chadlindell/terrascry/hirt/docs/build-guide/electronics.qmd

---
title: "Electronics and Circuits"
---

## Overview {#sec-electronics-overview}

This section consolidates all circuit designs for the HIRT system, including the MIT (Magneto-Inductive Tomography) circuits, ERT (Electrical Resistivity Tomography) circuits, and base hub electronics. The design uses **centralized electronics with passive probes**: all active components reside in the surface hub, while probes contain only coils and electrodes.

This architecture offers significant advantages: lower per-probe cost, easier maintenance, better reliability (passive probes are more robust), centralized firmware updates, and simplified probe construction. The trade-off is increased cabling complexity for the multi-probe harness.

::: {.callout-tip}
## Hardware Documentation Reference

Complete circuit schematics and detailed design notes are maintained in the hardware documentation:

- **MIT Circuit:** `/hardware/schematics/electronics/mit-circuit.md` - Full TX/RX chain design with component values
- **ERT Circuit:** `/hardware/schematics/electronics/ert-circuit.md` - Howland current source and measurement circuits
- **Base Hub Circuit:** `/hardware/schematics/electronics/base-hub-circuit.md` - Central hub electronics integration
- **Block Diagrams:** `/hardware/schematics/electronics/probe-electronics-block.md` - System-level block diagrams

The diagrams in this section provide conceptual overviews; refer to the hardware schematics for exact component values and PCB layout guidance.
:::

## System Block Diagram {#sec-system-block}

```{python}
#| label: fig-system-block-elec
#| fig-cap: "Complete HIRT system architecture showing the central electronics hub, zone wiring strategy, and passive probe connections. All signal processing occurs in the hub; probes are purely passive sensors."
#| fig-width: 11
#| fig-height: 7
#| code-fold: true

import sys; sys.path.insert(0, '..') if '..' not in sys.path else None
from diagrams.circuits import create_system_block_diagram
import matplotlib.pyplot as plt
from PIL import Image

buf = create_system_block_diagram()
img = Image.open(buf)
plt.figure(figsize=(11, 7))
plt.imshow(img)
plt.axis('off')
plt.tight_layout()
plt.show()
```

The central hub contains: (1) MCU for control and DSP, (2) MIT transmitter chain (DDS + power driver), (3) MIT receiver chain (preamp + instrumentation amplifier + ADC), (4) ERT current source and voltage measurement, and (5) high-density analog multiplexers. These connect via DB25 trunk cables to passive **Zone Hubs**, which then distribute signals to individual probes.

## MIT Transmit (TX) Chain {#sec-mit-tx}

```{python}
#| label: fig-mit-tx-chain
#| fig-cap: "MIT transmitter signal chain from MCU through DDS, filtering, and power driver to the TX coil. Operating frequency range is 2-50 kHz."
#| fig-width: 10
#| fig-height: 4
#| code-fold: true

import sys; sys.path.insert(0, '..') if '..' not in sys.path else None
from diagrams.circuits import create_mit_tx_chain
import matplotlib.pyplot as plt
from PIL import Image

buf = create_mit_tx_chain()
img = Image.open(buf)
plt.figure(figsize=(10, 4))
plt.imshow(img)
plt.axis('off')
plt.tight_layout()
plt.show()
```

## DDS Sine Generator {#sec-dds}

The transmit chain begins with a Direct Digital Synthesis (DDS) generator, the **AD9833**. This IC provides a highly precise sine wave output from 0.1 Hz to 12.5 MHz with 28-bit frequency resolution. Its compact MSOP-10 footprint and low power consumption make it ideal for the 2-50 kHz HIRT operating range.

| Parameter | Specification |
|---|---|
| Part Number | **AD9833BRMZ** |
| Frequency Range | 0 Hz to 12.5 MHz |
| Output Level | 0.6 V p-p sine wave |
| Interface | SPI (3-wire) |
| Resolution | 28-bit frequency, 12-bit phase |
| Power Supply | 2.3-5.5V, 12.65 mW typical |

: AD9833 DDS Generator Specifications. {#tbl-dds-specs}

## TX Power Driver {#sec-tx-driver}

The DDS output is buffered by a **Texas Instruments OPA2186** precision operational amplifier. This component is selected for its zero-drift architecture and ultra-low quiescent current (**90 µA** **(Modeled)**), which ensures high precision and extended battery life for the hub while maintaining rail-to-rail output for the TX coil drive.

| Parameter | OPA2186 Specification |
|---|---|
| Quiescent Current | **90 µA** |
| Drift | **0.04 µV/°C** (Zero-Drift) |
| Offset Voltage | 10 µV |
| Power Supply | 4.5V to 36V |

: TX Driver Op-Amp Specifications. {#tbl-tx-driver}

## MIT Receive (RX) Chain {#sec-mit-rx}

```{python}
#| label: fig-mit-rx-chain
#| fig-cap: "MIT receiver signal chain. The updated 2026 architecture uses the AD8421 for ultra-low noise preamplification (3 nV/rtHz), followed by the integrated AD7124-8 AFE."
#| fig-width: 10
#| fig-height: 4
#| code-fold: true

import sys; sys.path.insert(0, '..') if '..' not in sys.path else None
from diagrams.circuits import create_mit_rx_chain
import matplotlib.pyplot as plt
from PIL import Image

buf = create_mit_rx_chain()
img = Image.open(buf)
plt.figure(figsize=(10, 4))
plt.imshow(img)
plt.axis('off')
plt.tight_layout()
plt.show()
```

## RX Preamplifier (AD8421) {#sec-rx-preamp}

The receiver front-end utilizes the **Analog Devices AD8421**. This high-speed instrumentation amplifier features an exceptionally low input voltage noise floor of **3 nV/$\sqrt{\mathrm{Hz}}$** **(Modeled)**. This performance characteristic is essential for resolving the weak secondary magnetic fields generated by subsurface targets in the MIT tomography process.

| Parameter | Specification |
|---|---|
| Component | **AD8421** |
| Input Noise | **3 nV/$\sqrt{\mathrm{Hz}}$** **(Modeled)** |
| Bandwidth (G=10) | 10 MHz |
| Slew Rate | 35 V/µs |
| Supply Current | 2.0 mA |

: RX Preamplifier Specifications. {#tbl-preamp-specs}

### Zero-Drift Alternative: INA188 {#sec-ina188-alternative}

For applications prioritizing DC stability over AC noise floor, the **Texas Instruments INA188** provides a zero-drift alternative to the AD8421.

| Parameter | AD8421 | INA188 | Trade-off |
|---|---|---|---|
| Noise Floor | **3 nV/$\sqrt{\mathrm{Hz}}$** | 12 nV/$\sqrt{\mathrm{Hz}}$ | AD8421 superior for AC |
| Offset Drift | 0.6 µV/°C | **0.2 µV/°C** | INA188 superior for DC |
| 1/f Noise | Present | **Eliminated** | INA188 better at DC |
| Supply Current | 2.0 mA | 1.4 mA | Similar |

: AD8421 vs INA188 comparison. {#tbl-preamp-comparison}

**Recommendation:** For HIRT's MIT operating range (2-50 kHz), the AD8421's ultra-low broadband noise provides better SNR than the INA188's zero-drift architecture. Use the INA188 only if your application requires DC-accurate measurements or operates below 100 Hz.

### Noise Floor Measurement Conditions {#sec-noise-conditions}

The AD8421's specified noise floor of **3 nV/$\sqrt{\mathrm{Hz}}$** is achieved under specific measurement conditions. Field performance depends on several factors:

| Condition | Specification | Field Typical | Impact on SNR |
|---|---|---|---|
| Bandwidth | 1-50 kHz (HIRT operating range) | 2-50 kHz | ~100 nV RMS integrated |
| Temperature | 25°C reference | -10 to +40°C | ±10% variation |
| Cable length | <1 m bench test | 3-5 m probe cable | +20-50% noise pickup |
| Averaging | 100-sample mean | 16-64 samples typical | Improves by $\sqrt{N}$ |

: Noise floor measurement conditions and field impact. {#tbl-noise-conditions}

**Integrated Noise Calculation:** For a 1-50 kHz bandwidth (49 kHz span), the theoretical integrated input-referred noise is:

$$V_{n,rms} = 3\ \text{nV}/\sqrt{\text{Hz}} \times \sqrt{49,000\ \text{Hz}} \approx 100\ \text{nV RMS}$$

This represents the *design target* under controlled conditions. Field measurements typically show 150-300 nV RMS due to cable capacitance, EMI pickup, and connector losses.

::: {.callout-note}
## Performance Claim Context

The ~100 nV noise floor is a **design target** based on component specifications and bench measurements. Actual field performance varies with environmental conditions and cable routing. For planning purposes, assume 200-300 nV RMS input-referred noise in typical outdoor conditions.
:::

## Signal Conditioning and Gain Stage {#sec-signal-conditioning}

Following the AD8421 preamplifier, the signal passes through additional gain and filtering stages before reaching the ADC. An instrumentation amplifier (INA128) provides adjustable gain to match signal levels to the ADC input range. The total signal chain gain is typically 800-1000x, bringing microvolt-level coil signals up to the millivolt range required by the ADC.

## Signal Level Progression {#sec-signal-levels}

```{python}
#| label: fig-signal-level
#| fig-cap: "Signal level progression through the MIT RX chain. The signal starts at approximately 1 uV at the coil and is amplified to 0.8 mV at the ADC input. The noise floor also rises but at a slower rate, maintaining adequate SNR."
#| fig-width: 10
#| fig-height: 5
#| code-fold: true

import sys; sys.path.insert(0, '..') if '..' not in sys.path else None
from diagrams.circuits import create_signal_level_progression
import matplotlib.pyplot as plt
from PIL import Image

buf = create_signal_level_progression()
img = Image.open(buf)
plt.figure(figsize=(10, 5))
plt.imshow(img)
plt.axis('off')
plt.tight_layout()
plt.show()
```

## Lock-In Detection {#sec-lockin}

Lock-in detection is essential for extracting weak MIT signals from noise. The HIRT system uses **digital lock-in detection** implemented in the MCU, which offers flexibility, software configurability, and no analog drift. The technique multiplies the received signal by reference sine and cosine waveforms at the excitation frequency, then low-pass filters to extract the in-phase (I) and quadrature (Q) components.

```{python}
#| label: fig-lockin-detection
#| fig-cap: "Digital lock-in detection block diagram. The RX signal is multiplied by reference sine (Q-channel) and cosine (I-channel) signals, then filtered and integrated. Amplitude A = sqrt(I^2 + Q^2) and phase Phi = atan2(Q,I) are computed from the I/Q outputs."
#| fig-width: 10
#| fig-height: 5
#| code-fold: true

import sys; sys.path.insert(0, '..') if '..' not in sys.path else None
from diagrams.circuits import create_lock_in_detection_diagram
import matplotlib.pyplot as plt
from PIL import Image

buf = create_lock_in_detection_diagram()
img = Image.open(buf)
plt.figure(figsize=(10, 5))
plt.imshow(img)
plt.axis('off')
plt.tight_layout()
plt.show()
```

The lock-in algorithm provides exceptional noise rejection (> 40 dB improvement) by responding only to signals at the exact reference frequency. This allows detection of MIT signals buried deep in noise, critical for weak responses from distant or low-conductivity targets.

## Digital Lock-In Algorithm {#sec-lockin-algorithm}

```c
// Simplified digital lock-in implementation
float I_sum = 0, Q_sum = 0;
for (int i = 0; i < N_samples; i++) {
    float sample = read_adc();
    float ref_I = sin(2 * PI * f * i / Fs);
    float ref_Q = cos(2 * PI * f * i / Fs);
    I_sum += sample * ref_I;
    Q_sum += sample * ref_Q;
}
float amplitude = sqrt(I_sum*I_sum + Q_sum*Q_sum) / N_samples;
float phase = atan2(Q_sum, I_sum);
```

## ERT Current Source (Howland Pump) {#sec-ert-current}

The ERT subsystem injects controlled current into the ground through electrode rings and measures the resulting voltage distribution. The current source uses a **Howland current pump** topology, which provides high output impedance (>1 M-ohm) and stable current regardless of load variations.

```{python}
#| label: fig-ert-current-source
#| fig-cap: "Howland current pump circuit for ERT measurements. When R1=R2=R3=R4, the output current is I_out = V_in / R_sense, independent of load impedance. A precision 2.5V reference (REF5025) provides stable input voltage."
#| fig-width: 10
#| fig-height: 6
#| code-fold: true

import sys; sys.path.insert(0, '..') if '..' not in sys.path else None
from diagrams.circuits import create_ert_current_source
import matplotlib.pyplot as plt
from PIL import Image

buf = create_ert_current_source()
img = Image.open(buf)
plt.figure(figsize=(10, 6))
plt.imshow(img)
plt.axis('off')
plt.tight_layout()
plt.show()
```

| Parameter | Specification |
|---|---|
| Output Current | 0.5-2 mA (adjustable) |
| Current Accuracy | +/- 5% |
| Compliance Voltage | +/- 10V minimum |
| Output Impedance | > 1 M-ohm |
| Load Range | 100 ohm - 10 k-ohm |
| Polarity Reversal | Programmable (0.5 Hz) |

: ERT Current Source Specifications. {#tbl-ert-current}

### Compliance Voltage vs Load {#sec-ert-compliance}

The +/-10V compliance voltage determines the maximum load impedance at each current setting. Operators should select current levels based on expected soil resistivity to ensure adequate measurement headroom:

| Max Current | Max Load at 10V | Typical Application |
|---|---|---|
| 2.0 mA | 5 k-ohm | Low resistivity soil (<100 ohm-m) |
| 1.0 mA | 10 k-ohm | Medium resistivity (100-500 ohm-m) |
| 0.5 mA | 20 k-ohm | High resistivity (>500 ohm-m) |

: ERT current vs load compliance limits. Higher resistivity soils require lower current to stay within compliance voltage. {#tbl-ert-compliance}

::: {.callout-warning}
## Compliance Limit Warning

If the load impedance exceeds the compliance limit for the selected current, the current source will saturate and actual injected current will be less than commanded. The ERT firmware monitors this condition and flags affected measurements. Reduce current setting or improve electrode contact if compliance warnings occur frequently.
:::

## Polarity Reversal {#sec-polarity-reversal}

Electrode polarization causes measurement drift in DC systems. To mitigate this, HIRT reverses the current polarity every 2 seconds using a DPDT relay (G5V-2-H1) or solid-state switch (ADG1219). Positive and negative measurements are averaged to cancel polarization effects.

```{python}
#| label: fig-polarity-reversal
#| fig-cap: "ERT polarity reversal circuit using a DPDT relay. The relay alternates current direction between Ring A and Ring B every 2 seconds, eliminating electrode polarization artifacts from the measurement."
#| fig-width: 8
#| fig-height: 5
#| code-fold: true

import sys; sys.path.insert(0, '..') if '..' not in sys.path else None
from diagrams.circuits import create_ert_polarity_reversal
import matplotlib.pyplot as plt
from PIL import Image

buf = create_ert_polarity_reversal()
img = Image.open(buf)
plt.figure(figsize=(8, 5))
plt.imshow(img)
plt.axis('off')
plt.tight_layout()
plt.show()
```

## ADC Interface {#sec-adc}

```{python}
#| label: fig-adc-interface
#| fig-cap: "AD7124-8 ADC interface showing differential analog inputs for MIT and ERT signals, SPI connection to MCU, and integrated reference. The integrated AFE, 24-bit resolution, and three power modes provide excellent dynamic range with minimal external components."
#| fig-width: 9
#| fig-height: 5
#| code-fold: true

import sys; sys.path.insert(0, '..') if '..' not in sys.path else None
from diagrams.circuits import create_adc_interface_diagram
import matplotlib.pyplot as plt
from PIL import Image

buf = create_adc_interface_diagram()
img = Image.open(buf)
plt.figure(figsize=(9, 5))
plt.imshow(img)
plt.axis('off')
plt.tight_layout()
plt.show()
```

The HIRT Rev B design uses the **Analog Devices AD7124-8** as the primary ADC. This integrated Analog Front End (AFE) dramatically reduces external component count compared to the legacy ADS1256, while providing superior power management for field deployment.

| Parameter | AD7124-8 Specification |
|---|---|
| Resolution | 24 bits |
| Sample Rate | Up to 19.2 kSPS |
| Noise | 24 nV RMS (at low output rates) |
| Interface | SPI |
| Integrated Features | Rail-to-rail buffer, PGA (1-128x), reference buffers |
| Power Modes | Full (970 µA), Mid (660 µA), **Low (255 µA)** **(Modeled)** |
| Input Channels | 8 differential or 15 single-ended |

: AD7124-8 ADC Specifications (Rev B Primary). {#tbl-adc-specs}

**Migration Note (Rev A to Rev B):** The AD7124-8 replaces the ADS1256 as the recommended ADC. Key advantages:

- **Integrated AFE:** Internal rail-to-rail buffer and reference buffers eliminate ~6 external components
- **Power efficiency:** Low-power mode (~255 µA) vs ADS1256 (~36 mW) enables significantly longer battery life
- **Comparable noise:** 24 nV RMS achievable with fewer external noise sources

The ADS1256 remains documented for legacy builds (see [Legacy Components](#sec-legacy-components)).

## Multiplexer Switching {#sec-multiplexer}

With up to 24 probes in a typical array, the HIRT system requires a scalable multiplexing strategy. The design uses **CD74HC4067** 16:1 analog multiplexers controlled by MCU GPIO pins. Each TX and RX signal path has its own multiplexer, allowing independent selection of transmit and receive probes. For arrays exceeding 16 probes, cascaded multiplexers can be used.

```{python}
#| label: fig-mux-switching
#| fig-cap: "Multiplexer switching topology for probe selection. Separate TX and RX multiplexers allow any TX-RX probe combination to be measured. MCU GPIO controls multiplexer address lines (A0-A2)."
#| fig-width: 10
#| fig-height: 6
#| code-fold: true

import sys; sys.path.insert(0, '..') if '..' not in sys.path else None
from diagrams.circuits import create_multiplexer_switching_diagram
import matplotlib.pyplot as plt
from PIL import Image

buf = create_multiplexer_switching_diagram()
img = Image.open(buf)
plt.figure(figsize=(10, 6))
plt.imshow(img)
plt.axis('off')
plt.tight_layout()
plt.show()
```

## Power Distribution {#sec-power}

```{python}
#| label: fig-power-distribution
#| fig-cap: "Power distribution from 12V battery through regulators to various subsystems. Total system current is approximately 200 mA, providing several hours of operation from a 3S LiPo battery."
#| fig-width: 10
#| fig-height: 5
#| code-fold: true

import sys; sys.path.insert(0, '..') if '..' not in sys.path else None
from diagrams.circuits import create_power_distribution
import matplotlib.pyplot as plt
from PIL import Image

buf = create_power_distribution()
img = Image.open(buf)
plt.figure(figsize=(10, 5))
plt.imshow(img)
plt.axis('off')
plt.tight_layout()
plt.show()
```

| Rail | Voltage | Current | Purpose |
|---|---|---|---|
| +12V (Battery) | 11.1-12.6V | 200 mA total | System input |
| +5V (LDO) | 5.0V | 50 mA | Power driver, references |
| +3.3V (LDO) | 3.3V | 100 mA | MCU, ADC, digital |
| -5V (Charge pump) | -5.0V | 10 mA | Op-amp negative rail |

: Power Rail Specifications. {#tbl-power-rails}

## Noise Filtering Stages {#sec-noise-filtering}

```{python}
#| label: fig-noise-filtering
#| fig-cap: "Cascaded noise filtering stages in the signal chain. Each stage targets specific noise sources: EMI, DC offsets, wideband noise, aliasing, and quantization noise. Combined rejection exceeds 60 dB."
#| fig-width: 10
#| fig-height: 4
#| code-fold: true

import sys; sys.path.insert(0, '..') if '..' not in sys.path else None
from diagrams.circuits import create_noise_filtering_diagram
import matplotlib.pyplot as plt
from PIL import Image

buf = create_noise_filtering_diagram()
img = Image.open(buf)
plt.figure(figsize=(10, 4))
plt.imshow(img)
plt.axis('off')
plt.tight_layout()
plt.show()
```

Noise reduction is critical for MIT measurements where signal levels can be in the microvolt range. The filtering strategy employs multiple stages:

- **Input RC filter (fc=100kHz):** Blocks RF interference and high-frequency EMI
- **High-pass filter (fc=100Hz):** Removes DC offsets and 60Hz pickup
- **Active band-pass (1-50kHz):** Passes only the measurement band
- **Anti-aliasing filter (fc=15kHz):** Prevents aliasing in ADC sampling
- **Digital matched filter:** Optimizes SNR in post-processing

## Shielding and Ground Loop Prevention {#sec-grounding}

```{python}
#| label: fig-ground-loop
#| fig-cap: "Ground loop prevention techniques. (a) shows the problem: multiple ground paths create loops that pick up EMI. (b) shows the solution: star grounding with a single connection point eliminates loops."
#| fig-width: 10
#| fig-height: 5
#| code-fold: true

import sys; sys.path.insert(0, '..') if '..' not in sys.path else None
from diagrams.circuits import create_ground_loop_prevention
import matplotlib.pyplot as plt
from PIL import Image

buf = create_ground_loop_prevention()
img = Image.open(buf)
plt.figure(figsize=(10, 5))
plt.imshow(img)
plt.axis('off')
plt.tight_layout()
plt.show()
```

Proper grounding is essential for achieving low-noise measurements. The HIRT design follows these best practices:

- **Star grounding:** All ground returns connect at a single point near the ADC
- **Separate ground planes:** Analog and digital grounds are split on the PCB
- **Shielded cables:** All signal cables use twisted-pair with overall shield
- **Single-point shield termination:** Shields grounded at hub end only
- **Minimum loop area:** Signal and return paths routed together

## PCB Layout Guidelines {#sec-pcb-layout}

```{python}
#| label: fig-pcb-layout
#| fig-cap: "Recommended PCB layout showing component placement zones. The analog section (shielded) is physically separated from digital circuits. Ground plane spans the bottom layer with analog/digital split connected at a star point."
#| fig-width: 10
#| fig-height: 6
#| code-fold: true

import sys; sys.path.insert(0, '..') if '..' not in sys.path else None
from diagrams.circuits import create_component_location_diagram
import matplotlib.pyplot as plt
from PIL import Image

buf = create_component_location_diagram()
img = Image.open(buf)
plt.figure(figsize=(10, 6))
plt.imshow(img)
plt.axis('off')
plt.tight_layout()
plt.show()
```

## Layout Rules {#sec-layout-rules}

1. Place bypass capacitors (100nF) within 5mm of each IC power pin
2. Route analog signals with minimum trace length; avoid crossing digital signals
3. Use differential pairs for RX coil signals with matched length
4. Keep TX and RX signal paths physically separated (>10mm)
5. Provide shielding (copper pour) around sensitive analog circuits
6. Use wide traces (>20 mil) for power distribution
7. Connect analog and digital ground planes at a single star point near the ADC

## Key Component Summary {#sec-components}

| Component | Part Number | Function | Package | Rev |
|---|---|---|---|-----|
| DDS | AD9833BRMZ | Signal generator | MSOP-10 | A/B |
| TX Driver | OPA454AIDDAR | Coil driver | SOIC-8 | A/B |
| Preamp | AD8421BRZ | RX preamplifier | SOIC-8 | A/B |
| Preamp (Alt) | INA188ID | Zero-drift preamp | SOIC-8 | B |
| Inst Amp | INA128PAG4 | Gain stage | DIP-8 | A/B |
| ADC | **AD7124-8BRUZ** | 24-bit integrated AFE | TQFP-32 | **B** |
| ADC (Legacy) | ADS1256IDBR | 24-bit ADC | SSOP-28 | A |
| Multiplexer | CD74HC4067M | 16-channel mux | SOIC-24 | A/B |
| MCU | ESP32-WROOM-32 | Controller | Module | A/B |
| V-Reference | REF5025AIDGKR | 2.5V reference | SOIC-8 | A/B |
| LDO | AMS1117-3.3 | 3.3V regulator | SOT-223 | A/B |
| Connector | **Weipu SP29-26** | IP68 hub connector | Circular | **B** |
| Connector (Legacy) | DB25 | Hub connector | D-Sub | A |

: Key IC Components (Rev B highlighted in bold). {#tbl-components}

## Connector Pinouts (Probe-to-Zone) {#sec-pinouts}

| Pin | Signal | Description |
|-----|---|---|
| 1 | TX+ | To probe TX coil |
| 2 | TX- | Return path |
| 3 | RX+ | Differential RX |
| 4 | RX- | Differential RX return |
| 5 | Guard | Analog ground |
| 6 | Ring A | Upper ERT electrode |
| 7 | Ring B | Mid ERT electrode |
| 8 | Ring C | Deep electrode |
| 9 | ID Sense | Auto-ID resistor |
| 10-11 | Spare | Reserved |
| 12 | Shield | Cable shield clamp |

: 12-pin Probe Connector Pinout. {#tbl-pinout}

## Firmware Status {#sec-firmware-status}

::: {.callout-note}
## Firmware Development - Phase 2

The hardware system documented in this whitepaper requires MCU firmware to operate. Firmware development is explicitly **Phase 2** of the project, separate from the hardware design presented here.

**Current Status:**

- Hardware is designed for ESP32-WROOM-32 MCU
- No firmware repository is published yet
- Planned firmware features: DDS control, ADC sampling, lock-in detection, USB data logging

**Planned Repository:** `github.com/hirt-project/hirt-firmware` (future)

Builders can test hardware subsystems (coils, ERT source, ADC) using bench equipment before firmware is available. See Section 18 for the software development roadmap.
:::

## Safety Considerations {#sec-safety}

::: {.callout-warning}
## ELECTRICAL SAFETY

- Maximum output current limited to 5 mA by design
- Compliance voltage restricted to +/-12V (safe for soil contact)
- Include 10 mA fast-blow fuse on ERT output
- Use opto-isolated relay control for polarity switching
- Ensure proper earth ground connection for safety
:::

## Troubleshooting Guide {#sec-elec-troubleshooting}

| Symptom | Likely Cause | Solution |
|---|---|---|
| No TX output | DDS not initialized | Check SPI connection, verify clock |
| Weak RX signal | Gain too low | Verify R~G~ resistor, check amplifier rails |
| Noisy readings | Ground loops | Implement star grounding, shield cables |
| No ERT current | Open circuit | Check electrode contact, verify relay state |
| Current drift | Reference unstable | Verify Vref output, add bypass caps |
| ADC errors | SPI timing | Reduce SPI clock speed, check DRDY timing |

: Common Issues and Solutions. {#tbl-troubleshooting}

## Interconnect Modernization {#sec-interconnect}

The Rev B design replaces the legacy DB25 connectors with **Weipu SP29 (26-pin)** IP68-rated circular connectors. This addresses field reliability issues with non-waterproof D-Sub interfaces.

### Weipu SP29 Specifications

| Parameter | Specification |
|---|---|
| Pin Count | 26 pins (matches DB25 + 1 spare) |
| IP Rating | **IP68** (waterproof, dust-tight) |
| Coupling | Threaded (vibration-resistant) |
| Panel Cutout | 29 mm |
| Current Rating | 5 A per contact |
| Shell Material | Nylon66 (rugged, cost-effective) |
| Termination | Solder |

: Weipu SP29 connector specifications. {#tbl-sp29-specs}

**Migration Note:** The SP29's 26-pin configuration directly accommodates all 25 DB25 signals with one spare pin for future expansion. The threaded coupling provides a secure, watertight seal superior to the DB25's thumbscrew retention.

### Alternative: CNLINKO LP-24

For applications requiring faster connection/disconnection, the CNLINKO LP-24 with snap-lock mechanism is acceptable but provides only 24 pins (requires reducing conductor count by one).

## Electronics Modernization Roadmap {#sec-modernization}

The Rev B design already incorporates several key component upgrades: the AD8421 preamplifier and AD7124-8 integrated AFE replace legacy discrete solutions, and the Weipu SP29 connector provides IP68 environmental protection. Our ongoing component research identifies additional optimization opportunities for future board revisions.

We tracked electronics modernization opportunities through systematic component research focused on power efficiency, footprint reduction, and second-source availability. The Rev B design already benefits from the AD8421's 3 nV/rtHz noise floor and the AD7124-8's integrated AFE architecture. The following table summarizes additional upgrades under consideration:

| Component | Current (Rev B) | Recommended Upgrade | Benefit | Status |
|---|---|---|---|---|
| **DDS** | AD9833 (MSOP-10) | **AD9837** (LFCSP 3x3mm) | 33% power reduction (8.5 mW vs 12.65 mW), smaller footprint | **(Modeled)** |
| **TX Driver** | OPA2186 | Already optimized | 89% power vs OPA2277 (90 µA vs 800 µA) | **(Modeled)** |
| **Connector** | Weipu SP29 | Already upgraded | IP68 rating, 26-pin, rugged | Implemented |
| **ADC** | AD7124-8 | ADS1261 (TI alternative) | Second source, 0.34 µV RMS noise, comparable specs | **(Modeled)** |

: Electronics modernization summary. Rev B incorporates AD8421 and AD7124-8; additional upgrades are under evaluation. {#tbl-modernization}

**DDS Upgrade Path: AD9837.** The AD9837 is a pin-compatible upgrade to the AD9833, offering identical SPI control and frequency generation capabilities in a smaller LFCSP-16 package (3x3 mm vs MSOP-10 footprint). The power reduction from 12.65 mW to 8.5 mW may extend battery life in multi-channel deployments. We classify this as a low-risk enhancement suitable for future PCB spins.

**ADC Second Source: ADS1261.** While the AD7124-8 remains our primary recommendation, the Texas Instruments ADS1261 provides comparable performance (0.34 µV RMS noise, 24-bit resolution, integrated PGA) within the TI ecosystem. This offers supply chain diversity and may be preferable for teams already standardized on TI components.

::: {.callout-tip}
## Pre-Order Component Strategy

Electronic component markets are volatile. Tariff announcements in late 2025 suggest potential 20-30% price increases for imports in 2026. For builders planning multi-unit production, we recommend pre-ordering AD8421, AD7124-8, and AD9833/AD9837 stock now to lock in current pricing. Store ICs in sealed moisture-barrier bags with desiccant.
:::

## Legacy Components (Deprecated) {#sec-legacy-components}

The following components are documented for historical builds and maintenance of Rev A systems. **New builds should use Rev B components.**

### ADS1256 (Legacy ADC)

| Parameter | ADS1256 Specification |
|---|---|
| Resolution | 24 bits |
| Sample Rate | 30 kSPS maximum |
| Noise | 0.6 µV RMS (at 100 SPS) |
| Interface | SPI |
| Internal PGA | 1, 2, 4, 8, 16, 32, 64x |
| Input Channels | 8 single-ended or 4 differential |
| Power | ~36 mW typical |

: ADS1256 ADC Specifications (Legacy - Not Recommended for New Builds). {#tbl-adc-legacy}

::: {.callout-warning}
## Legacy Component - Not Maintained

The ADS1256 requires significant external circuitry (reference buffers, input drivers) to achieve datasheet performance, increasing PCB footprint and power budget. New builds should use the AD7124-8, which integrates these functions and offers superior power efficiency.
:::

### DB25 Connector (Legacy Interconnect)

The DB25 connector is not waterproof and is prone to corrosion in field environments. Rev B replaces this with the Weipu SP29 IP68 connector. Existing systems can continue using DB25 but should add environmental protection (conformal coating, protective caps) for field use.

## References {#sec-electronics-references}

1. Analog Devices. AD9833 Programmable Waveform Generator Data Sheet. Rev. F, 2019. [Datasheet](https://www.analog.com/media/en/technical-documentation/data-sheets/AD9833.pdf)

2. Texas Instruments. OPA454 High-Voltage, High-Current Operational Amplifier. SBOS328D, 2018. [Datasheet](https://www.ti.com/lit/ds/symlink/opa454.pdf)

3. Analog Devices. AD620 Low Cost, Low Power Instrumentation Amplifier. Rev. H, 2011. [Datasheet](https://www.analog.com/media/en/technical-documentation/data-sheets/AD620.pdf)

4. Texas Instruments. INA128 Precision, Low Power Instrumentation Amplifiers. SBOS051B, 2005. [Datasheet](https://www.ti.com/lit/ds/symlink/ina128.pdf)

5. Texas Instruments. ADS1256 Very Low Noise, 24-Bit Analog-to-Digital Converter. SBAS288K, 2013. [Datasheet](https://www.ti.com/lit/ds/symlink/ads1256.pdf)

6. Horowitz, P. and Hill, W. (2015). *The Art of Electronics*, 3rd Edition. Cambridge University Press. Chapter 5: Precision Circuits. [DOI: 10.1017/CBO9781139644204](https://doi.org/10.1017/CBO9781139644204)

7. Ott, H.W. (2009). *Electromagnetic Compatibility Engineering*. Wiley. Chapter 3: Grounding. [DOI: 10.1002/9780470508510](https://doi.org/10.1002/9780470508510)
