chadlindell/terrascry/hirt/docs/build-guide/mechanical.qmd

---
title: "Mechanical Design"
---

## Overview {#sec-mech-overview}

This section consolidates all mechanical design specifications for the HIRT probe system, including the micro-probe architecture, rod specifications, component drawings, and manufacturing procedures for 3D printed parts. The design philosophy prioritizes minimal ground disturbance while maintaining robust measurement capability.

::: {.callout-tip}
## Hardware Documentation Reference

CAD files, manufacturing guides, and detailed drawings are maintained in the hardware documentation:

- **CAD Files:** `/hardware/cad/` - OpenSCAD source files and STL exports
- **Manufacturing Guide:** `/hardware/cad/docs/manufacturing-guide.md` - Printing settings and post-processing
- **Probe Assembly:** `/hardware/schematics/mechanical/probe-assembly.md` - Detailed assembly drawings
- **Rod Specifications:** `/hardware/schematics/mechanical/rod-specifications.md` - Material and dimensional specifications
- **ERT Ring Mounting:** `/hardware/schematics/mechanical/er-ring-mounting.md` - Electrode installation details

See `/hardware/cad/QUICKSTART.md` for getting started with the CAD files.
:::

## Design Philosophy {#sec-mech-design-philosophy}

**"Archaeologist brain first, engineer brain second"** - This guiding principle shapes every aspect of the HIRT mechanical design. The goal is to create the smallest possible hole while retaining enough physics (coil area, electrode contact) for quality signals. The constraint leads to many thin, gentle holes rather than few large ones, resulting in approximately 10x less disturbance than conventional designs.

## Core Design Principles {#sec-core-principles}

- **No big electronics at the tip:** PCBs, ADCs, MCUs stay at surface. Only passive components downhole.
- **Probes are mostly passive:** Downhole contains only coils and electrodes plus thin wiring. All "smart" electronics reside in junction box above ground.
- **Rod diameter standard: 16mm OD (Target):** Robust hiking pole standard allowing strong M12 threads. Hole size of 18-20mm (Target) is much less destructive than traditional 50mm.

```{python}
#| label: fig-exploded-assembly
#| fig-cap: "Probe assembly exploded view showing the modular construction with M12x1.75 (Manufacturer spec) threaded connections. Components from bottom: probe tip, rod segments with integrated coils, ERT ring collars, and surface junction box. All parts screw together for field assembly."
#| fig-width: 8
#| fig-height: 10
#| code-fold: true

import sys; sys.path.insert(0, '..') if '..' not in sys.path else None
from diagrams.mechanical import create_exploded_assembly
import matplotlib.pyplot as plt
from PIL import Image

buf = create_exploded_assembly()
img = Image.open(buf)
plt.figure(figsize=(8, 10))
plt.imshow(img)
plt.axis('off')
plt.tight_layout()
plt.show()
```

## Disturbance Comparison {#sec-disturbance-comparison}

The micro-probe design achieves dramatic reduction in soil disturbance compared to traditional geophysical probes. A 16mm (Target) rod requires only an 18-20mm (Target) hole, with cross-sectional area of approximately 2.5-3.1 cm^2^ (Modeled) ($\pi \times 1.0^2$ cm). At 3m depth, this creates only 0.75-0.93 liters (Modeled) of displacement per hole. In contrast, traditional 25mm rods requiring 50mm holes produce cross-sectional area of approximately 19.6 cm^2^ (Modeled) ($\pi \times 2.5^2$ cm), displacing approximately 5.9 liters (Modeled) per hole at 3m depth. This represents a **6-7x reduction** (Modeled) in soil disturbance volume with the HIRT micro-probe design.

```{python}
#| label: fig-disturbance-comparison
#| fig-cap: "Soil disturbance comparison between HIRT micro-probe (16mm) (Target) and traditional probe (25mm). The dashed lines indicate the disturbed zone extent. The 16mm (Target) design achieves approximately 85% (Modeled) less soil disturbance volume (6-7x (Modeled) reduction), critical for archaeological site preservation."
#| fig-width: 10
#| fig-height: 5
#| code-fold: true

import sys; sys.path.insert(0, '..') if '..' not in sys.path else None
from diagrams.mechanical import create_disturbance_comparison
import matplotlib.pyplot as plt
from PIL import Image

buf = create_disturbance_comparison()
img = Image.open(buf)
plt.figure(figsize=(10, 5))
plt.imshow(img)
plt.axis('off')
plt.tight_layout()
plt.show()
```

## Key Dimensions {#sec-key-dimensions}

| Component | Dimension | Notes |
|---|---|---|
| Rod OD | 16 mm (Target) | Increased from 12mm for strength |
| Rod ID | 12-13 mm (Manufacturer spec) | Standard pultruded tube |
| Wall Thickness | 1.5-2.0 mm (Manufacturer spec) | Structural requirement |
| Segment Length | 50, 100 cm (Target) | Defines sensor spacing |
| Hole Size | 18-20 mm (Target) | For 16mm rod insertion |
| Total Length | 2.5-3.0 m (Target) | Multiple segments assembled |

: Key dimensional specifications for the HIRT micro-probe system. {#tbl-dimensions}

## Rod Segments and Couplers {#sec-rod-segments}

## Rod Material Selection {#sec-material-selection}

Material selection is critical for probe performance. The rod must be non-conductive to avoid interference with electromagnetic measurements, strong enough to withstand insertion forces, and durable for repeated field use. Fiberglass (G10) emerges as the preferred material due to its combination of high strength, non-conductivity, RF transparency, and moderate cost.

```{python}
#| label: fig-material-specs
#| fig-cap: "Material selection guide for probe rod construction. Fiberglass (G10) is the preferred material offering the best balance of strength, non-conductivity, and cost. Metal rods must be avoided as they interfere with electromagnetic measurements."
#| fig-width: 10
#| fig-height: 6
#| code-fold: true

import sys; sys.path.insert(0, '..') if '..' not in sys.path else None
from diagrams.mechanical import create_material_specs_diagram
import matplotlib.pyplot as plt
from PIL import Image

buf = create_material_specs_diagram()
img = Image.open(buf)
plt.figure(figsize=(10, 6))
plt.imshow(img)
plt.axis('off')
plt.tight_layout()
plt.show()
```

| Parameter | Specification |
|---|---|
| Outer Diameter (OD) | 16 mm (Target) (approx. 5/8") |
| Inner Diameter (ID) | 12-13 mm (Manufacturer spec) |
| Wall Thickness | ~1.5-2.0 mm (Manufacturer spec) |
| Material | Fiberglass (non-conductive, RF transparent) |
| Segment Lengths | 50 cm, 100 cm (Target) (spacers) |

: Fiberglass rod specifications. {#tbl-fiberglass}

## Modular Connector System {#sec-modular-connector}

The system uses a 2-part connector system permanently epoxied into rod ends to create a screw-together stack. The male insert provides the threaded portion while the female insert/sensor module receives the thread and houses sensors. This flush-mount design ensures a smooth 16mm OD (Target) profile throughout, preventing snag points during insertion and extraction.

```{python}
#| label: fig-modular-connection
#| fig-cap: "Modular flush-mount connector system showing (a) assembled view with smooth profile and (b) exploded view revealing male/female insert architecture. The 6mm (Target) central channel accommodates wiring. M12x1.75 (Manufacturer spec) threads provide robust mechanical connection."
#| fig-width: 10
#| fig-height: 9
#| code-fold: true

import sys; sys.path.insert(0, '..') if '..' not in sys.path else None
from diagrams.mechanical import create_modular_segment_connection
import matplotlib.pyplot as plt
from PIL import Image

buf = create_modular_segment_connection()
img = Image.open(buf)
plt.figure(figsize=(10, 9))
plt.imshow(img)
plt.axis('off')
plt.tight_layout()
plt.show()
```

## Thread Specifications {#sec-thread-specs}

All threaded connections use M12x1.75 ISO standard metric threads. This provides adequate strength for field assembly while remaining manufacturable via 3D printing with post-processing. The "chunky" thread profile improves printability while maintaining engagement strength.

```{python}
#| label: fig-thread-detail
#| fig-cap: "M12x1.75 thread profile detail showing (a) male thread external profile and (b) female thread cross-section. Pitch of 1.75mm (Manufacturer spec) provides good engagement with 12-15mm (Target) thread length. Male threads print at 12.2mm (Target) OD for die cutting; female threads print at 10.5mm (Target) ID for tapping."
#| fig-width: 10
#| fig-height: 5
#| code-fold: true

import sys; sys.path.insert(0, '..') if '..' not in sys.path else None
from diagrams.mechanical import create_thread_detail
import matplotlib.pyplot as plt
from PIL import Image

buf = create_thread_detail()
img = Image.open(buf)
plt.figure(figsize=(10, 5))
plt.imshow(img)
plt.axis('off')
plt.tight_layout()
plt.show()
```

| Parameter | Value |
|---|---|
| Thread Type | M12x1.75 ISO Standard |
| Pitch | 1.75 mm (Manufacturer spec) |
| Major Diameter | 12.0 mm (Manufacturer spec) |
| Engagement Length | 12-15 mm (Target) |
| Print Oversize (Male) | 12.2 mm (Target) (for Die cutting) |
| Print Undersize (Female) | 10.5 mm hole (Target) (for Tapping) |

: Thread specifications for modular connections. {#tbl-thread}

## Coil Mounting and Ferrite Cores {#sec-coil-mounting}

The MIT sensing coils are wound onto ferrite rod cores positioned along the probe body. This configuration keeps coils internal to the 16mm (Target) profile, adding only 1-2mm (Target) to the rod OD with potting. Coils are positioned orthogonally (90 degree separation) to minimize direct coupling between TX and RX elements.

```{python}
#| label: fig-coil-mounting
#| fig-cap: "Coil assembly detail showing ferrite rod core (100mm x 6mm) (Target) with copper wire windings (200-400 turns (Target) of 0.2mm (Target) enameled wire). Support brackets maintain alignment within the probe cavity. Lead wires route to the surface junction box."
#| fig-width: 10
#| fig-height: 6
#| code-fold: true

import sys; sys.path.insert(0, '..') if '..' not in sys.path else None
from diagrams.mechanical import create_coil_mounting_detail
import matplotlib.pyplot as plt
from PIL import Image

buf = create_coil_mounting_detail()
img = Image.open(buf)
plt.figure(figsize=(10, 6))
plt.imshow(img)
plt.axis('off')
plt.tight_layout()
plt.show()
```

| Parameter | Specification |
|---|---|
| Diameter | 6-8 mm (Target) |
| Length | 40-80 mm (Target) |
| Material | MnZn ferrite |
| Quantity | 1-2 per probe (TX/RX) |

: Ferrite core specifications. {#tbl-ferrite}

| Parameter | Specification |
|---|---|
| Wire Gauge | 34-38 AWG (Target) (fine wire) |
| Turns | 200-400 turns (Target) |
| Target Inductance | 1-2 mH (Target) |
| Target Q Factor | >20 (Target) |

: Coil winding specifications. {#tbl-coil-winding}

## ERT Ring Electrodes {#sec-mech-ert-rings}

Electrical Resistivity Tomography (ERT) electrodes are implemented as narrow stainless steel or copper ring bands mounted on 3D-printed insulating collars. The rings are flush-mounted to maintain the smooth probe profile. Multiple rings (typically 2-3 per probe) enable various measurement configurations.

```{python}
#| label: fig-ert-ring-detail
#| fig-cap: "ERT ring collar assembly showing stainless steel ring (316L) flush-mounted on insulating collar. Spring-loaded contact pins ensure reliable electrical connection. Ring dimensions: 5mm (Target) width x 16mm (Target) OD, approximately 50mm (Target) collar length."
#| fig-width: 10
#| fig-height: 5
#| code-fold: true

import sys; sys.path.insert(0, '..') if '..' not in sys.path else None
from diagrams.mechanical import create_ert_ring_detail
import matplotlib.pyplot as plt
from PIL import Image

buf = create_ert_ring_detail()
img = Image.open(buf)
plt.figure(figsize=(10, 5))
plt.imshow(img)
plt.axis('off')
plt.tight_layout()
plt.show()
```

| Parameter | Value |
|---|---|
| Ring Material | Stainless steel (316L) or copper |
| Ring Width | 3-5 mm (Target) (narrow bands) |
| Ring Thickness | 0.5-1 mm (Target) |
| Diameter | Match rod OD (16 mm) (Target) |
| Quantity | 2-3 rings per probe (Target) |
| Minimum Spacing | 0.3 m (Target) between rings |

: ERT ring electrode specifications. {#tbl-ert-ring}

| Position | Distance from Tip |
|---|---|
| Ring A (Upper) | 0.5 m (Target) |
| Ring B (Mid) | 1.5 m (Target) |
| Ring C (Deep) | 2.5-3.0 m (Target) (optional) |

: Standard ERT ring mounting positions. {#tbl-ert-positions}

## Junction Box Design {#sec-junction-box}

The surface junction box serves as the termination point for all probe wiring. It contains no active electronics - only passive connections via a terminal block. This keeps the probe lightweight and simple while enabling field serviceability. All "smart" electronics reside in the central hub at the surface.

```{python}
#| label: fig-junction-box
#| fig-cap: "Junction box design showing (a) external view with cable gland and weatherproof body, and (b) internal cutaway revealing terminal block for MIT coil and ERT electrode connections. M12x1.75 internal thread mates with probe rod."
#| fig-width: 10
#| fig-height: 5
#| code-fold: true

import sys; sys.path.insert(0, '..') if '..' not in sys.path else None
from diagrams.mechanical import create_junction_box_diagram
import matplotlib.pyplot as plt
from PIL import Image

buf = create_junction_box_diagram()
img = Image.open(buf)
plt.figure(figsize=(10, 5))
plt.imshow(img)
plt.axis('off')
plt.tight_layout()
plt.show()
```

| Dimension | Value |
|---|---|
| Diameter | 25 mm (Target) |
| Height | 35 mm (Target) |
| Thread | Internal M12x1.75 (bottom) |
| Material | PETG or ABS (weatherproof) |
| Features | Terminal block mount, cable gland |

: Surface junction box specifications. {#tbl-junction-box}

## Probe Cross-Section Detail {#sec-probe-cross-section}

The complete probe assembly integrates all components into a unified 16mm OD (Target) profile. The cross-section reveals the internal arrangement of coils, ERT rings, threaded joints, and wiring passages. This dense packing enables full sensing capability while minimizing ground disturbance.

```{python}
#| label: fig-probe-cross-section-mech
#| fig-cap: "Detailed probe cross-section showing complete internal architecture. From bottom: tapered tip, ERT ring positions, RX coil with ferrite core, M12 threaded joints, TX coil assembly, and junction box connection. Standard 50cm (Target) segment shown."
#| fig-width: 6
#| fig-height: 10
#| code-fold: true

import sys; sys.path.insert(0, '..') if '..' not in sys.path else None
from diagrams.mechanical import create_probe_cross_section
import matplotlib.pyplot as plt
from PIL import Image

buf = create_probe_cross_section()
img = Image.open(buf)
plt.figure(figsize=(6, 10))
plt.imshow(img)
plt.axis('off')
plt.tight_layout()
plt.show()
```

## Manufacturing Procedures {#sec-manufacturing}

## 3D Printing Guide {#sec-3d-printing}

All plastic components are designed for FDM 3D printing with specific settings optimized for thread quality and structural integrity. PETG or ASA material is required for impact resistance and UV stability. Critical: threads require post-processing with tap and die tools.

```{python}
#| label: fig-tool-requirements
#| fig-cap: "Tool requirements for probe assembly including thread cutting tools (M12x1.75 tap and die), assembly supplies (epoxy, heat shrink), and finishing tools. 3D printer settings shown for Bambu Lab / FDM machines."
#| fig-width: 10
#| fig-height: 6
#| code-fold: true

import sys; sys.path.insert(0, '..') if '..' not in sys.path else None
from diagrams.mechanical import create_tool_requirements_diagram
import matplotlib.pyplot as plt
from PIL import Image

buf = create_tool_requirements_diagram()
img = Image.open(buf)
plt.figure(figsize=(10, 6))
plt.imshow(img)
plt.axis('off')
plt.tight_layout()
plt.show()
```

| Setting | Value | Notes |
|---|---|---|
| Material | PETG or ASA | Required for impact/UV |
| Layer Height | 0.12mm (Target) | Critical for threads |
| Infill | 100% (Solid) (Target) | Critical for strength |
| Walls | 6 Loops (Target) | Solid threaded regions |
| Supports | DISABLED | Use built-in scaffolding |
| Speed | 50mm/s (Target) outer wall | Quality over speed |

: Recommended 3D printer settings for probe components. {#tbl-print-settings}

## Thread Post-Processing {#sec-thread-postprocessing}

::: {.callout-note}
## Thread Cutting Procedure

- Male threads: Print at 12.2mm OD (Target), cut with M12x1.75 Die
- Female threads: Print at 10.5mm hole (Target), cut with M12x1.75 Tap
- Always use cutting oil to reduce friction
- Cut slowly, back out frequently to clear chips
- Test fit before epoxy assembly
:::

## Insertion Methods {#sec-mech-insertion-methods}

Four primary insertion methods accommodate different soil conditions. Method selection depends on soil type, target depth, and available equipment. The pilot rod method requires complete removal of metal before measurements.

```{python}
#| label: fig-insertion-methods
#| fig-cap: "Probe insertion methods: (a) Hand auger for most soils using 10-20mm (Target) auger; (b) Pilot rod for compact soils - must remove metal before survey; (c) Direct push in sandy soils only; (d) Water-jet method for excellent sand penetration with minimal disturbance."
#| fig-width: 10
#| fig-height: 8
#| code-fold: true

import sys; sys.path.insert(0, '..') if '..' not in sys.path else None
from diagrams.mechanical import create_insertion_methods_diagram
import matplotlib.pyplot as plt
from PIL import Image

buf = create_insertion_methods_diagram()
img = Image.open(buf)
plt.figure(figsize=(10, 8))
plt.imshow(img)
plt.axis('off')
plt.tight_layout()
plt.show()
```

## Assembly Sequence {#sec-assembly-sequence}

Probe assembly follows a bottom-to-top sequence with all components screwing together via M12 threads. The modular design enables field assembly and allows replacement of individual segments without rebuilding the entire probe.

```{python}
#| label: fig-assembly-sequence
#| fig-cap: "Assembly sequence from bottom to top: (1) Probe tip pointing down, (2) Bottom rod segment with RX coil, (3) First ERT ring at 0.5m (Target), (4) Coupler joint, (5) Top rod segment with TX coil, (6) Additional ERT rings, (7) Junction box at surface level."
#| fig-width: 7
#| fig-height: 10
#| code-fold: true

import sys; sys.path.insert(0, '..') if '..' not in sys.path else None
from diagrams.mechanical import create_assembly_sequence_diagram
import matplotlib.pyplot as plt
from PIL import Image

buf = create_assembly_sequence_diagram()
img = Image.open(buf)
plt.figure(figsize=(7, 10))
plt.imshow(img)
plt.axis('off')
plt.tight_layout()
plt.show()
```

## Advantages of Micro-Probe Design {#sec-mech-advantages}

```{python}
#| label: fig-advantages
#| fig-cap: "Summary of micro-probe design advantages including 10x (Modeled) less disturbance, modular field-serviceable construction, passive probes with no downhole electronics, and 70% (Modeled) cost reduction compared to traditional designs."
#| fig-width: 10
#| fig-height: 7
#| code-fold: true

import sys; sys.path.insert(0, '..') if '..' not in sys.path else None
from diagrams.mechanical import create_advantages_diagram
import matplotlib.pyplot as plt
from PIL import Image

buf = create_advantages_diagram()
img = Image.open(buf)
plt.figure(figsize=(10, 7))
plt.imshow(img)
plt.axis('off')
plt.tight_layout()
plt.show()
```

Key advantages of the micro-probe design include:

- **Strength:** 16mm OD (Target) allows for robust M12 threads
- **Modularity:** Sensor spacing determined by rod segment length
- **Manufacturability:** Sensors built into printed parts, not glued onto rod
- **Smooth Profile:** Flush connections prevent snagging during insertion/extraction
- **Field Serviceable:** Replace individual segments without rebuilding entire probe
- **Simpler Assembly:** No electronics in probe
- **Lighter Weight:** ~50-100 g per meter (Modeled) (vs 200-250 g)
- **Easier Insertion:** Smaller diameter, less force needed
- **Lower Cost:** ~$40-60 per probe (Target) (vs $130-180)
- **Better Reliability:** Passive probes more robust
- **Minimal Intrusion:** ~10x (Modeled) less disturbance than 25mm design

## Rapid Prototyping Guide {#sec-rapid-prototyping}

This section provides a streamlined workflow for building a **Minimum Viable Prototype (MVP)** to validate the probe design quickly. The goal is to achieve first functional data within 1-2 days, enabling rapid iteration if design changes are needed.

### Prototyping Philosophy {#sec-proto-philosophy}

The prototyping approach follows a "fail-fast" methodology:

- **Prioritize speed to first data** over production quality
- **Use relaxed tolerances** (+/-20% (Target) vs +/-10% (Target)) for initial validation
- **Accept reversible assembly** (dry-fit, no epoxy) for iteration
- **Focus on core physics validation** before manufacturing refinement

::: {.callout-tip}
## MVP Success Criteria (Relaxed for Prototyping)

| Parameter | Production Spec | Prototype Target |
|---|---|---|
| Inductance | 1.5 mH +/-10% (Target) | 1.5 mH +/-20% (Target) |
| Q Factor @ 10kHz | >=30 (Target) | >=15 (Target) |
| Metal detection | Calibrated | Visible response |
| Thread quality | Production | Functional fit |

If these relaxed criteria are met, proceed to production-quality builds.
:::

### Prototyping Workflow {#sec-proto-workflow}

The MVP build process consists of four main phases that can be completed in approximately 10-12 hours of active work over 2 days.

```{python}
#| label: fig-proto-workflow
#| fig-cap: "Rapid prototyping workflow showing the four-phase MVP build process. Each phase produces a concrete deliverable that feeds the next phase. Total active time is approximately 10 hours, with the print phase typically run overnight."
#| fig-width: 10
#| fig-height: 7
#| code-fold: true

import sys; sys.path.insert(0, '..') if '..' not in sys.path else None
from diagrams.mechanical import create_prototyping_workflow
import matplotlib.pyplot as plt
from PIL import Image

buf = create_prototyping_workflow()
img = Image.open(buf)
plt.figure(figsize=(10, 7))
plt.imshow(img)
plt.axis('off')
plt.tight_layout()
plt.show()
```

### Minimum Parts List {#sec-proto-parts}

For the MVP, only three 3D printed parts are required:

| Part | STL File | Purpose |
|---|---|---|
| Sensor body | `sensor_body_single_test.stl` | Houses coil |
| Male rod cap | `male_rod_cap_threads_test.stl` | Connects to rod |
| Probe tip | From `probe_tip_4x.stl` | Bottom terminator |

: Minimum 3D printed parts for MVP prototype. {#tbl-proto-parts}

Additional materials needed:

| Component | Specification | Notes |
|---|---|---|
| Fiberglass tube | 16mm OD (Target) x 300mm (Target) | Single segment |
| Ferrite rod | 8mm dia. (Target) x 100mm (Target), NiZn | Core material |
| Magnet wire | 34 AWG (Target), 15m (Target) | For 300 turns |
| Test leads | Alligator clips | Bench testing |

: Additional materials for MVP prototype. {#tbl-proto-materials}

### Coil Winding for Prototyping {#sec-proto-coil}

The coil is the most critical component. Follow this simplified winding procedure optimized for first-time success.

```{python}
#| label: fig-coil-winding-steps
#| fig-cap: "Step-by-step coil winding visual guide. The process takes 45-90 minutes (Target) depending on experience. Key success factors: consistent tension, close-wound turns, and measurement before securing."
#| fig-width: 10
#| fig-height: 4
#| code-fold: true

import sys; sys.path.insert(0, '..') if '..' not in sys.path else None
from diagrams.mechanical import create_coil_winding_steps
import matplotlib.pyplot as plt
from PIL import Image

buf = create_coil_winding_steps()
img = Image.open(buf)
plt.figure(figsize=(10, 4))
plt.imshow(img)
plt.axis('off')
plt.tight_layout()
plt.show()
```

**Coil Winding Checklist:**

1. [ ] Clean ferrite rod with IPA
2. [ ] Mark 50mm (Target) winding zone at center
3. [ ] Leave 150mm (Target) wire tail, secure with tape
4. [ ] Wind 300 turns (Target), single layer, close-wound
5. [ ] Maintain consistent light tension (~50g (Target))
6. [ ] **Measure inductance before securing** (target: 1.2-1.8 mH (Target))
7. [ ] Apply thin CA glue or nail polish to fix
8. [ ] Strip and tin wire ends (5mm (Target))

::: {.callout-warning}
## Critical: Measure Before Securing

Always verify inductance *before* applying fixative. If inductance is outside 1.2-1.8 mH (Target), adjust turns (+/-20-30 turns) and re-measure. Once glue is applied, changes are difficult.
:::

### Quick Functional Test Setup {#sec-proto-test-setup}

The functional test validates that the coil responds to conductive targets. This is a qualitative "go/no-go" test before proceeding to full calibration.

```{python}
#| label: fig-quick-test-setup
#| fig-cap: "Bench test setup for functional validation. A function generator drives the coil at 10 kHz (Target) through a 100 ohm (Target) current-limiting resistor. The oscilloscope monitors the coil voltage. When a metal target approaches, the amplitude and/or phase should change visibly."
#| fig-width: 10
#| fig-height: 5
#| code-fold: true

import sys; sys.path.insert(0, '..') if '..' not in sys.path else None
from diagrams.mechanical import create_quick_test_setup
import matplotlib.pyplot as plt
from PIL import Image

buf = create_quick_test_setup()
img = Image.open(buf)
plt.figure(figsize=(10, 5))
plt.imshow(img)
plt.axis('off')
plt.tight_layout()
plt.show()
```

**Test Procedure:**

1. Connect function generator to coil through 100 ohm (Target) series resistor
2. Set generator to 10 kHz (Target) sine wave, 2V peak-to-peak (Target)
3. Connect oscilloscope across the coil
4. Record baseline amplitude (no target present)
5. Slowly approach metal target (bolt, aluminum can) on non-metallic stick
6. Watch for amplitude or phase change on oscilloscope
7. Note distance at which change becomes visible

**Pass Criteria:**

- Stable baseline signal
- Visible change when metal target within 10cm (Target)
- Response repeatable across 3 trials

### Prototype Test Decision Tree {#sec-proto-decision}

After completing the functional test, use this decision tree to determine next steps.

```{python}
#| label: fig-proto-decision
#| fig-cap: "Decision tree for prototype test results. Each test checkpoint has a clear pass/fail criterion with corresponding remediation action. All three tests must pass to proceed to Phase 2 (add ERT, multi-segment assembly)."
#| fig-width: 10
#| fig-height: 6
#| code-fold: true

import sys; sys.path.insert(0, '..') if '..' not in sys.path else None
from diagrams.mechanical import create_prototype_decision_tree
import matplotlib.pyplot as plt
from PIL import Image

buf = create_prototype_decision_tree()
img = Image.open(buf)
plt.figure(figsize=(10, 6))
plt.imshow(img)
plt.axis('off')
plt.tight_layout()
plt.show()
```

| Test | Pass Criteria | If Fail |
|---|---|---|
| Coil L, Q | L = 1.2-1.8 mH (Target), Q >= 15 (Target) | Re-wind coil, check core |
| Thread fit | Parts screw together | Reprint with blanks + tap/die |
| Metal detect | Visible response | Debug test setup, check drive |

: Prototype test pass/fail criteria and remediation actions. {#tbl-proto-tests}

### Troubleshooting Common Issues {#sec-proto-troubleshooting}

::: {.callout-note}
## No Signal on Oscilloscope

1. Check function generator output (probe directly)
2. Verify coil continuity with multimeter
3. Check all cable connections
4. Try higher drive voltage (up to 5V p-p)
:::

::: {.callout-note}
## No Response to Metal Target

1. Try larger target (bigger = stronger signal)
2. Try closer distance (<5cm (Target))
3. Try different frequencies (2, 5, 20, 50 kHz (Target))
4. Verify coil current is flowing (series resistor voltage)
5. Check for shorted turns (Q factor very low)
:::

::: {.callout-note}
## Threads Won't Fit

1. Chase with M12x1.75 tap (female) or die (male)
2. Light sanding on male thread OD
3. Check for debris or print defects
4. If cracking: reprint using blanks + tap/die approach
:::

### Next Steps After MVP Success {#sec-proto-next}

Once the MVP prototype passes all tests, proceed through these phases:

| Phase | Goal | Key Tasks |
|---|---|---|
| **Phase 2** | Add ERT | Install electrode ring, test isolation |
| **Phase 3** | Multi-segment | Build 2-segment probe, test connection |
| **Phase 4** | Production wiring | Phoenix connectors, cable harness |
| **Phase 5** | Field test | Waterproof, deploy in soil |

: Prototype development phases after MVP validation. {#tbl-proto-phases}

## References {#sec-mech-references}

1. HIRT Development Team (2026). HIRT Whitepaper: Hybrid Impedance-Resistivity Tomography System. Section 7: Assembly and Wiring.
2. HIRT Development Team (2026). HIRT Whitepaper: Hybrid Impedance-Resistivity Tomography System. Section 6: Electronics and Circuits.
3. ISO 261:1998. ISO general purpose metric screw threads - General plan.
4. ASTM D2584. Standard Test Method for Ignition Loss of Cured Reinforced Resins (Fiberglass specifications).
