chadlindell/terrascry/geosim/godot/assets/textures/grass/grass_blade.png

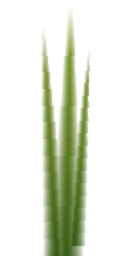
geosim/godot/assets/textures/grass/grass_blade.png
