chadlindell/terrascry/hirt/docs/_freeze/build-guide/assembly/figure-html/fig-connector-pinout-output-1.png

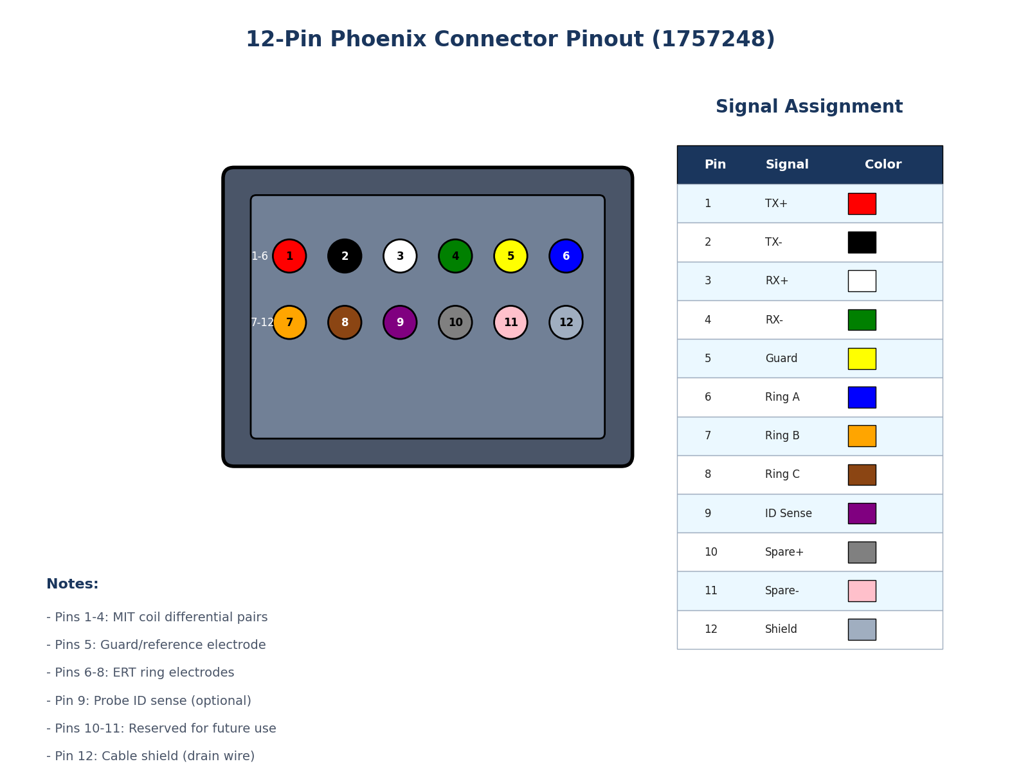
hirt/docs/_freeze/build-guide/assembly/figure-html/fig-connector-pinout-output-1.png
