chadlindell/terrascry/hirt/docs/_freeze/build-guide/assembly/figure-html/fig-zone-architecture-output-1.png

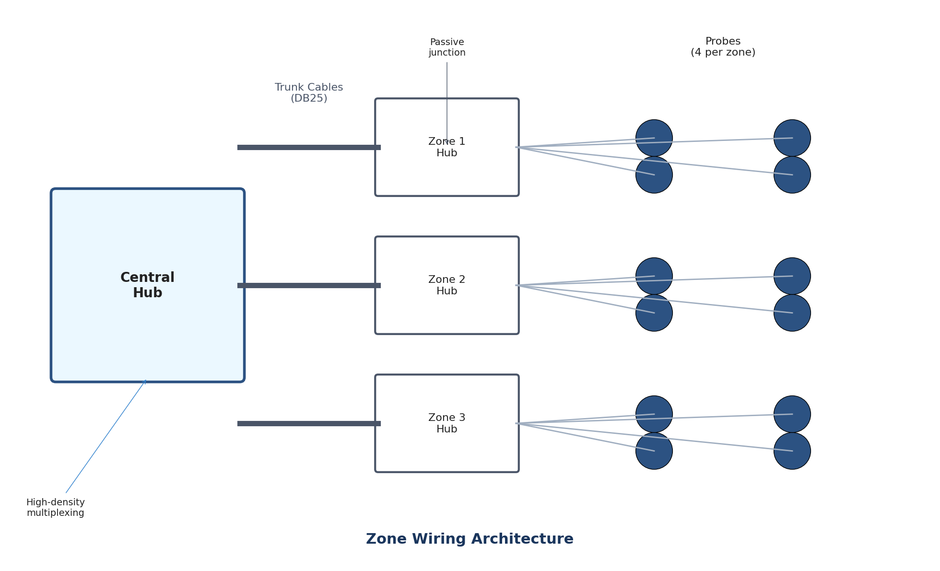
hirt/docs/_freeze/build-guide/assembly/figure-html/fig-zone-architecture-output-1.png
