chadlindell/terrascry/hirt/docs/_freeze/build-guide/electronics/figure-html/fig-adc-interface-output-1.png

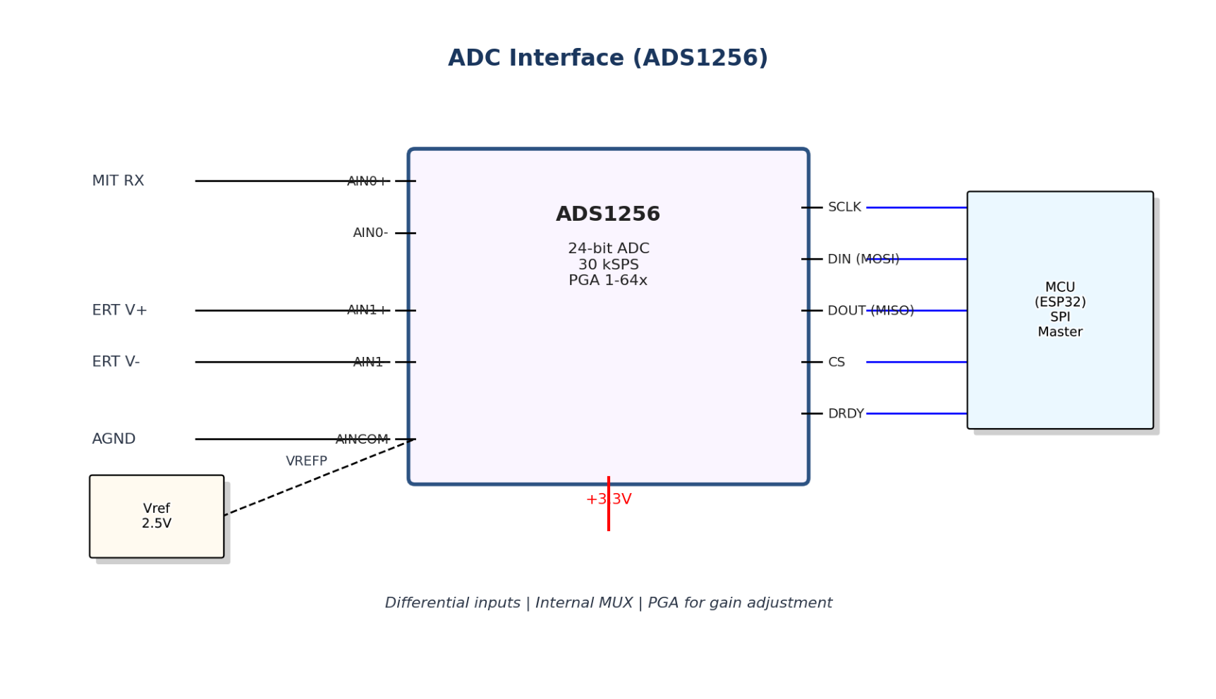
hirt/docs/_freeze/build-guide/electronics/figure-html/fig-adc-interface-output-1.png
