chadlindell/terrascry/hirt/docs/_freeze/build-guide/electronics/figure-html/fig-ert-current-source-output-1.png

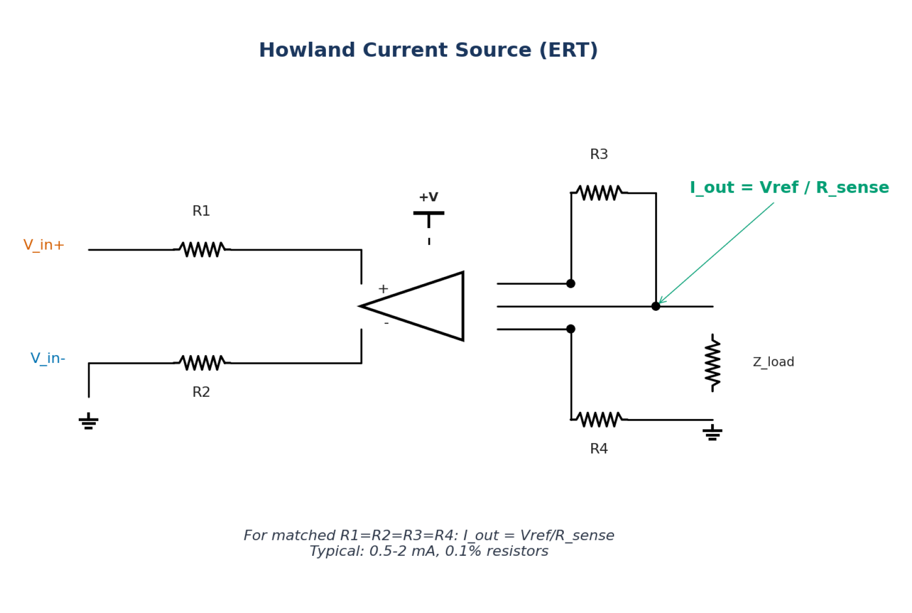
hirt/docs/_freeze/build-guide/electronics/figure-html/fig-ert-current-source-output-1.png
