chadlindell/terrascry/hirt/docs/_freeze/build-guide/electronics/figure-html/fig-ground-loop-output-1.png

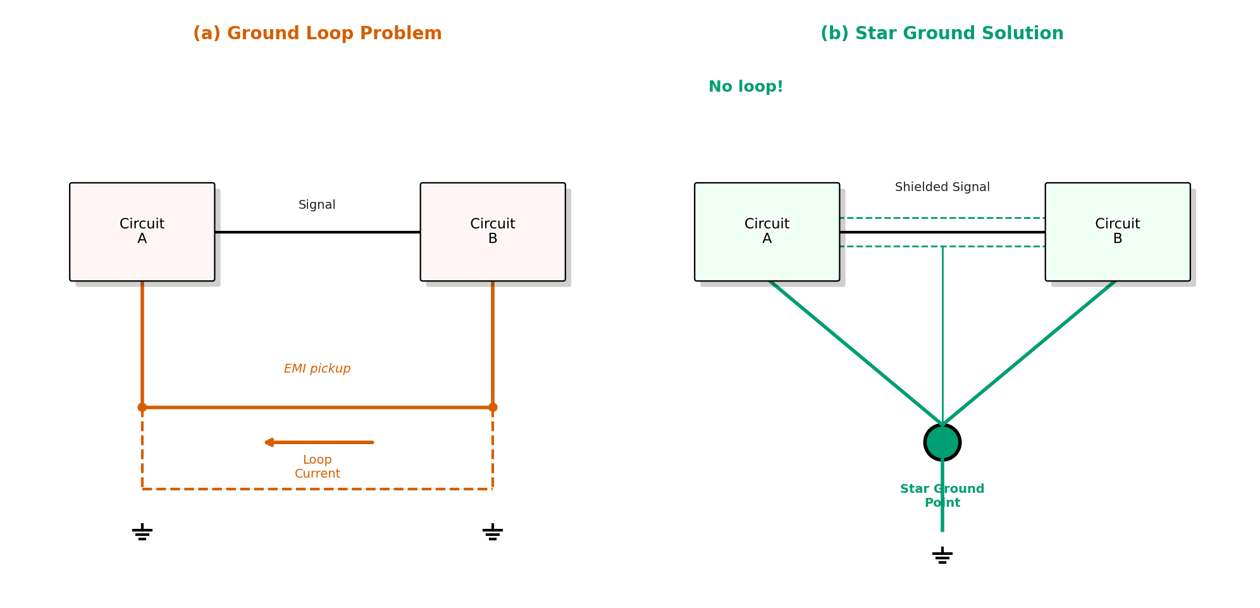
hirt/docs/_freeze/build-guide/electronics/figure-html/fig-ground-loop-output-1.png
