chadlindell/terrascry/hirt/docs/_freeze/build-guide/electronics/figure-html/fig-lockin-detection-output-1.png

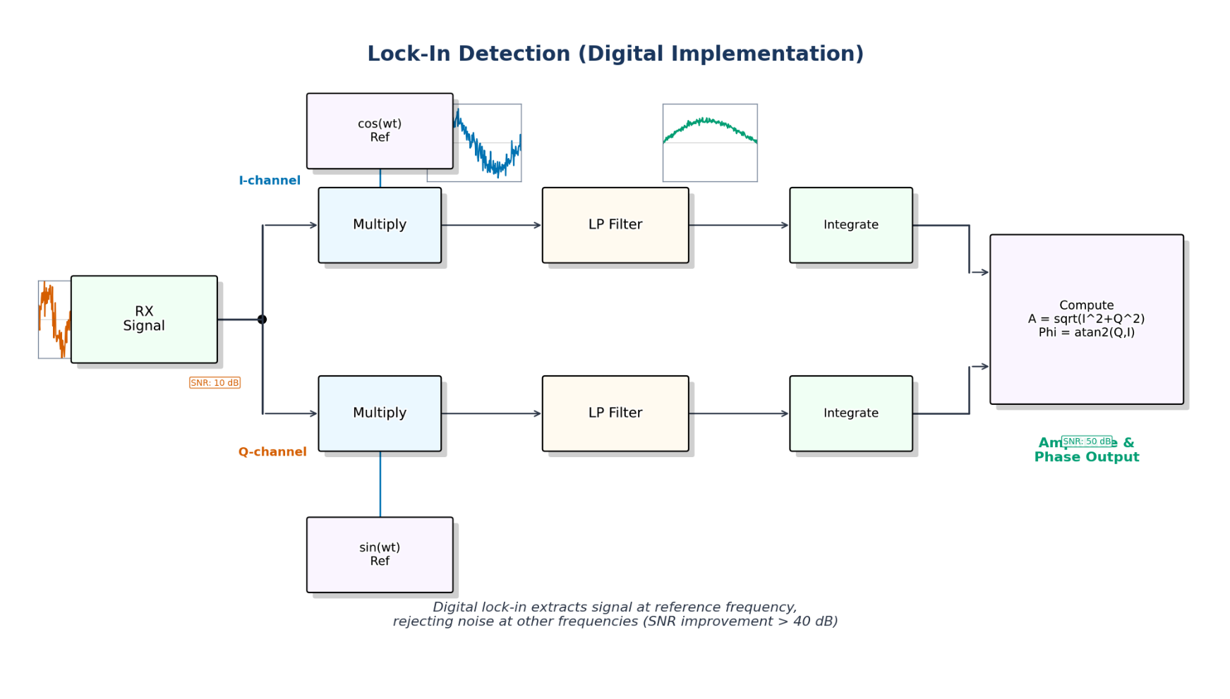
hirt/docs/_freeze/build-guide/electronics/figure-html/fig-lockin-detection-output-1.png
