chadlindell/terrascry/hirt/docs/_freeze/build-guide/electronics/figure-html/fig-mit-rx-chain-output-1.png

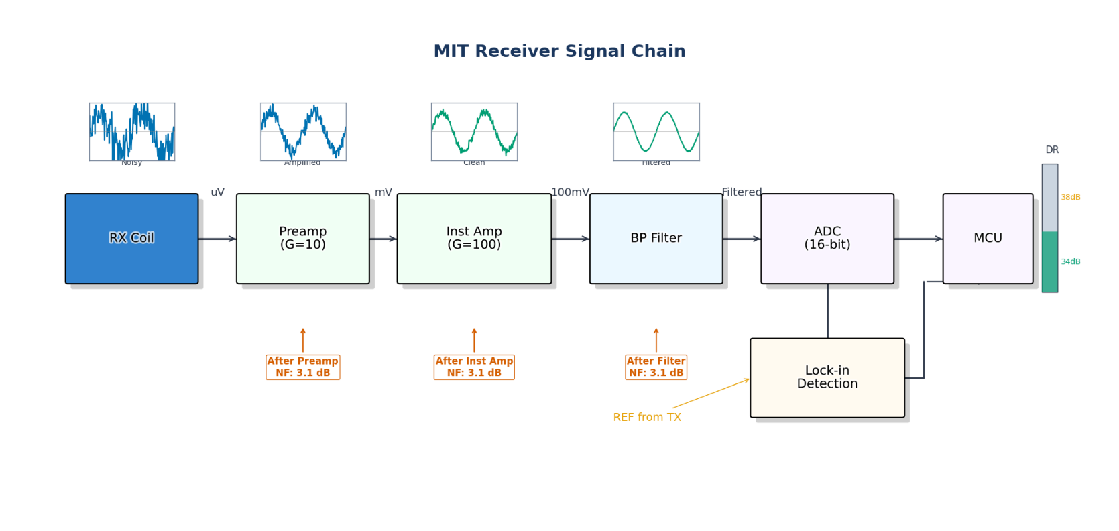
hirt/docs/_freeze/build-guide/electronics/figure-html/fig-mit-rx-chain-output-1.png
