chadlindell/terrascry/hirt/docs/_freeze/build-guide/electronics/figure-html/fig-mit-tx-chain-output-1.png

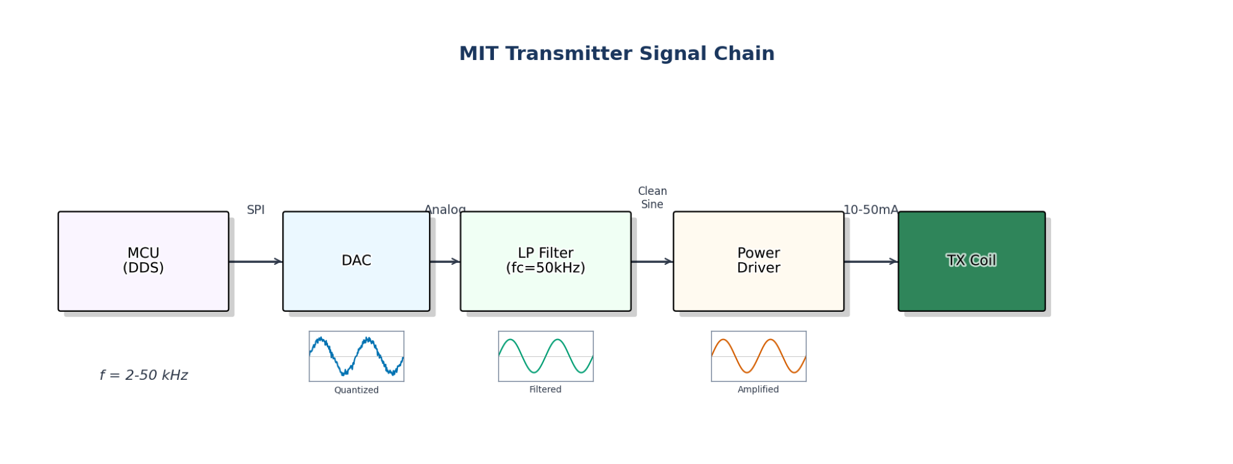
hirt/docs/_freeze/build-guide/electronics/figure-html/fig-mit-tx-chain-output-1.png
