chadlindell/terrascry/hirt/docs/_freeze/build-guide/electronics/figure-html/fig-signal-level-output-1.png

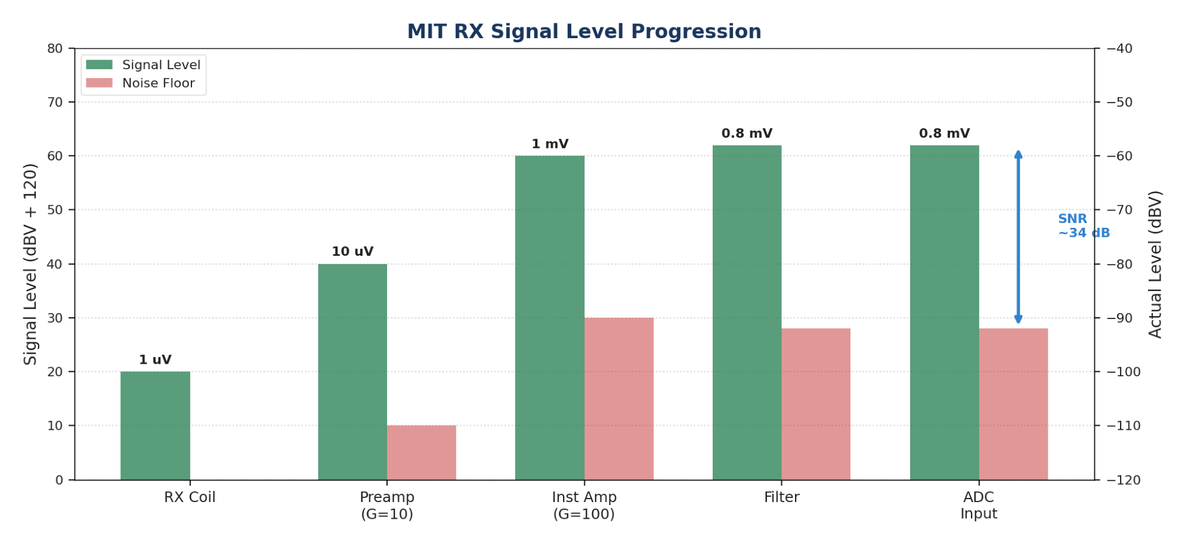
hirt/docs/_freeze/build-guide/electronics/figure-html/fig-signal-level-output-1.png
