chadlindell/terrascry/hirt/docs/_freeze/build-guide/electronics/figure-html/fig-system-block-elec-output-1.png

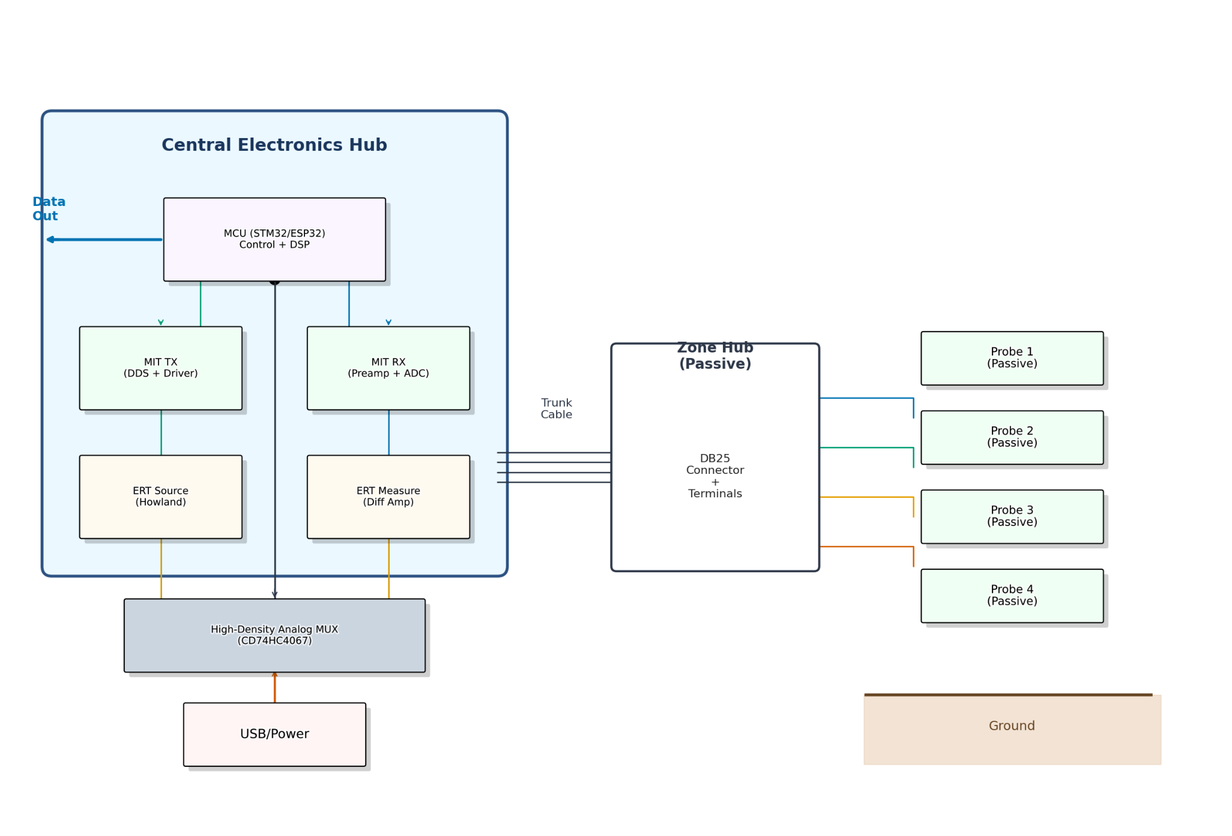
hirt/docs/_freeze/build-guide/electronics/figure-html/fig-system-block-elec-output-1.png
