chadlindell/terrascry/hirt/docs/_freeze/build-guide/mechanical/figure-html/fig-advantages-output-1.png

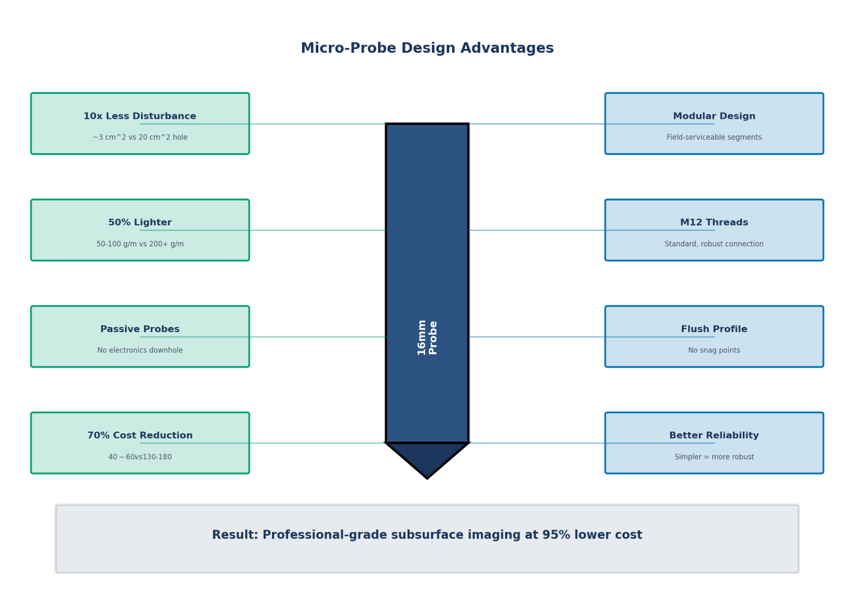
hirt/docs/_freeze/build-guide/mechanical/figure-html/fig-advantages-output-1.png
