chadlindell/terrascry/hirt/docs/_freeze/build-guide/mechanical/figure-html/fig-disturbance-comparison-output-1.png

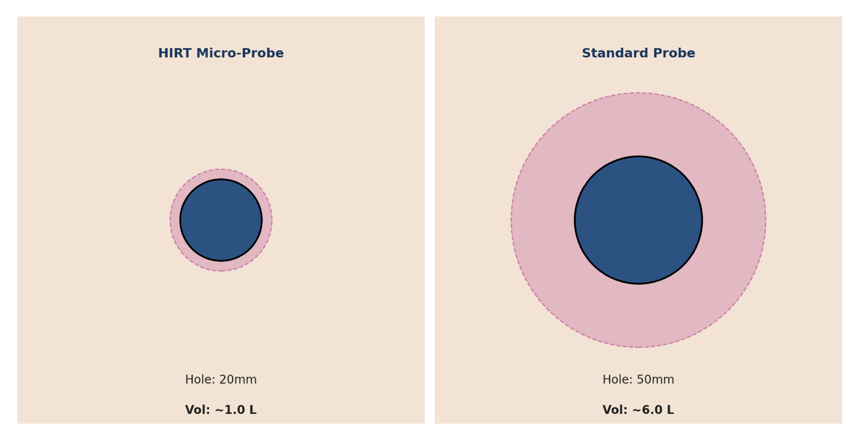
hirt/docs/_freeze/build-guide/mechanical/figure-html/fig-disturbance-comparison-output-1.png
