chadlindell/terrascry/hirt/docs/_freeze/build-guide/mechanical/figure-html/fig-insertion-methods-output-1.png

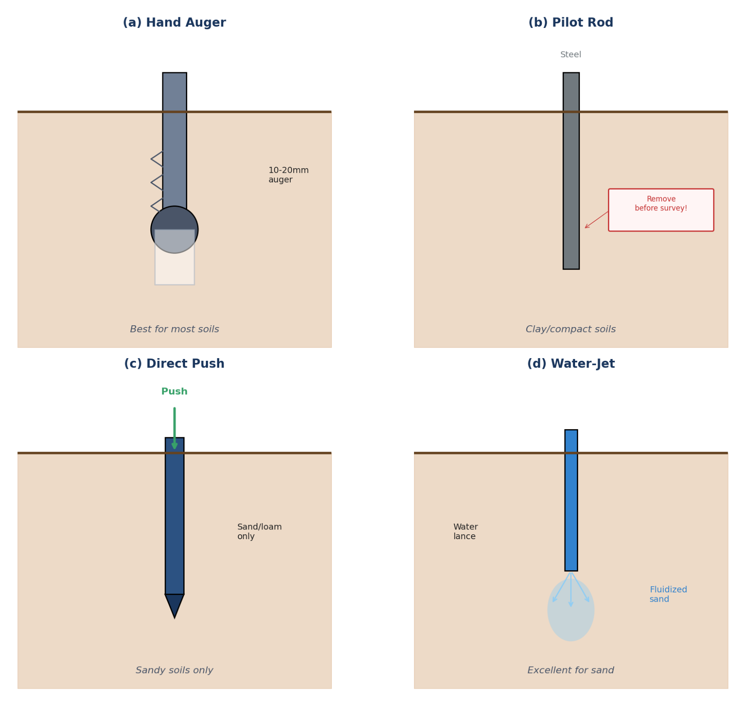
hirt/docs/_freeze/build-guide/mechanical/figure-html/fig-insertion-methods-output-1.png
