chadlindell/terrascry/hirt/docs/_freeze/build-guide/mechanical/figure-html/fig-junction-box-output-1.png

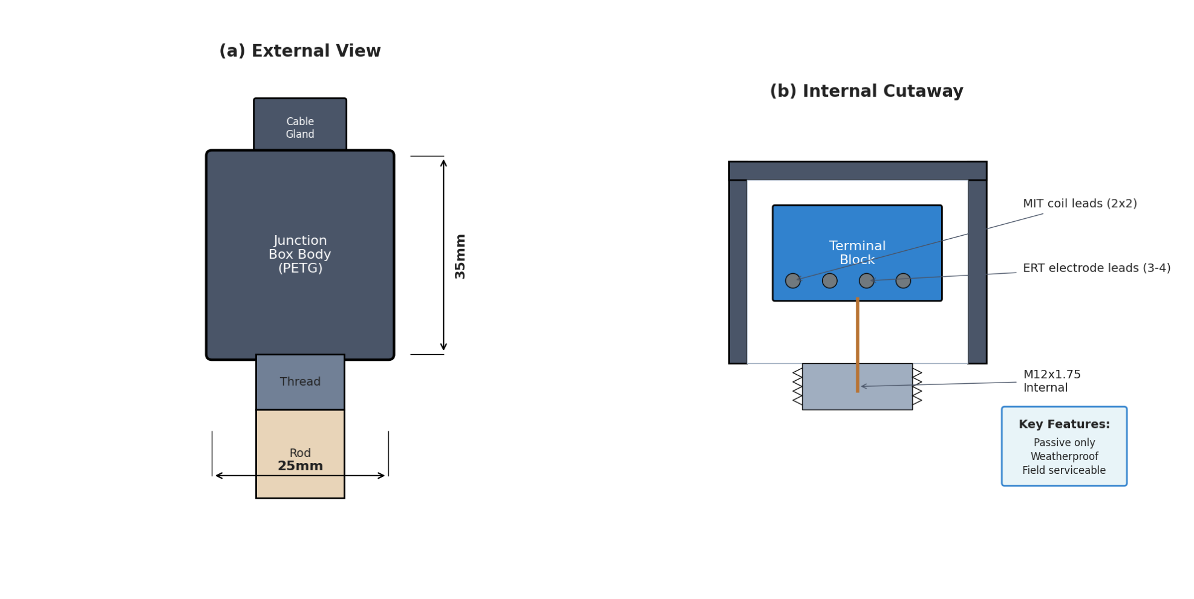
hirt/docs/_freeze/build-guide/mechanical/figure-html/fig-junction-box-output-1.png
