chadlindell/terrascry/hirt/docs/_freeze/build-guide/mechanical/figure-html/fig-modular-connection-output-1.png

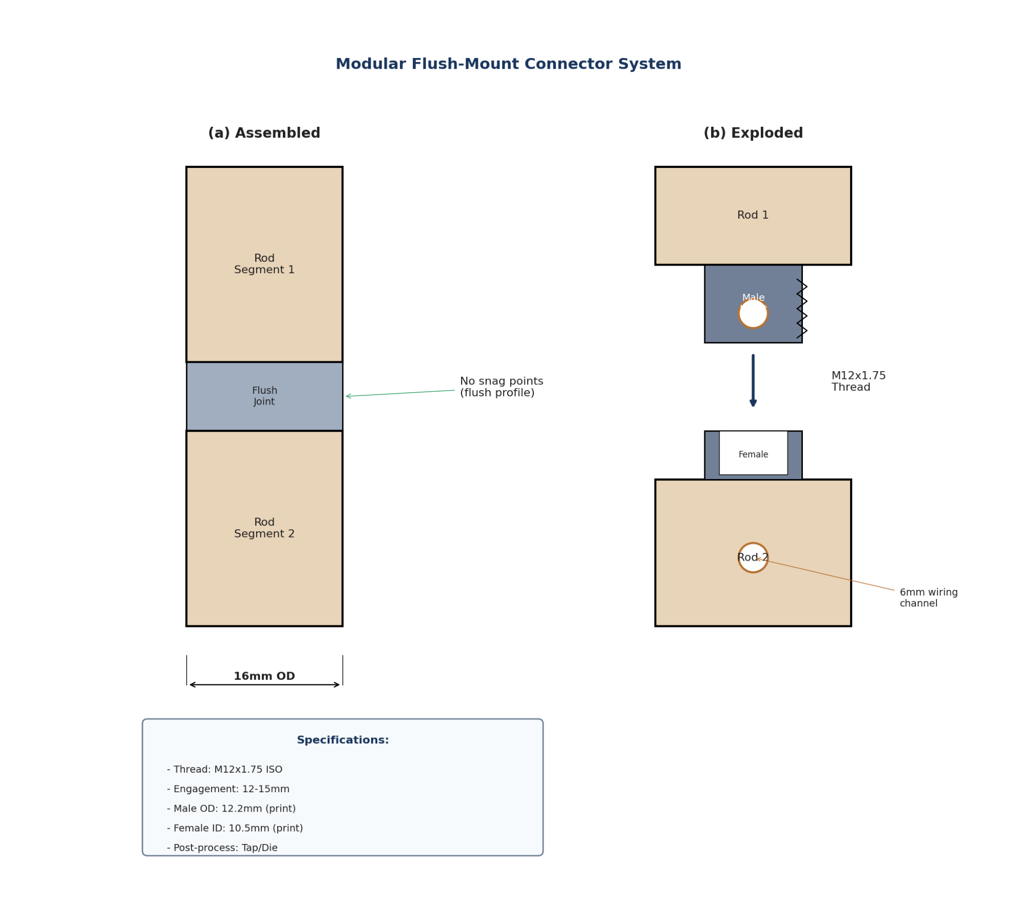
hirt/docs/_freeze/build-guide/mechanical/figure-html/fig-modular-connection-output-1.png
