chadlindell/terrascry/hirt/docs/_freeze/build-guide/mechanical/figure-html/fig-probe-cross-section-mech-output-1.png

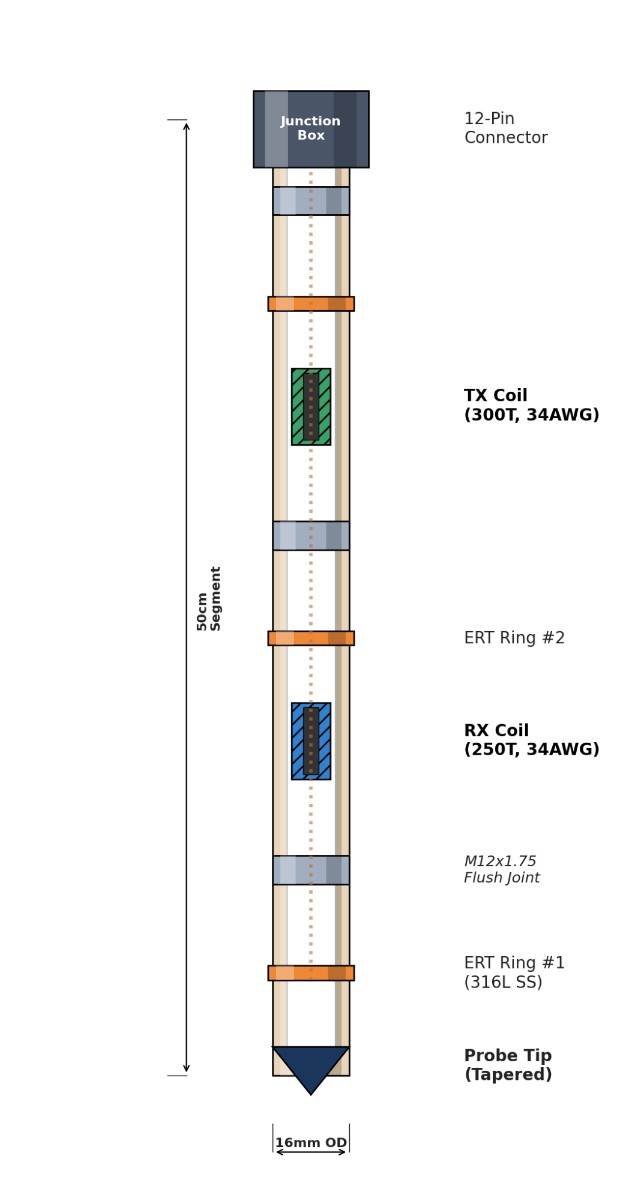
hirt/docs/_freeze/build-guide/mechanical/figure-html/fig-probe-cross-section-mech-output-1.png
