chadlindell/terrascry/hirt/docs/_freeze/developer/roadmap/figure-html/fig-development-roadmap-output-1.png

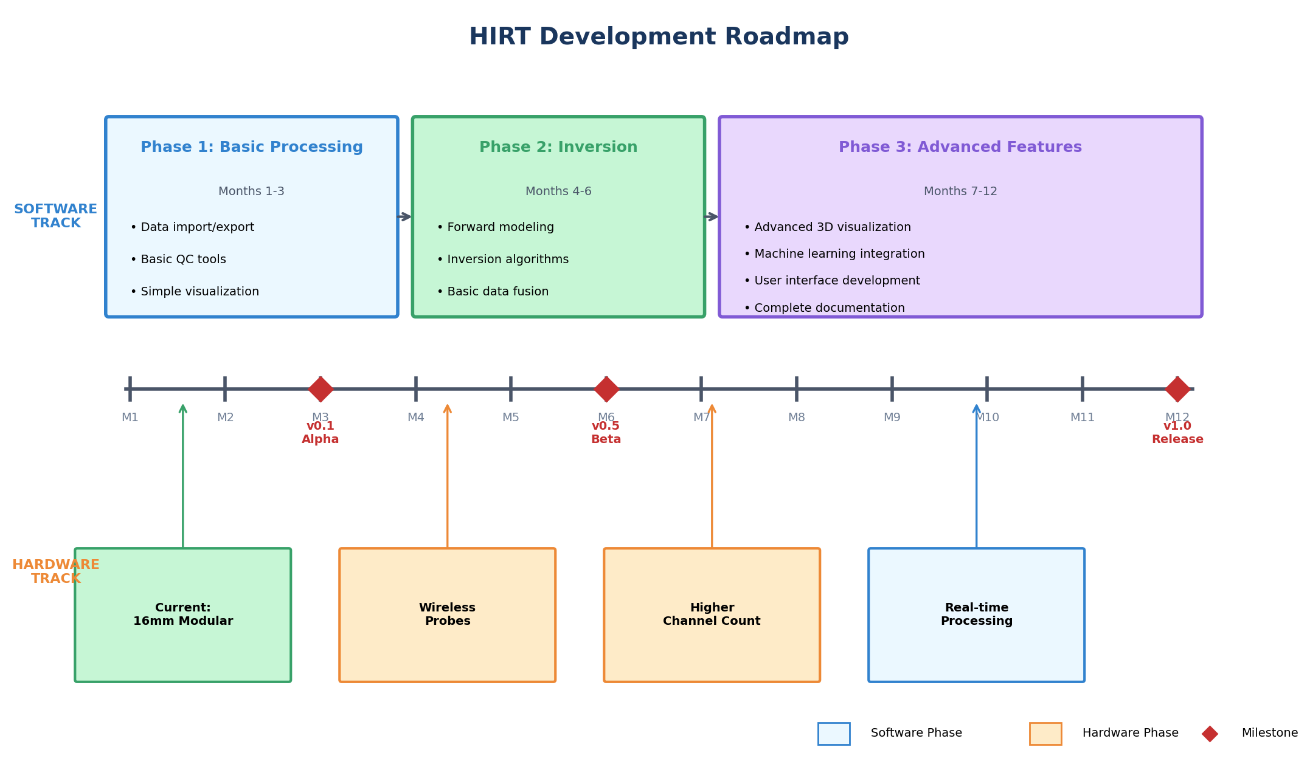
hirt/docs/_freeze/developer/roadmap/figure-html/fig-development-roadmap-output-1.png
