chadlindell/terrascry/hirt/docs/_freeze/developer/roadmap/figure-html/fig-feature-priority-output-1.png

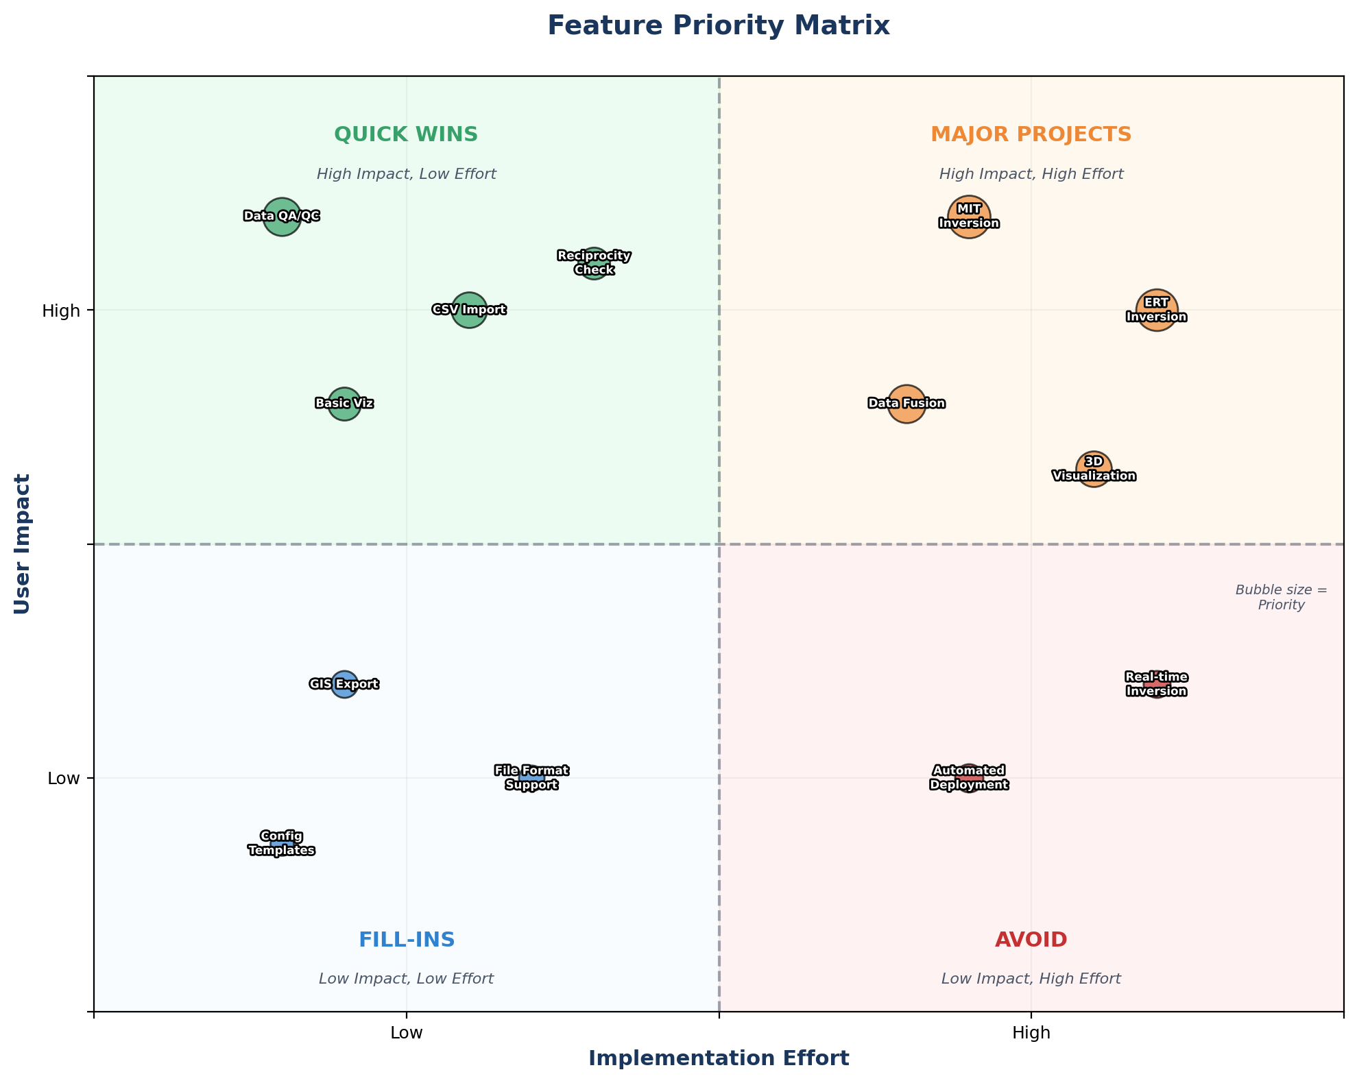
hirt/docs/_freeze/developer/roadmap/figure-html/fig-feature-priority-output-1.png
