chadlindell/terrascry/hirt/docs/_freeze/getting-started/overview/figure-html/fig-capabilities-output-1.png

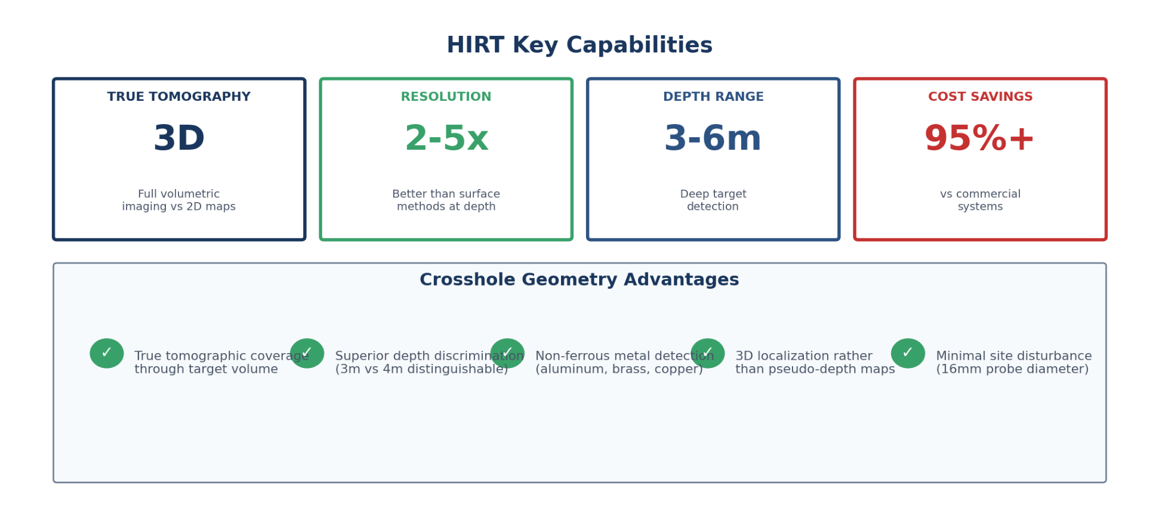
hirt/docs/_freeze/getting-started/overview/figure-html/fig-capabilities-output-1.png
