chadlindell/terrascry/hirt/docs/_freeze/getting-started/overview/figure-html/fig-system-overview-output-1.png

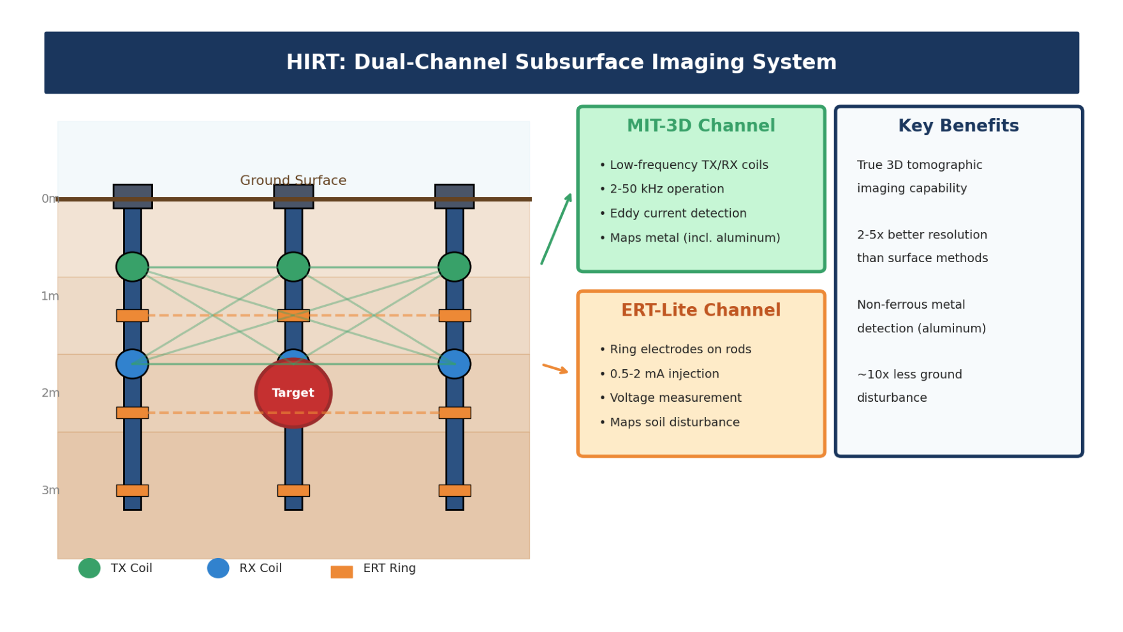
hirt/docs/_freeze/getting-started/overview/figure-html/fig-system-overview-output-1.png
