chadlindell/terrascry/hirt/docs/_freeze/theory/architecture/figure-html/fig-array-configs-output-1.png

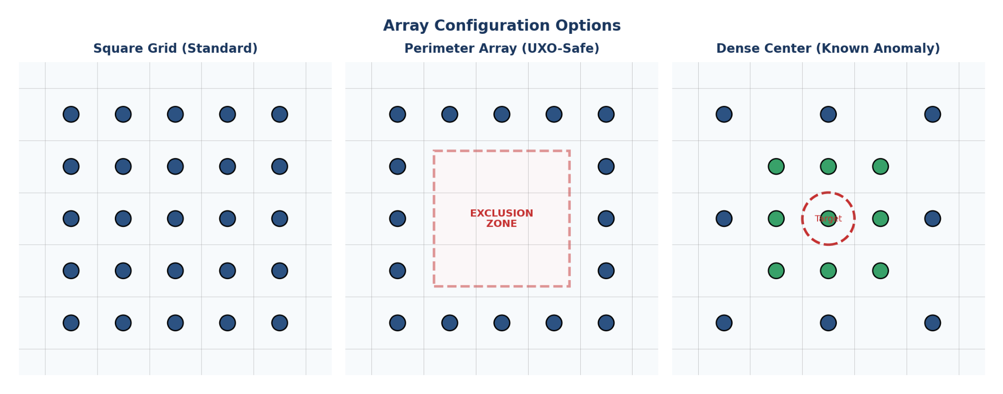
hirt/docs/_freeze/theory/architecture/figure-html/fig-array-configs-output-1.png
