chadlindell/terrascry/hirt/docs/_freeze/theory/architecture/figure-html/fig-ert-signal-flow-output-1.png

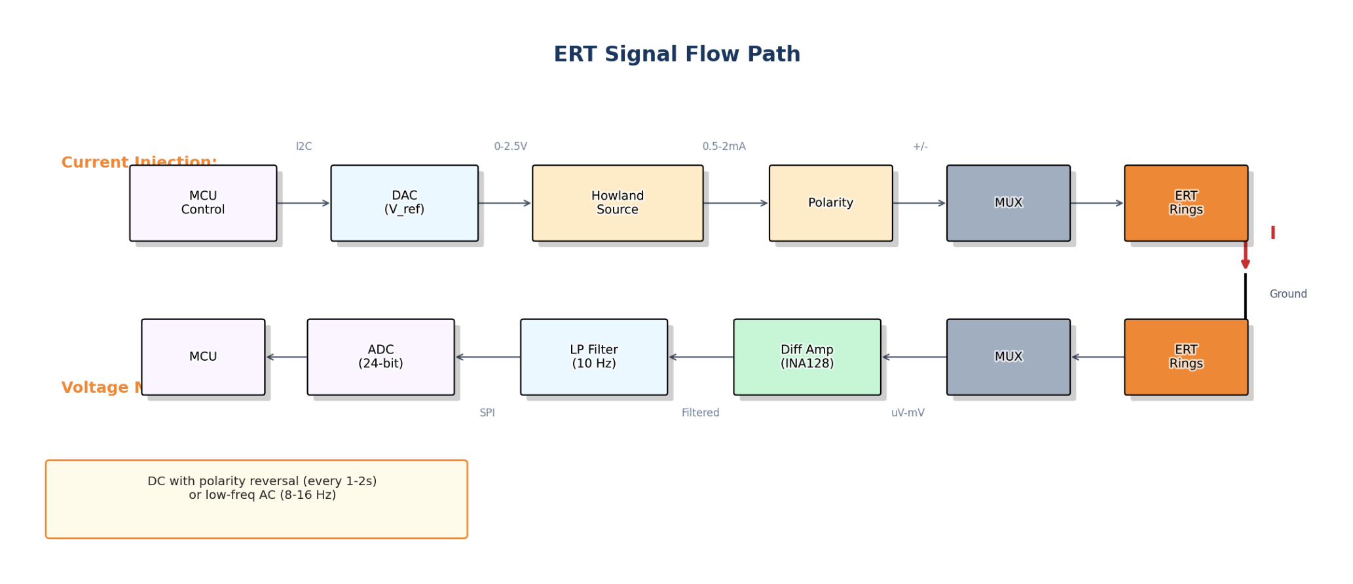
hirt/docs/_freeze/theory/architecture/figure-html/fig-ert-signal-flow-output-1.png
