chadlindell/terrascry/hirt/docs/_freeze/theory/architecture/figure-html/fig-hub-layout-output-1.png

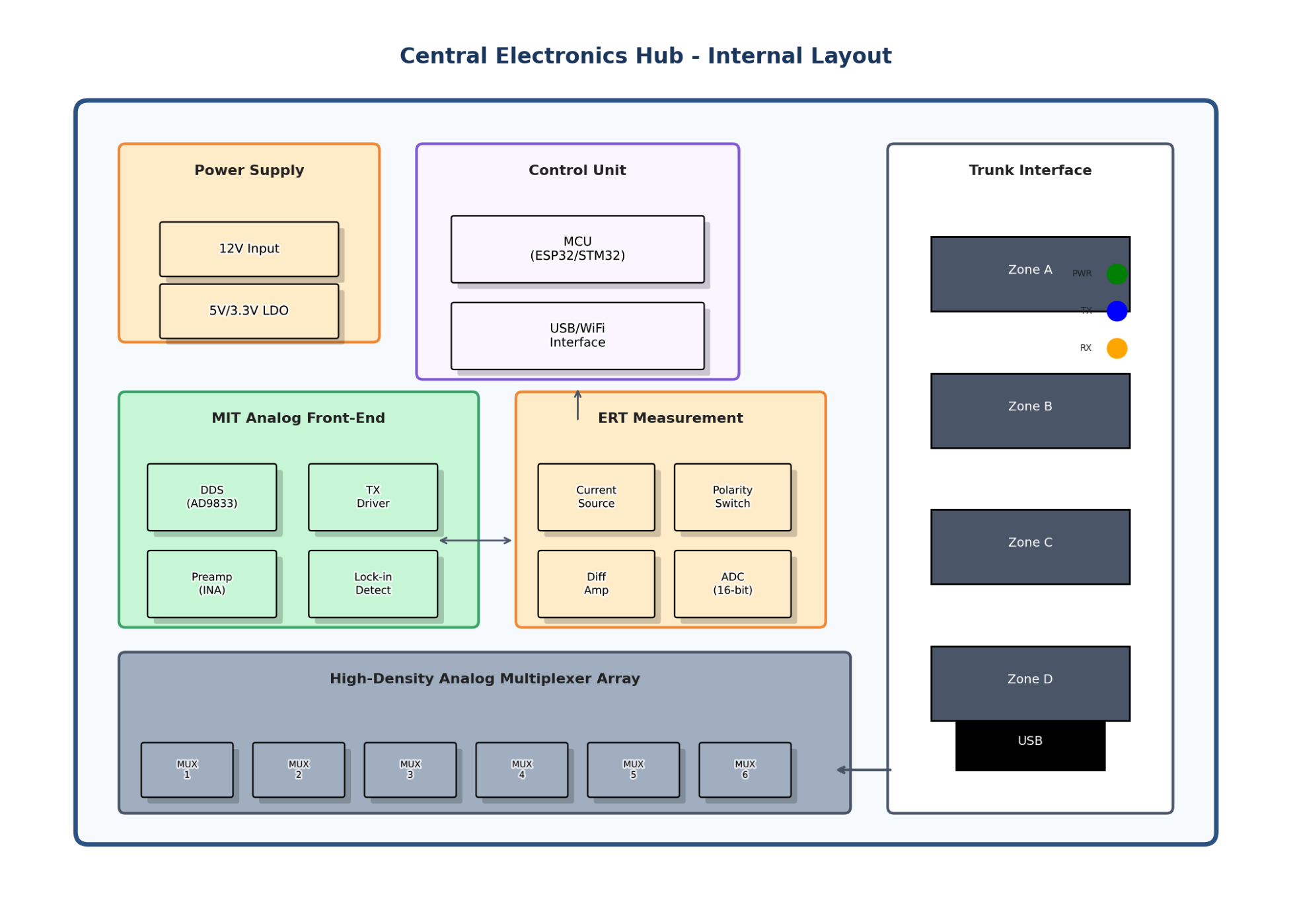
hirt/docs/_freeze/theory/architecture/figure-html/fig-hub-layout-output-1.png
