chadlindell/terrascry/hirt/docs/_freeze/theory/architecture/figure-html/fig-method-comparison-output-1.png

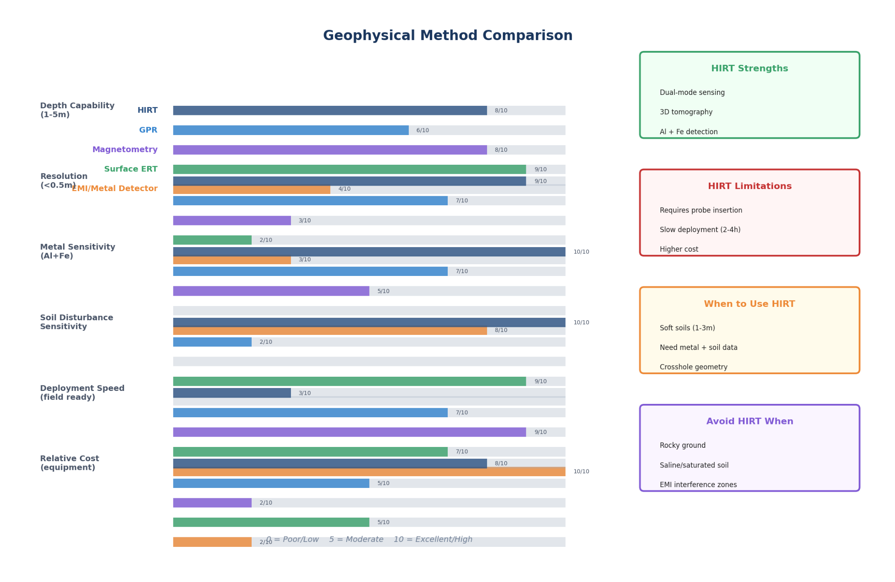
hirt/docs/_freeze/theory/architecture/figure-html/fig-method-comparison-output-1.png
