chadlindell/terrascry/hirt/docs/_freeze/theory/architecture/figure-html/fig-mux-topology-output-1.png

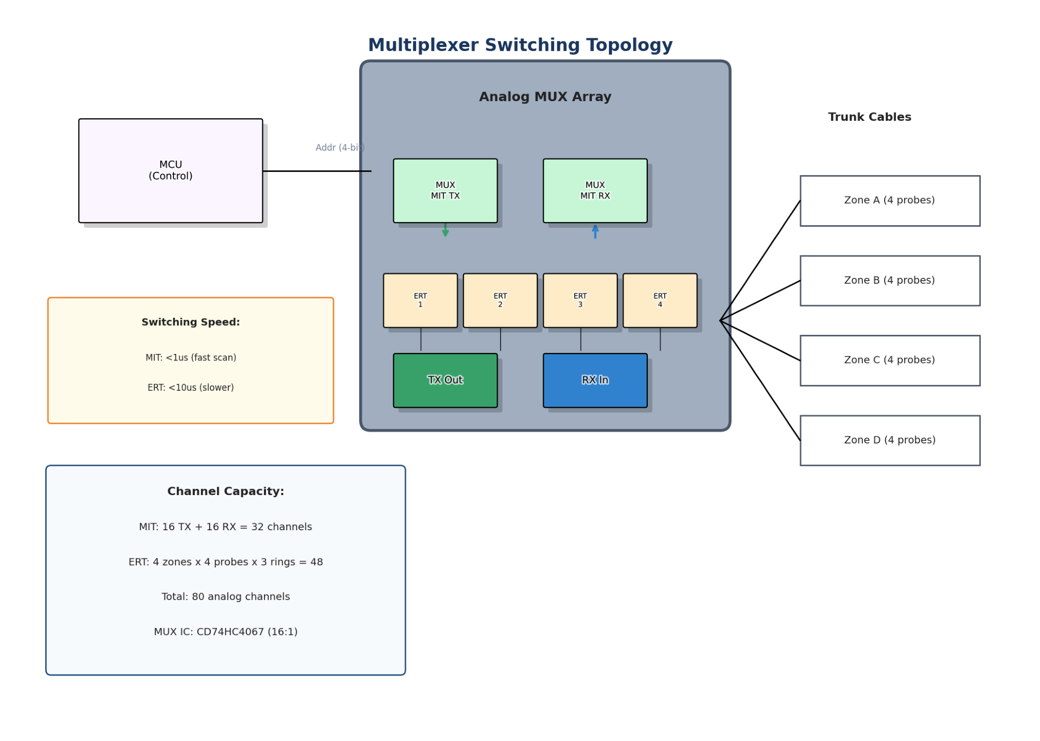
hirt/docs/_freeze/theory/architecture/figure-html/fig-mux-topology-output-1.png
