chadlindell/terrascry/hirt/docs/_freeze/theory/architecture/figure-html/fig-trunk-cable-output-1.png

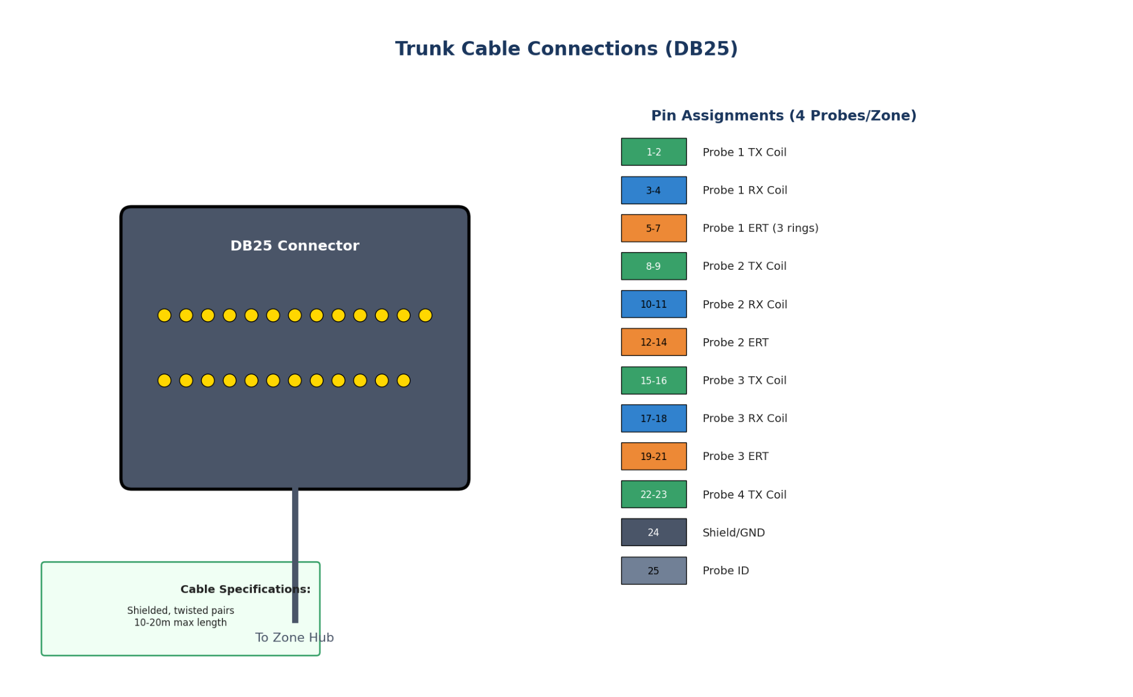
hirt/docs/_freeze/theory/architecture/figure-html/fig-trunk-cable-output-1.png
