chadlindell/terrascry/hirt/docs/_freeze/theory/physics/figure-html/fig-coupling-decay-output-1.png

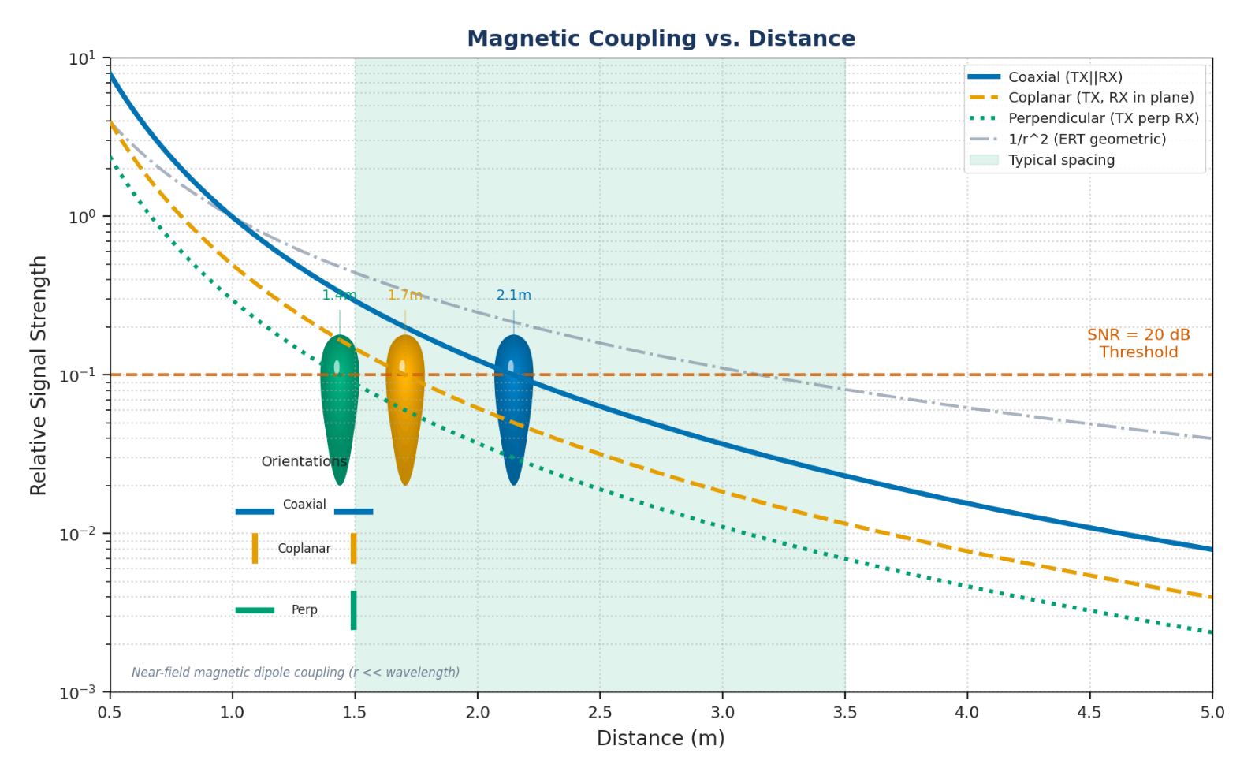
hirt/docs/_freeze/theory/physics/figure-html/fig-coupling-decay-output-1.png
