chadlindell/terrascry/hirt/docs/_freeze/theory/physics/figure-html/fig-ert-geometric-output-1.png

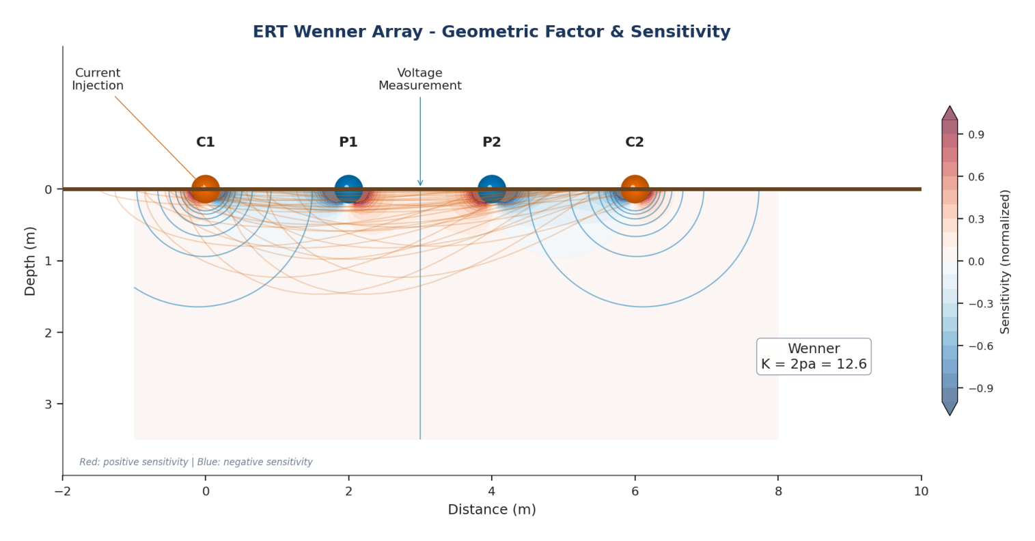
hirt/docs/_freeze/theory/physics/figure-html/fig-ert-geometric-output-1.png
