chadlindell/terrascry/hirt/docs/_freeze/theory/physics/figure-html/fig-frequency-response-output-1.png

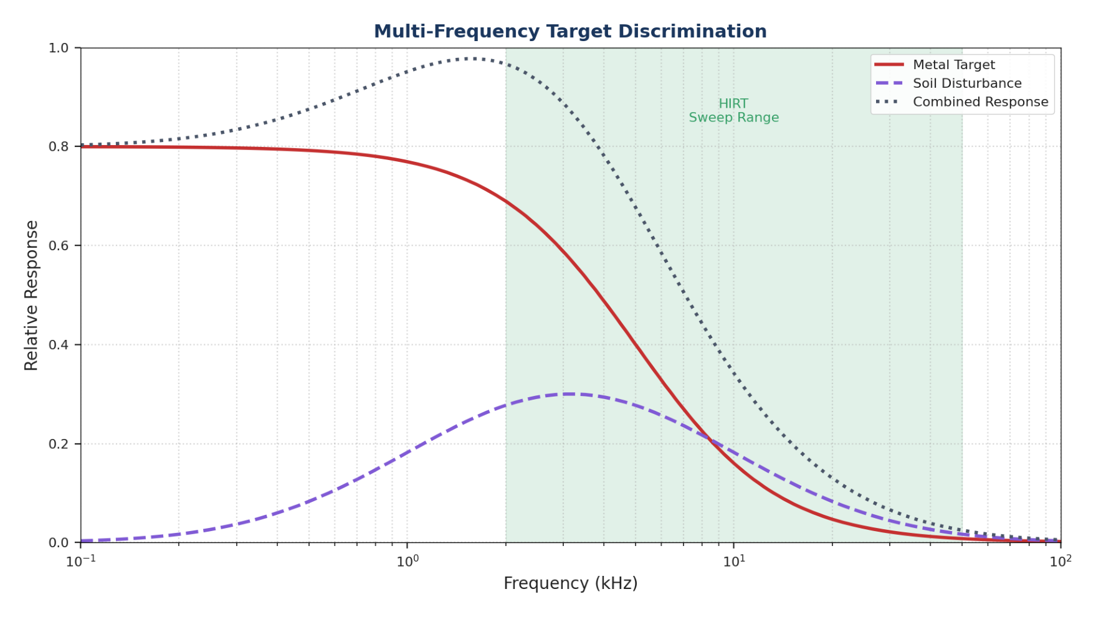
hirt/docs/_freeze/theory/physics/figure-html/fig-frequency-response-output-1.png
