chadlindell/terrascry/hirt/docs/_freeze/theory/physics/figure-html/fig-illumination-angle-comparison-output-1.png

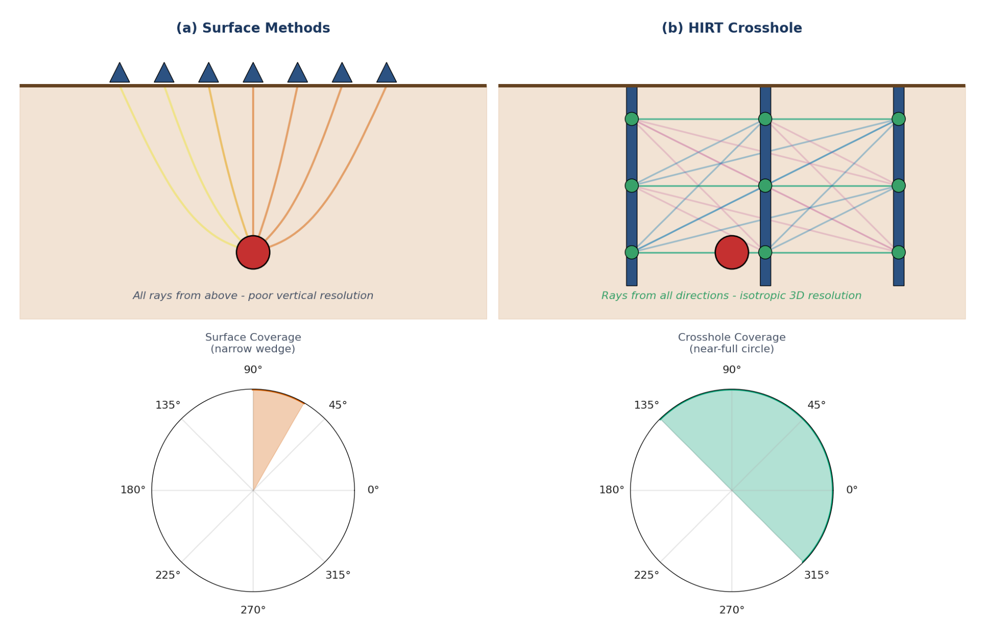
hirt/docs/_freeze/theory/physics/figure-html/fig-illumination-angle-comparison-output-1.png
