chadlindell/terrascry/hirt/docs/_freeze/theory/physics/figure-html/fig-ray-path-comparison-output-1.png

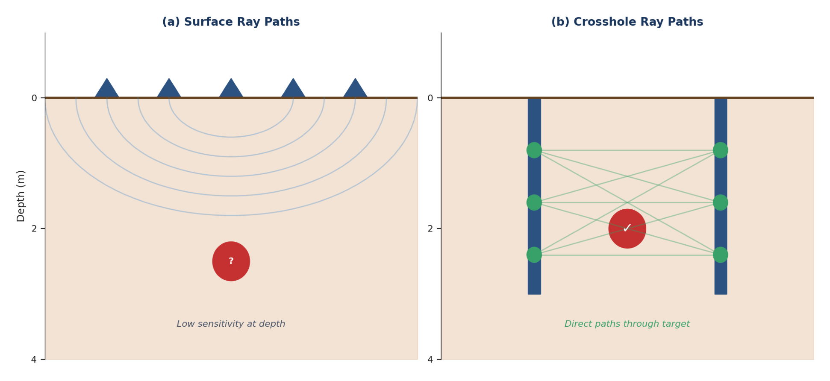
hirt/docs/_freeze/theory/physics/figure-html/fig-ray-path-comparison-output-1.png
