chadlindell/terrascry/hirt/docs/_freeze/theory/physics/figure-html/fig-resolution-depth-output-1.png

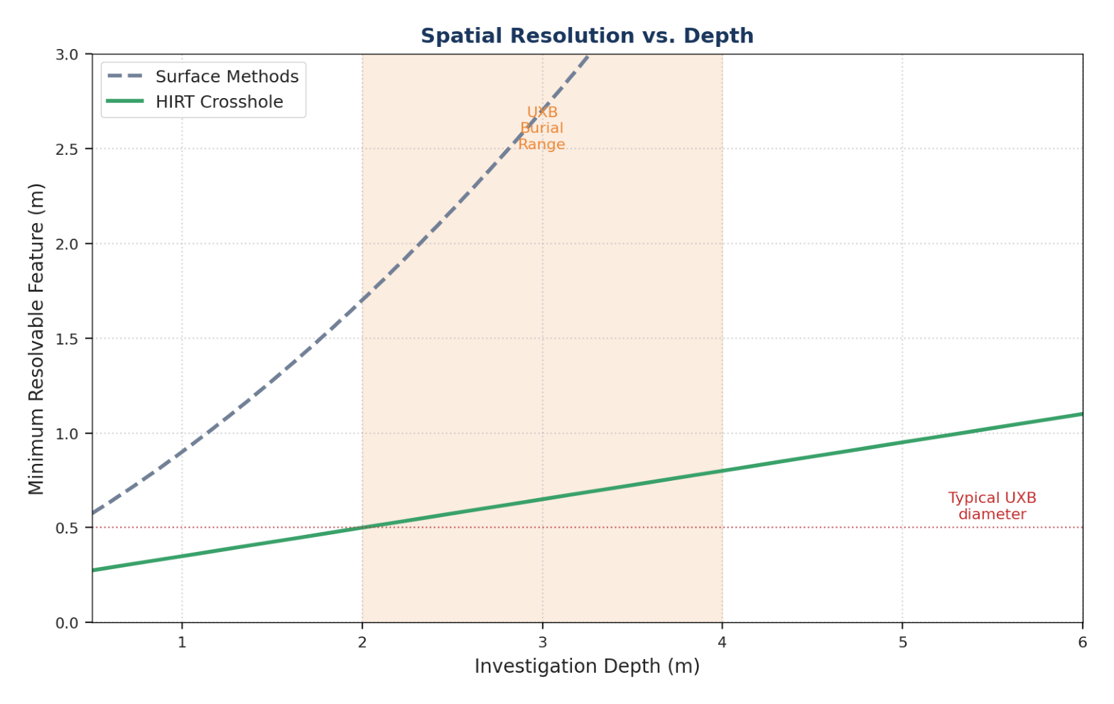
hirt/docs/_freeze/theory/physics/figure-html/fig-resolution-depth-output-1.png
