chadlindell/terrascry/hirt/docs/_freeze/theory/physics/figure-html/fig-skin-depth-output-1.png

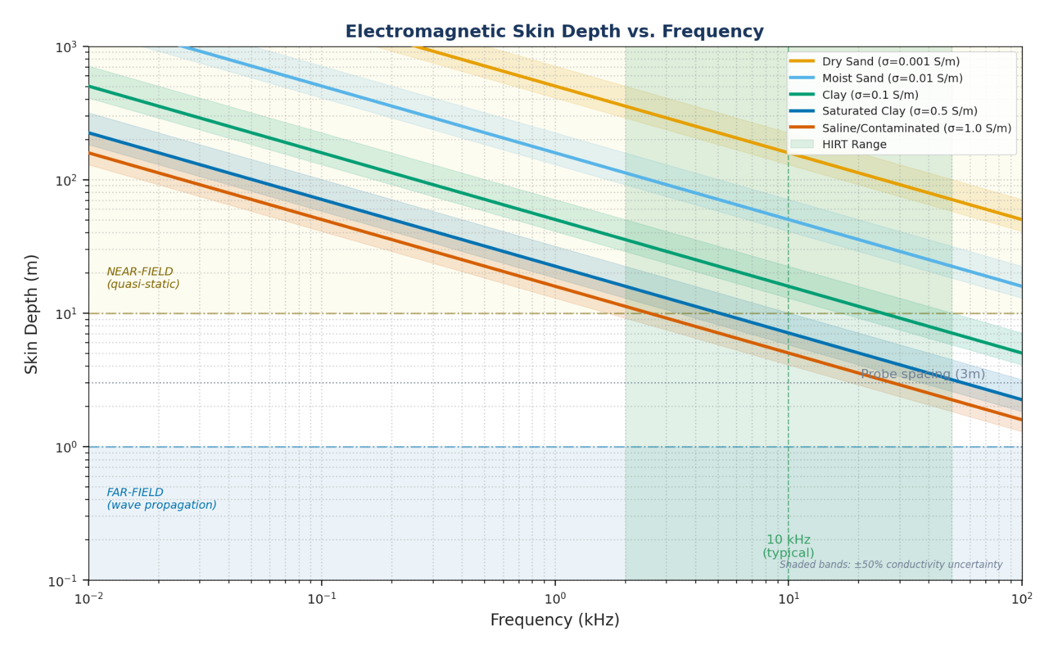
hirt/docs/_freeze/theory/physics/figure-html/fig-skin-depth-output-1.png
