chadlindell/terrascry/hirt/docs/_freeze/theory/physics/figure-html/fig-tx-rx-waveforms-output-1.png

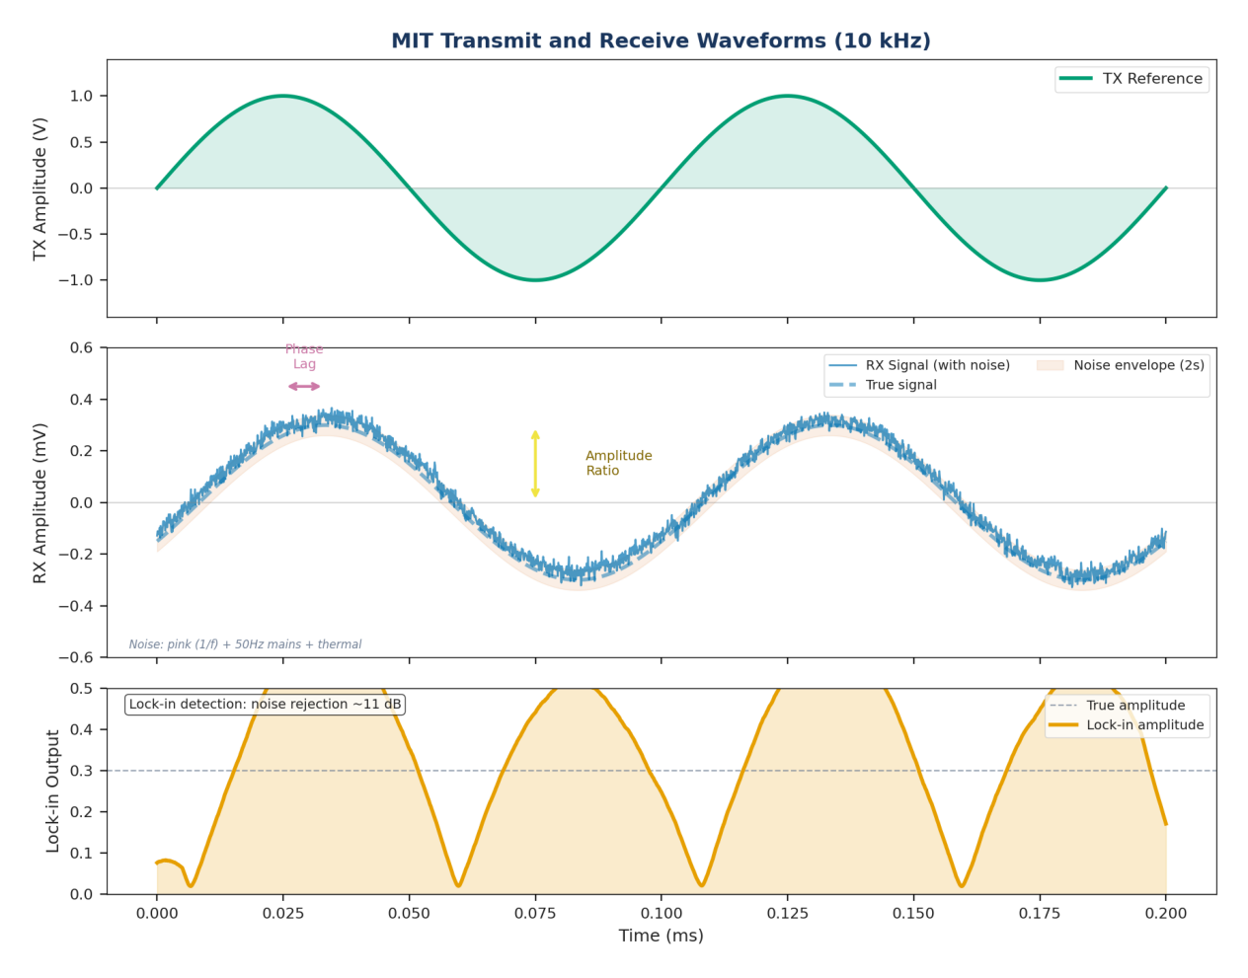
hirt/docs/_freeze/theory/physics/figure-html/fig-tx-rx-waveforms-output-1.png
