chadlindell/terrascry/hirt/docs/_freeze/theory/sensor-modalities/figure-html/fig-multimodal-fusion-output-1.png

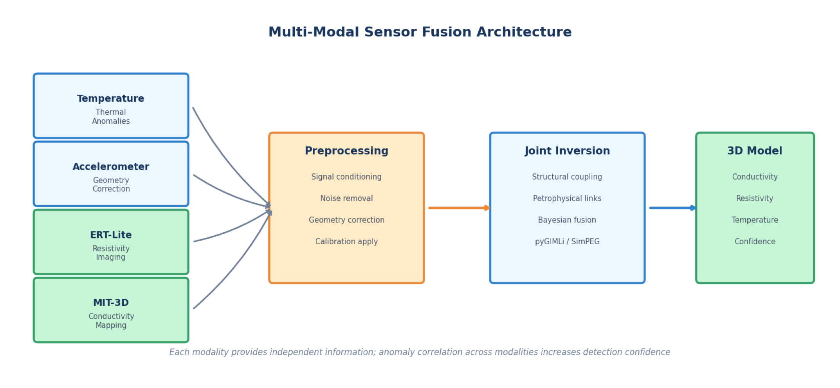
hirt/docs/_freeze/theory/sensor-modalities/figure-html/fig-multimodal-fusion-output-1.png
