chadlindell/terrascry/hirt/docs/_freeze/theory/sensor-modalities/figure-html/fig-sensor-maturity-output-1.png

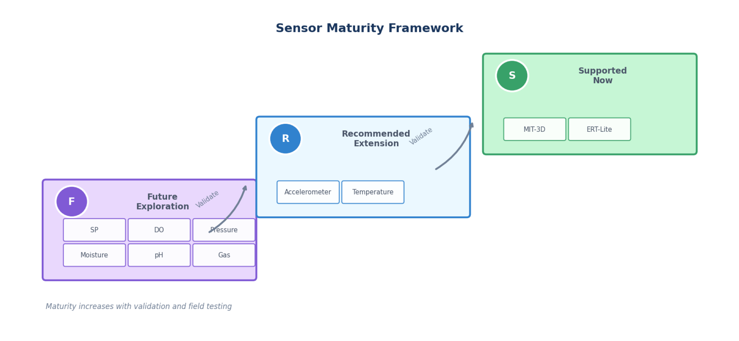
hirt/docs/_freeze/theory/sensor-modalities/figure-html/fig-sensor-maturity-output-1.png
