chadlindell/terrascry/hirt/docs/_freeze/theory/uncertainty/figure-html/fig-non-uniqueness-output-1.png

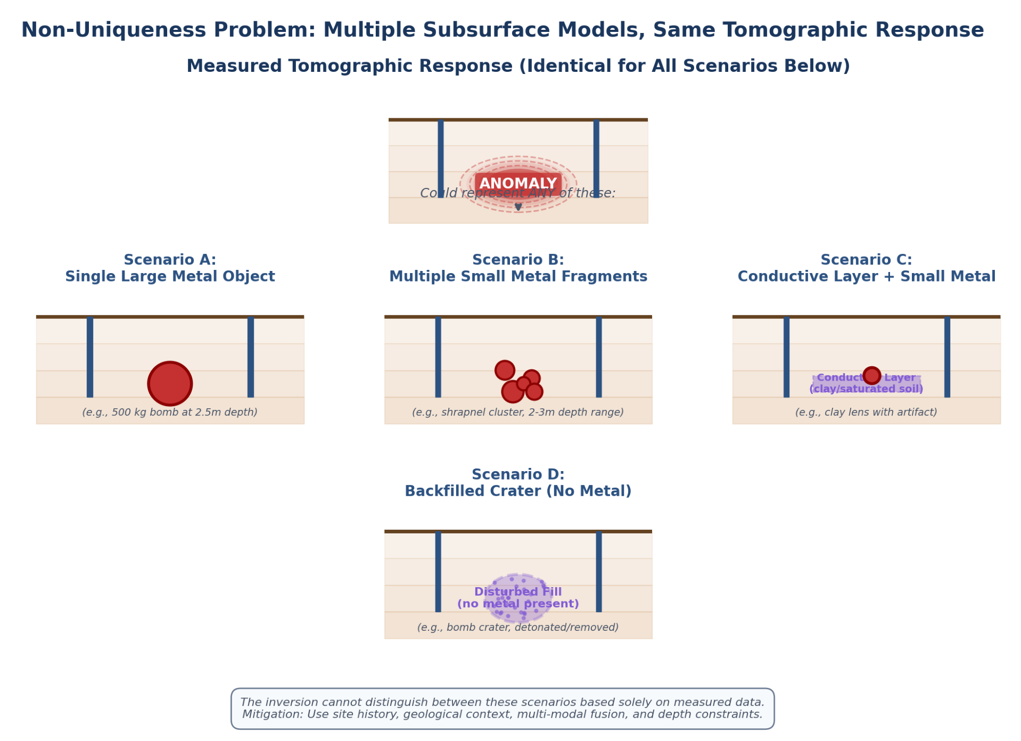
hirt/docs/_freeze/theory/uncertainty/figure-html/fig-non-uniqueness-output-1.png
