chadlindell/terrascry/hirt/docs/_freeze/theory/uncertainty/figure-html/fig-resolution-degradation-output-1.png

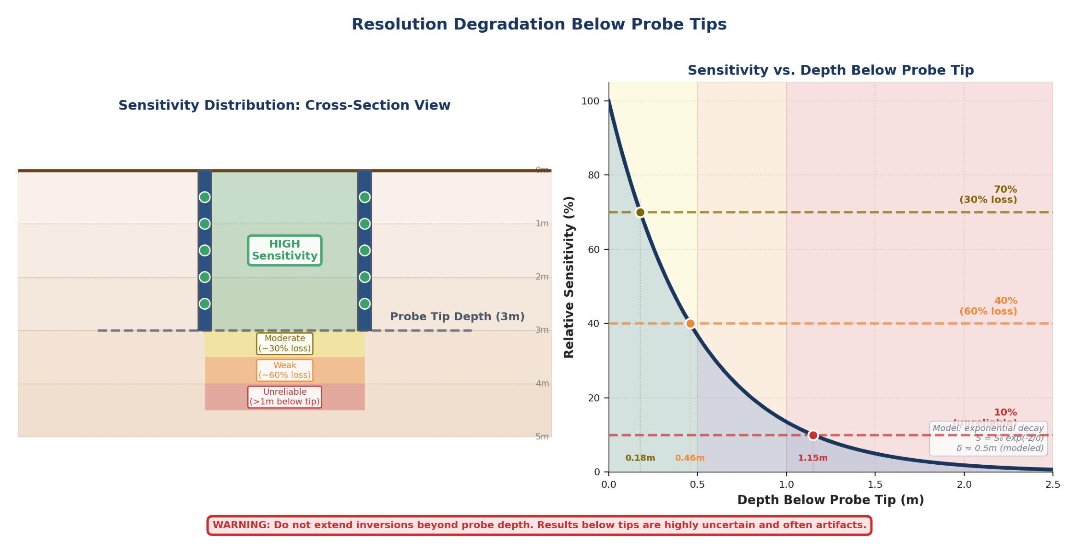
hirt/docs/_freeze/theory/uncertainty/figure-html/fig-resolution-degradation-output-1.png
