chadlindell/terrascry/hirt/docs/assets/images/cover_art.png

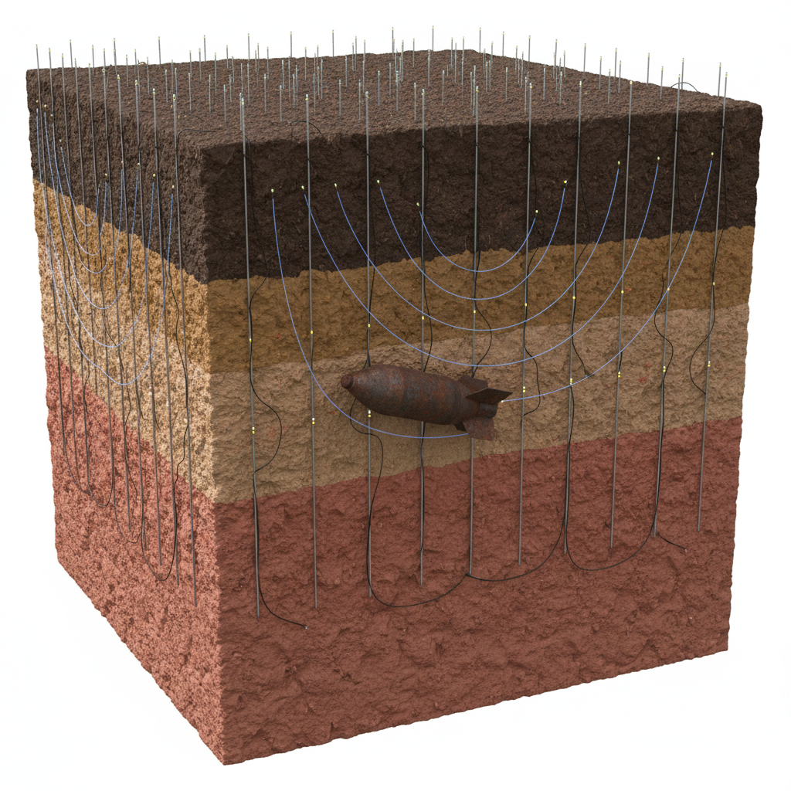
hirt/docs/assets/images/cover_art.png
