chadlindell/terrascry/hirt/docs/assets/images/field_deployment.png

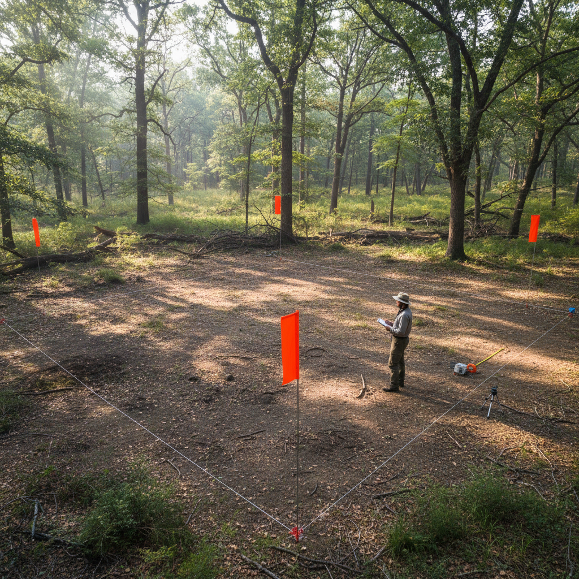
hirt/docs/assets/images/field_deployment.png
