chadlindell/terrascry/hirt/docs/assets/images/probe_tip_render.png

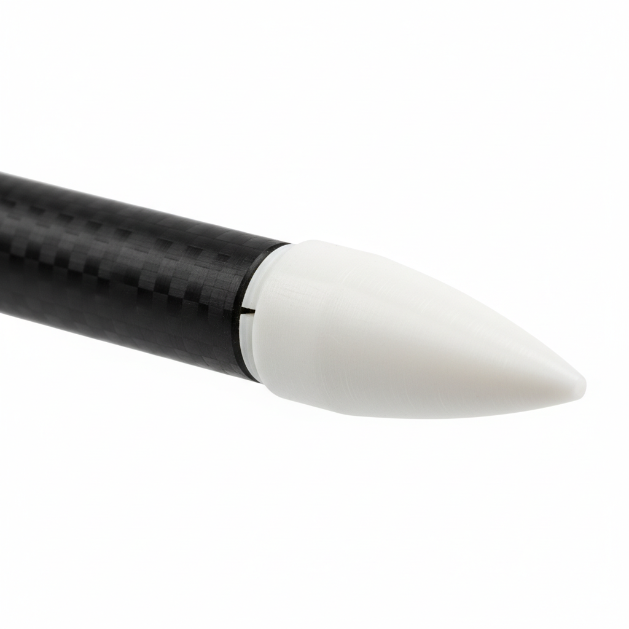
hirt/docs/assets/images/probe_tip_render.png
