chadlindell/terrascry/hirt/docs/assets/images/zone_hub_concept.png

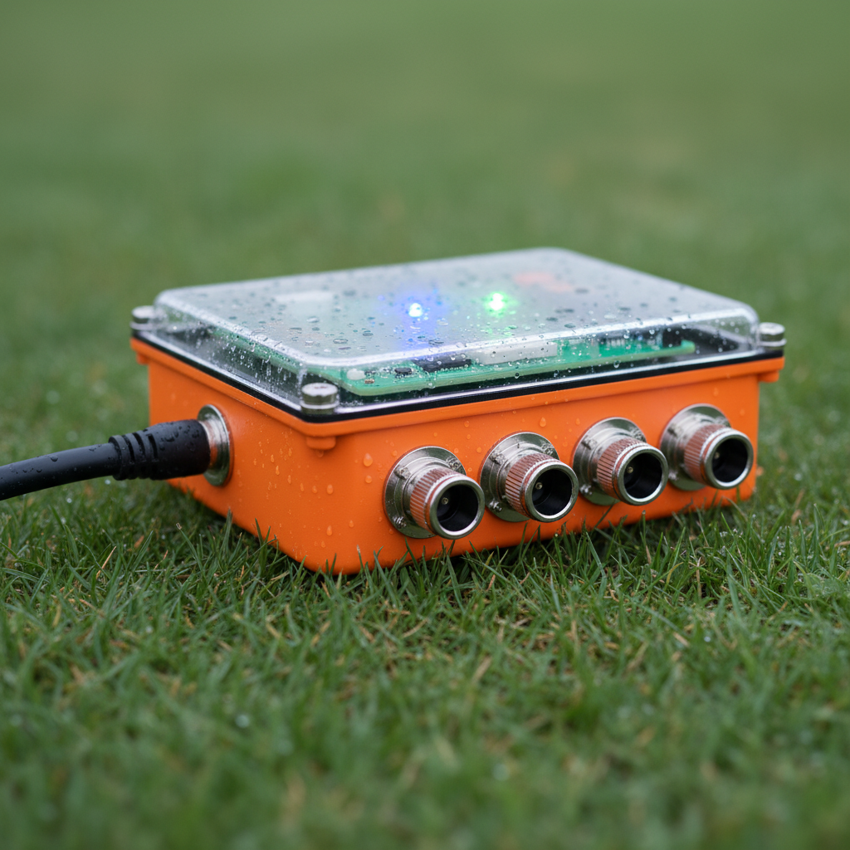
hirt/docs/assets/images/zone_hub_concept.png
