chadlindell/terrascry/hirt/hardware/bom/shared-components-bom.md

# Shared Components BOM (Bill of Materials)

**Tools, Supplies, and Shared Items** - Estimated cost: $200–400

## Field Tools

| Component | Description | Quantity | Unit Cost | Total Cost | Notes |
|---|---|---|---|---|---|
| Pilot rods | Steel rods (8–12 mm, 1–3 m) | 2–4 | $15–25 | $30–100 | For making holes |
| Driver | Hammer or driver for pilot rods | 1 | $20–40 | $20–40 | Manual or powered |
| Extraction tool | Probe puller/extractor | 1 | $30–60 | $30–60 | For removing probes |
| Flags | Survey flags for marking | 50 | $0.50–1 | $25–50 | Mark probe positions |
| Measuring tape | 30 m tape measure | 1 | $10–20 | $10–20 | Grid layout |
| **Subtotal Tools** | | | | **$115–270** | |

## Diagnostic Equipment

| Component | Description | Quantity | Unit Cost | Total Cost | Notes |
|---|---|---|---|---|---|
| Multimeter | Digital multimeter | 1 | $30–80 | $30–80 | Field diagnostics |
| Oscilloscope | Portable scope (optional) | 0–1 | $100–300 | $0–300 | Advanced debugging |
| LCR meter | For coil testing (optional) | 0–1 | $50–150 | $0–150 | Coil calibration |
| **Subtotal Diagnostics** | | | | **$30–530** | Optional items add cost |

## Fabrication Supplies

| Component | Description | Quantity | Unit Cost | Total Cost | Notes |
|---|---|---|---|---|---|
| 3D printing | Capsules, couplers (if outsourced) | 20–24 | $2–5 | $40–120 | Per probe |
| Machining | Custom parts (if needed) | 1 set | $50–100 | $50–100 | One-time |
| Soldering supplies | Solder, flux, wick | 1 set | $10–20 | $10–20 | Assembly |
| Wire and cable | Spare wire, connectors | 1 set | $20–40 | $20–40 | Spares |
| **Subtotal Fabrication** | | | | **$120–280** | Depends on DIY level |

## Spare Parts

| Component | Description | Quantity | Unit Cost | Total Cost | Notes |
|---|---|---|---|---|---|
| Spare probes | Complete spare probes | 2–4 | $70–150 | $140–600 | See probe BOM |
| Spare cables | Replacement cables | 2–4 | $5–10 | $10–40 | Per cable |
| Spare connectors | Various connectors | 1 set | $10–20 | $10–20 | Assorted |
| Fuses | Replacement fuses | 1 set | $2–5 | $2–5 | Various ratings |
| **Subtotal Spares** | | | | **$162–665** | Varies with spares level |

## Documentation and Supplies

| Component | Description | Quantity | Unit Cost | Total Cost | Notes |
|---|---|---|---|---|---|
| Field notebooks | Waterproof notebooks | 5–10 | $3–5 | $15–50 | Field logging |
| Calibration sheets | Printed calibration forms | 1 set | $5–10 | $5–10 | Per probe |
| Markers | Permanent markers | 5 | $1–2 | $5–10 | Labeling |
| Storage cases | For probes and equipment | 2–4 | $20–40 | $40–160 | Protection |
| **Subtotal Documentation** | | | | **$65–230** | |

## Total Shared Components Cost

| Category | Cost Range |
|---|---|
| Field Tools | $115–270 |
| Diagnostic Equipment | $30–530 |
| Fabrication Supplies | $120–280 |
| Spare Parts | $162–665 |
| Documentation and Supplies | $65–230 |
| **Total** | **$492–1,975** |

**Typical cost:** ~$200–400 (excluding optional diagnostic equipment and extensive spares)

## Notes

- Many tools may already be available
- Diagnostic equipment can be borrowed or shared
- 3D printing costs depend on access to printer
- Spare parts level depends on risk tolerance
- Some items can be purchased as needed

## Minimum Viable Set

Essential items only:
- Pilot rods: $30–100
- Basic tools: $50–100
- Basic diagnostics: $30–80
- Minimal spares: $50–100
- **Total minimum:** ~$160–380
