chadlindell/terrascry/hirt/docs/_freeze/build-guide/bill-of-materials/figure-html/fig-cost-breakdown-output-1.png

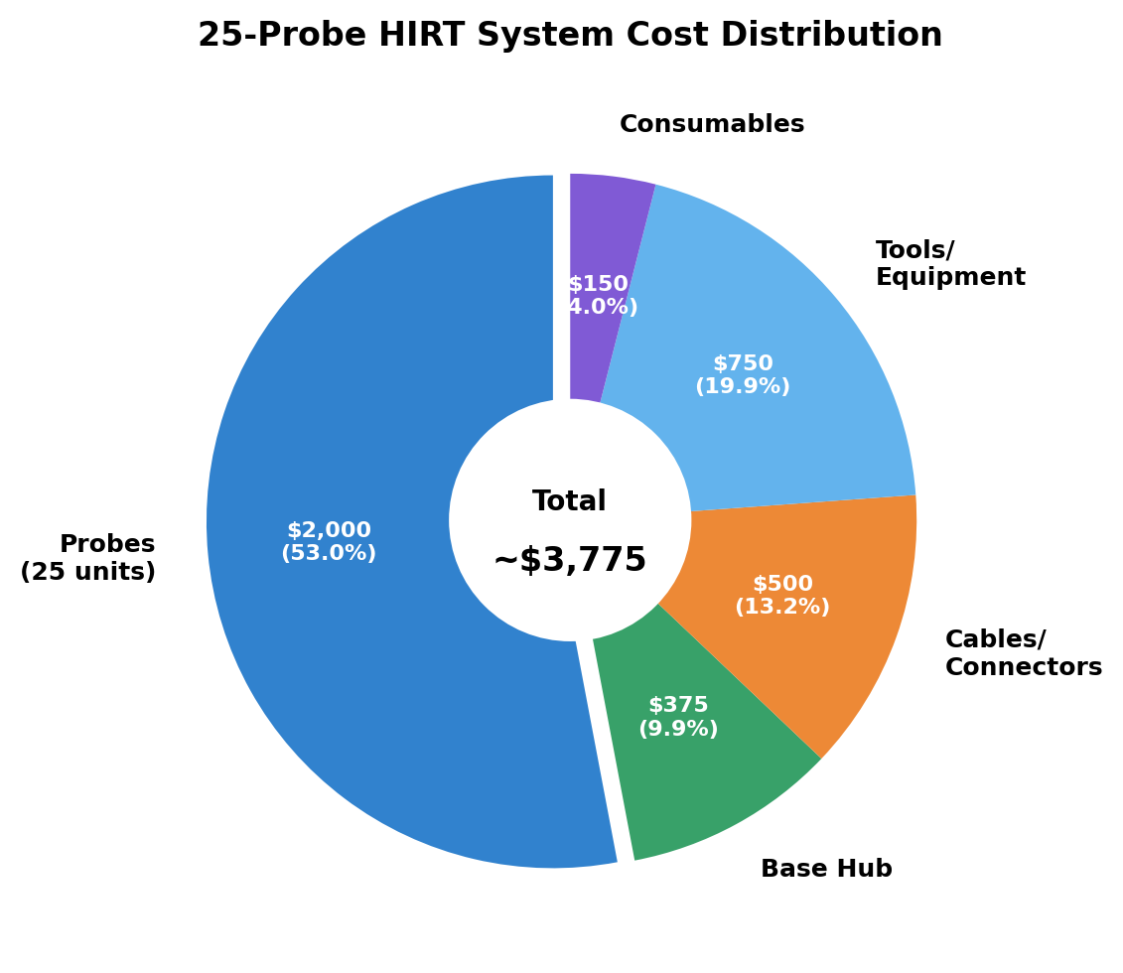
hirt/docs/_freeze/build-guide/bill-of-materials/figure-html/fig-cost-breakdown-output-1.png
