chadlindell/terrascry/hirt/docs/_freeze/theory/architecture/figure-html/fig-component-positioning-output-1.png

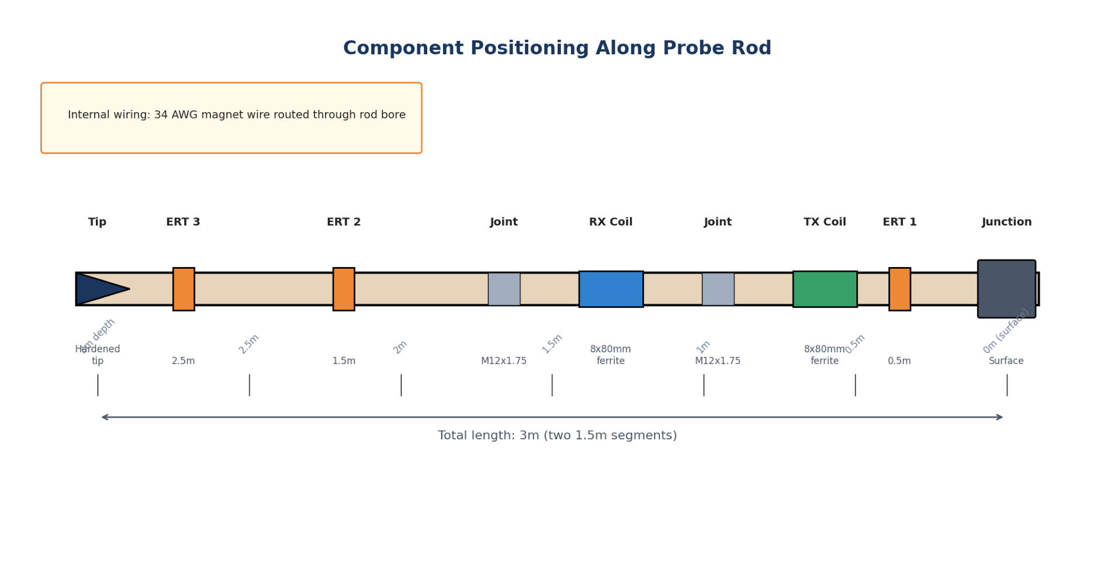
hirt/docs/_freeze/theory/architecture/figure-html/fig-component-positioning-output-1.png
