chadlindell/terrascry/hirt/docs/assets/images/assembly/component_callout.png

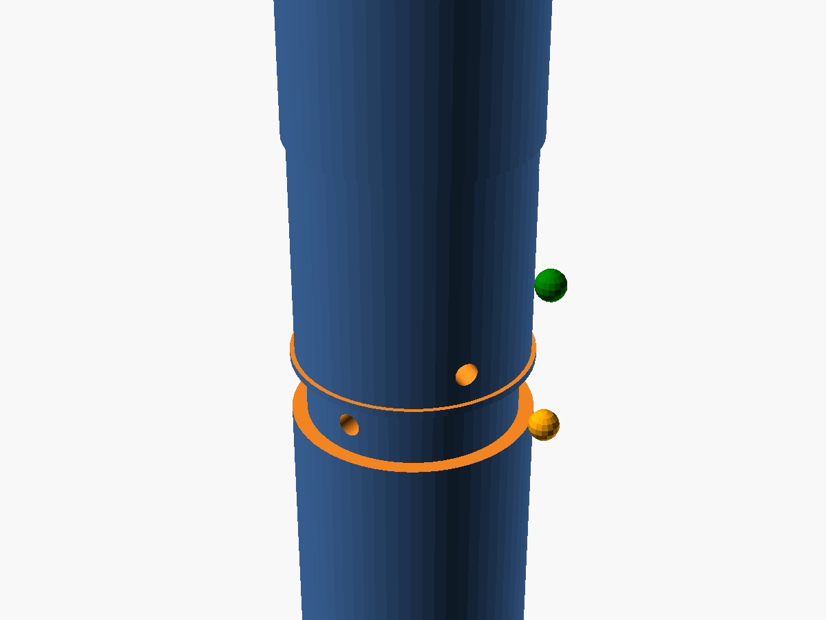
hirt/docs/assets/images/assembly/component_callout.png
