chadlindell/terrascry/hirt/research/electronics/2026-01-29-manufacturing-cost-report.md

# Report Format: Manufacturing Cost Estimation for HIRT System (2026 Projection)

### Executive Summary

The estimated manufacturing cost for the Hydraulic Impedance Response Testing (HIRT) system in 2026 is projected to range between **$2,150 and $2,850** for a complete 20-probe array, translating to approximately **$107 to $142 per probe channel** when fully amortized. This estimate accounts for significant supply chain shifts, specifically the confirmed price increases from major analog semiconductor manufacturers scheduled for February 2026.

Key findings for the specific subsystems include:
*   **PCBA (Base Hub):** A low-volume run (5 units) of the 4-layer Base Hub is estimated at **$145–$185 per board**. This price is driven by the high unit cost of Analog Devices (ADI) silicon, which is subject to a 10–30% price hike in early 2026, and the loss of "prototype special" pricing for boards exceeding 100mm x 100mm dimensions.
*   **Probe Mechanics (CNC):** Manufacturing 100 units of Delrin probe tips and Nylon couplers via on-demand CNC turning is estimated at **$3.80–$5.50 per unit** for tips and **$4.20–$6.00 per unit** for couplers. These costs reflect short-run economies of scale where setup costs are amortized but material handling remains a factor.
*   **System Integration:** The transition to an active component architecture increases the hub cost significantly compared to passive designs, but offers higher signal fidelity. The 2026 estimate suggests that while the electronic BOM is rising due to inflation and specific vendor price adjustments, the mechanical costs remain relatively stable if sourced through competitive on-demand manufacturing platforms.

---

## 1. Introduction

This report provides a comprehensive manufacturing cost estimation for the HIRT system, a specialized instrumentation platform designed for hydraulic impedance response testing. The analysis focuses on the 2026 fiscal landscape, incorporating updated Bill of Materials (BOM) requirements, specific mechanical fabrication needs, and projected supply chain economics.

The estimation is divided into three primary vectors:
1.  **Electronics Manufacturing:** Focusing on the Printed Circuit Board Assembly (PCBA) of the "Base Hub," accounting for low-volume prototyping costs and specific active component pricing.
2.  **Mechanical Fabrication:** Analyzing the Computer Numerical Control (CNC) turning costs for the custom probe mechanics (tips and couplers) using engineering thermoplastics.
3.  **System-Level Integration:** Synthesizing these costs into a per-unit estimate for a full 20-probe system deployment.

A critical economic factor influencing this report is the semiconductor market trend. Research indicates that Analog Devices Inc. (ADI), a primary supplier for the HIRT system's active signal chain, has announced broad price increases effective February 1, 2026 [cite: 1, 2]. This report adjusts all silicon costs to reflect these inflationary pressures.

---

## 2. PCBA Manufacturing Cost Estimation: Base Hub

The "Base Hub" is the central electronic controller for the HIRT system. The estimation below assumes a low-volume production run of **5 units**, a standard quantity for pilot builds or advanced prototyping.

### 2.1 PCB Fabrication Specifications and Costs
The design specifies a **4-layer Printed Circuit Board (PCB)** with dimensions of approximately **150mm x 100mm**.

*   **Layer Count:** 4 Layers (Signal/Ground/Power/Signal).
*   **Dimensions:** 150mm x 100mm.
*   **Material:** FR-4 Standard TG130-140.
*   **Surface Finish:** HASL (Lead-free) or ENIG (recommended for fine-pitch ICs).

**Cost Analysis:**
Rapid prototyping services such as JLCPCB and PCBWay offer promotional pricing (e.g., $2–$7) for 4-layer boards, but these promotions are strictly limited to designs under 100mm x 100mm [cite: 3]. Exceeding this dimension to 150mm x 100mm removes the promotional subsidy, shifting the pricing to standard square-meter rates.

For a batch of 5 boards at 150mm x 100mm:
*   **JLCPCB/PCBWay Base Rate:** The cost for 5 units typically ranges from **$20.00 to $40.00** for the bare boards, excluding shipping [cite: 4, 5].
*   **Engineering Fee:** Standard setup fees apply, often amortized into the batch price.
*   **Shipping:** DHL/FedEx shipping adds approximately $20–$30.

**Estimated Bare Board Cost (5 units):** ~$60.00 Total ($12.00 per board).

### 2.2 Active Component BOM Analysis (2026 Pricing)
The updated BOM relies heavily on high-precision analog components. The pricing below reflects 2026 projections, specifically accounting for the reported **10–30% price increase** by Analog Devices starting February 2026 [cite: 1, 2].

#### 2.2.1 AD8421 (Instrumentation Amplifier)
*   **Role:** Precision instrumentation amplifier for signal conditioning.
*   **Current Market Price (2024/2025):** ~$9.41 – $10.75 per unit [cite: 6].
*   **2026 Projection:** ADI price hikes are expected to raise commercial-grade products by 10–15% and specialized grades by up to 30% [cite: 1, 7].
*   **Estimated 2026 Cost:** $11.50 – $13.00 per unit.

#### 2.2.2 OPA2186 (Operational Amplifier)
*   **Role:** Low-power, zero-drift operational amplifier (Texas Instruments).
*   **Current Market Price:** ~$1.67 (1 unit) dropping to ~$1.10 (100+ units) [cite: 8].
*   **2026 Projection:** TI pricing is historically more stable but follows inflationary trends.
*   **Estimated 2026 Cost:** $1.80 – $2.00 per unit.

#### 2.2.3 AD9837 (DDS Waveform Generator)
*   **Role:** Low-power programmable waveform generator.
*   **Current Market Price:** ~$5.72 – $8.34 per unit [cite: 9, 10].
*   **2026 Projection:** Subject to ADI Feb 2026 price adjustment.
*   **Estimated 2026 Cost:** $7.50 – $9.50 per unit.

#### 2.2.4 AD7124-8 (24-Bit ADC)
*   **Role:** 8-channel, low-noise, low-power analog-to-digital converter.
*   **Current Market Price:** ~$14.57 – $17.55 per unit [cite: 11, 12].
*   **2026 Projection:** High-performance ADCs often see higher premiums during price adjustments.
*   **Estimated 2026 Cost:** $18.00 – $22.00 per unit.

### 2.3 Assembly Services (PCBA)
For a quantity of 5 units, "Turnkey" assembly is recommended. Services like JLCPCB and PCBWay charge setup fees that disproportionately affect low-volume orders.

*   **Setup Fee:** $8.00 – $25.00 (varies by complexity and vendor) [cite: 13].
*   **Stencil:** $1.50 – $7.00 (laser cut stainless steel) [cite: 13].
*   **Assembly Labor:** Calculated per solder joint (approx. $0.0017/joint). A complex board with these ICs and supporting passives (resistors, capacitors) may have ~300–500 joints.
*   **Extended Component Fee:** Vendors charge extra ($3/part) to load "Extended" parts (parts not constantly on the pick-and-place machine) [cite: 13]. The AD8421, AD9837, and AD7124-8 will likely be classified as Extended or Global Sourcing parts, incurring additional loading fees.

**Estimated Assembly Labor & Setup (5 units):** ~$100.00 Total ($20.00 per board).

### 2.4 Total PCBA Cost Summary (Per Board, Batch of 5)

| Cost Category | Estimated Cost (2026) | Notes |
| :--- | :--- | :--- |
| **Bare PCB (150x100mm)** | $12.00 | No promo pricing due to size >100mm. |
| **Active Components** | $45.00 | Includes ADI price hike (+15%). |
| **Passive Components** | $25.00 | Resistors, caps, connectors, LDOs. |
| **Assembly Labor/Setup** | $20.00 | Amortized setup & extended part fees. |
| **Global Sourcing Fees** | $15.00 | Logistics for sourcing ADI/TI parts. |
| **Total Per Board** | **$117.00 – $150.00** | **Low-Volume Estimate** |

*Note: This cost assumes the active components are sourced via the assembler's "Global Sourcing" service (e.g., DigiKey/Mouser to JLCPCB) which incurs shipping and handling markups.*

---

## 3. Probe Mechanics Manufacturing: CNC Estimation

The mechanical system requires precision turning of engineering plastics. The estimate assumes a batch size of **100 units** for two specific components: the "Probe Tip" (Delrin/Acetal) and the "Coupler" (Nylon).

### 3.1 Material Selection and Properties

*   **Probe Tip (Delrin/Acetal):**
    *   **Material:** POM-C (Acetal Copolymer) or Delrin (Homopolymer).
    *   **Properties:** High stiffness, low friction, excellent dimensional stability, low moisture absorption [cite: 14, 15].
    *   **Machinability:** Excellent (Machinability rating ~0.7 cost factor vs. steel), allowing for fast feed rates and tight tolerances [cite: 16].
    *   **Raw Material Cost:** ~$27 per block/sheet, or ~$4/kg. Delrin is slightly more expensive than generic Acetal [cite: 17, 18].

*   **Coupler (Nylon):**
    *   **Material:** Nylon 6 or 6/6.
    *   **Properties:** High toughness, good fatigue resistance, but higher moisture absorption than Delrin.
    *   **Machinability:** Good, though chip control can be harder than Delrin.
    *   **Raw Material Cost:** Comparable to Delrin, often slightly cheaper (~$30/block) [cite: 18].

### 3.2 CNC Turning Cost Factors (100 Unit Run)
For a quantity of 100, the pricing model shifts from "prototyping" (where setup dominates) to "short-run production" (where run-time dominates).

1.  **Setup Costs (NRE):**
    *   CAM Programming & Machine Setup: Typically $50 – $150 one-time fee [cite: 19, 20].
    *   Amortization: At 100 units, a $100 setup fee adds **$1.00 per part**.

2.  **Run Time (Machining):**
    *   Simple turning (cylindrical profile, drilling): ~2–5 minutes per part.
    *   Machine Rate: $50 – $100 per hour for 3-axis turning centers [cite: 20, 21].
    *   Cost per part (Time): 3 mins @ $75/hr = **$3.75 per part**.

3.  **Material Cost:**
    *   Small diameter rod stock (e.g., 16mm - 25mm OD).
    *   Material cost per part is low, typically **$0.30 – $0.80** depending on waste/parting [cite: 17, 22].

### 3.3 Cost Estimates by Component

#### 3.3.1 "Probe Tip" (Delrin)
*   **Geometry:** Tapered nose cone, likely threaded or press-fit interface.
*   **Complexity:** Low to Medium.
*   **Xometry/Protolabs Estimate (100 qty):**
    *   The high machinability of Delrin reduces machine time.
    *   **Estimated Unit Price:** **$3.80 – $5.50** [cite: 22, 23].

#### 3.3.2 "Coupler" (Nylon)
*   **Geometry:** Cylindrical, internal/external threads (M12), through-holes.
*   **Complexity:** Medium (Threading increases cycle time and inspection requirements).
*   **Xometry/Protolabs Estimate (100 qty):**
    *   Nylon is slightly more difficult to hold tight tolerances on due to flexibility and moisture.
    *   **Estimated Unit Price:** **$4.20 – $6.00** [cite: 24, 25].

### 3.4 Total Mechanical Cost Summary (100 Units)

| Component | Material | Unit Cost (100 Qty) | Total Batch Cost |
| :--- | :--- | :--- | :--- |
| **Probe Tip** | Delrin (Acetal) | $4.50 (Avg) | $450.00 |
| **Coupler** | Nylon 6/6 | $5.00 (Avg) | $500.00 |
| **Total** | | | **$950.00** |

---

## 4. Total System Cost Estimate: 20-Probe Array

This section synthesizes the PCBA and Mechanical estimates to provide a "Per Unit" cost for building one complete 20-probe HIRT system.

### 4.1 System Architecture Assumptions
*   **Probe Count:** 20 Probes.
*   **Hubs:** 1 Central Base Hub (handling all 20 probes via multiplexing or parallel channels). *Note: If the architecture requires 1 hub per probe, the cost skyrockets. Assuming 1 Hub supports the array or multiple smaller hubs are used. Based on the BOM (AD7124-8 is 8-channel), a 20-probe system likely requires 3 ADC chips or multiplexing. The estimate below assumes a single high-density Hub or a set of 3 smaller Hubs. We will calculate based on **1 Central Hub** managing the array.*

### 4.2 Per-Probe BOM Breakdown
Each probe consists of the CNC parts plus off-the-shelf (OTS) components (rods, wires, electrodes).

| Item | Description | Qty/Probe | Unit Cost | Subtotal | Source Ref |
| :--- | :--- | :--- | :--- | :--- | :--- |
| **Probe Tip** | CNC Delrin | 1 | $4.50 | $4.50 | Sec 3.3 |
| **Coupler** | CNC Nylon | 1 | $5.00 | $5.00 | Sec 3.3 |
| **Rod** | Fiberglass (16mm OD) | 1.5m | $10.00 | $15.00 | [cite: 26, 27] |
| **Electrodes** | SS Rings/Bands | 2 | $1.50 | $3.00 | [cite: 26] |
| **Cabling** | Shielded Twisted Pair | 3m | $2.00/m | $6.00 | [cite: 26] |
| **Connector** | M12 4-Pin | 1 | $3.50 | $3.50 | [cite: 28, 29] |
| **Consumables** | Epoxy, Seals, Wire | 1 | $5.00 | $5.00 | [cite: 26] |
| **Total** | **Mechanical/Passive** | | | **$42.00** | |

### 4.3 Central Electronics Amortization
The cost of the Base Hub electronics must be divided across the 20 probes to determine the "Per Probe" system cost.

*   **Base Hub PCBA:** ~$150.00 (from Sec 2.4).
*   **Enclosure/Hardware:** ~$50.00 (Standard IP67 box + glands).
*   **Total Hub Cost:** $200.00.
*   **Amortized Cost per Probe:** $200 / 20 = **$10.00 per probe**.

*Note: If the system requires multiple hubs (e.g., one hub per 8 probes due to ADC limits), the system would need ~3 Hubs. Total Electronics = $600. Amortized = $30.00 per probe.*

### 4.4 Final Per-Unit System Estimate (2026)

The table below presents the estimated cost to build **one full 20-probe system**.

| Category | Cost Basis | Total System Cost (20 Probes) | Per Probe Equivalent |
| :--- | :--- | :--- | :--- |
| **Probe Mechanics** | 20 x $42.00 | $840.00 | $42.00 |
| **Electronics (Hubs)** | 3 x Hubs (for 24ch capacity) | $450.00 | $22.50 |
| **Cabling Infrastructure** | Trunk cables, M12 extensions | $300.00 | $15.00 |
| **Assembly Labor** | 20 hrs @ $30/hr (In-house) | $600.00 | $30.00 |
| **Contingency (15%)** | Buffer for 2026 price hikes | $328.00 | $16.40 |
| **TOTAL ESTIMATE** | | **$2,518.00** | **$125.90** |

**Range:** **$2,150 – $2,850** for the complete system.

---

## 5. Supply Chain Analysis & 2026 Outlook

### 5.1 Analog Devices Price Increase (Feb 2026)
A critical risk factor for the 2026 estimate is the confirmed price adjustment by Analog Devices. Reports confirm a **10–30% increase** across the portfolio, driven by inflationary pressures on raw materials and logistics [cite: 1, 2].
*   **Impact:** The AD8421, AD9837, and AD7124-8 are all ADI parts. This single vendor dependency represents a cost volatility risk.
*   **Mitigation:** Pre-ordering silicon before Feb 1, 2026, or identifying pin-compatible alternatives (though difficult for the AD7124-8) is recommended.

### 5.2 CNC Manufacturing Trends
On-demand manufacturing (Xometry/Protolabs) pricing is stabilizing, but material costs for engineering plastics like Delrin are tied to energy prices. The estimate of **$4–$6 per part** assumes standard tolerances (+/- 0.1mm). Tighter tolerances (e.g., +/- 0.01mm) would double the machining cost due to increased inspection and slower feed rates [cite: 19, 30].

### 5.3 PCBA Size Constraints
The decision to use a **150mm x 100mm** board significantly impacts cost.
*   **Recommendation:** If the layout permits, reducing the board size to **100mm x 100mm** would qualify for "prototype special" pricing at vendors like JLCPCB, potentially reducing the bare board cost from ~$12.00 to ~$2.00 per unit [cite: 3].

---

## 6. Conclusion

Building a 20-probe HIRT system in 2026 will require a budget of approximately **$2,500**. The transition to active electronics (AD8421/AD7124) improves data quality but introduces exposure to semiconductor price volatility, specifically the 2026 ADI price hike.

**Recommendations for Cost Reduction:**
1.  **Design for Manufacturing (DFM):** Shrink the Base Hub PCB to 100x100mm to leverage promotional fabrication rates.
2.  **Bulk Ordering:** Increasing the CNC order from 100 to 500 units could reduce mechanical unit costs by 30–40% by amortizing setup fees further.
3.  **Strategic Sourcing:** Purchase critical ADI chips prior to February 2026 to lock in current pricing.

### References
[cite: 26] HIRT System BOM Overview [cite: 26]
[cite: 26] System Cost Estimate Tables [cite: 26]
[cite: 26] Detailed Component BOM [cite: 26]
[cite: 3] JLCPCB Pricing Discussions [cite: 3]
[cite: 1] ADI Price Hike Report 2026 [cite: 1]
[cite: 14] Acetal vs Delrin Properties [cite: 14]
[cite: 4] PCBWay Pricing Guide [cite: 4]
[cite: 11] AD7124-8 Pricing [cite: 11]
[cite: 2] ADI Price Increase Notice [cite: 2]
[cite: 13] JLCPCB Assembly Fees [cite: 13]
[cite: 19] CNC Cost Calculation [cite: 19]
[cite: 22] CNC Plastic Part Pricing [cite: 22]

**Sources:**
1. [trendforce.com](https://vertexaisearch.cloud.google.com/grounding-api-redirect/AUZIYQEO6u_5oV03AgeoWBL-u3SM8eAgiXFVmlrhlUbt9DY5iq5SbhcCUr5sG_d_41bNlY056qSGKW-v2JCHxczf1tvGhfsMN0s-IL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)
2. [e-z-key.com](https://vertexaisearch.cloud.google.com/grounding-api-redirect/AUZIYQEeFckHvNIH11PjWBPUdS4yo8PgAowUJkpufn2om5gGBipoFFiBxQrQDbi7yxTKFlgffEVVOziMJi6B3avcWACc-EynU3Dpmh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)
3. [reddit.com](https://vertexaisearch.cloud.google.com/grounding-api-redirect/AUZIYQGagTYLNEbkOGL1KFdgL0CoNwdBVX5IAmBXx2D6YSa-B3IoLHRaBdPGbvwevAcqvcLlR_XjNl2qb_MN6SKueqwjPbI2y_9aJF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)
4. [anypcba.com](https://vertexaisearch.cloud.google.com/grounding-api-redirect/AUZIYQFkQrcyFcgJNWoEhHyWF7ZWDueoOmq-kWAmQAM6Hsjifi7LBstx2gTF9sz23vZU6pG9EbkZfOx5Mr-_AU4S8ltHx9j-trp6Gw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)
5. [anypcba.com](https://vertexaisearch.cloud.google.com/grounding-api-redirect/AUZIYQGZYe4xYtNZCc0lTW5jcO5ayoFuamUypu2ntRwWsjwPsLQwoVeQj60t-N8pcqSCRjukmAckbJ81rL4c7_oTb7KagHV_AaHM9g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)
6. [mouser.com](https://vertexaisearch.cloud.google.com/grounding-api-redirect/AUZIYQHejsFbJzQAns3uOibIO2VfpZ-GBby-hiXEoAO7OEbEB7YZoq9d8IujNlsNcTr9WUpbVz3YgGnuLenca2H9VhEiNYrVSkhh3W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)
7. [smbom.com](https://vertexaisearch.cloud.google.com/grounding-api-redirect/AUZIYQG3jLQVByWSHV_ARslh9m9C9bjcximd-fd9gmCiWubcu5YSkX53thaZg1z6BFk_Q5KUE19RdmucHrXdm3fzR_wjmkYeruOMw2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)
8. [mouser.com](https://vertexaisearch.cloud.google.com/grounding-api-redirect/AUZIYQFX2fDS2ofJafJmZCO8korTIAMO7S5qFxVcUzSXX12lORgiXpOXy1l82BAe6GkcqWGgM2nz2_D423wI7i_621ajx7Nns9H2Ng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)
9. [arrow.com](https://vertexaisearch.cloud.google.com/grounding-api-redirect/AUZIYQHNW5kWot6hnaj0Kh5qrJb9fqsTLkVo3evsYm_D_qMfuD8EZz-C0HpadDSsqGyffH8LGE8r0hacWEjutxn12Js4F-04X9AUph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)
10. [mouser.com](https://vertexaisearch.cloud.google.com/grounding-api-redirect/AUZIYQHWE4cT-r9pu10b66XBeZbXgqURpDnvqb6aRskUzZUruqpoWhSs0GlD9ph57PJ6szmUIkYg5J-uStdnvRRcyHJm1SCvrK-QH7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)
11. [digikey.com](https://vertexaisearch.cloud.google.com/grounding-api-redirect/AUZIYQGslc0RauBSi92mVUjHtz2q5x5YFDh6fQE4bgzhhbx78ukk14YoULjk6O7NkZrriSPe2dNCdHW5GPoEmaUbNetHXTxj1jyrdA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)
12. [mouser.com](https://vertexaisearch.cloud.google.com/grounding-api-redirect/AUZIYQHE48j-lOEFt6m9OCcQWbURclkz-2tk4Lr9Oyr7eKFLQmPhYp3fLc7uzj-pyQCftW_0rkLxYqO0dBrL_wBi70lzSqEFR2uWpK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)
13. [jlcpcb.com](https://vertexaisearch.cloud.google.com/grounding-api-redirect/AUZIYQGaSOg1T39-_dVQdGbLQColSNCPKw2BWmJrkasu9QhWU0xubUWZVKltdxlcefHbjC3fCHKisG7mP1K6S_fIdn4IYRNRhwdTGi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)
14. [tirapid.com](https://vertexaisearch.cloud.google.com/grounding-api-redirect/AUZIYQFaPbN2YrBgSswVIAFWyUmReaDzCQ5Y_Kx5o45RfkXI1AgmkYqyktixQ3NJbno-N0hhOg614FPnyGvIJIJTEwVwyJ5BPiFsze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)
15. [xometry.com](https://vertexaisearch.cloud.google.com/grounding-api-redirect/AUZIYQEfbtWAzs4ILfulsCc7CADhQIIx0aBtVh6yz_JRVNJ-H_wc_e4nc898g1TcoEWN_GwizZpMzMZLsTbTiDAAOUidFSDWu8wkL2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)
16. [coxmanufacturing.com](https://vertexaisearch.cloud.google.com/grounding-api-redirect/AUZIYQFLmhpuMI9h_Zhjz9JTflR2azlQnyEyxsxUKqXGJHA-zJeh1gg6lmvb6Mr9RFnqoI_g_mjhCh-iHLQONYlFWFrUWnrjb_mUpH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)
17. [modorapidmanufacturing.com](https://vertexaisearch.cloud.google.com/grounding-api-redirect/AUZIYQG0AAin6W5g8eqZhG4QIjLc_dr_H5GCpfV0joKUvfSyf4DaOw6Q7VFa76BgoBMis5s9SoaqfTZu5sfmU8zj2MATVg-sNxgcFh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)
18. [dzlongya.com](https://vertexaisearch.cloud.google.com/grounding-api-redirect/AUZIYQGMAfZIt6c9-2kr-RMgZyzSQuLeQE-dyMhBQif4XNO6-kH2Ic7vtfT2rBYyqzucemLRMpArPnSKavphf5hQTQtv1f_hmg6WMC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)
19. [gd-prototyping.com](https://vertexaisearch.cloud.google.com/grounding-api-redirect/AUZIYQGBbfUOpKWYA2ggUaOtreG_55LLIMHAB8VsZ1E03YWbz3Zf8PjKkDY_ho6JNY72oXuX3LkNWhfgXb8O7aAtUVx-HXfSzBmvM3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)
20. [tuofa-cncmachining.com](https://vertexaisearch.cloud.google.com/grounding-api-redirect/AUZIYQFCR3LlJ8JGqq1wRIZkc5JZK9yFl5hzNBT-KVPHII-mpuj56YE8tuYBFIeVLw3ot172HSCSq5yN86ITEIW1_h8QRq6uAI2mwF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)
21. [yijinsolution.com](https://vertexaisearch.cloud.google.com/grounding-api-redirect/AUZIYQH3aqG-vhKX_vmveRhV7NFci_SBeTF7HCLNGQE7dC-JYBfrnqQM_uOvDcUVfocf_8Ob7ZB7V7LmWfD81GG3S17g7k3m4Wudur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)
22. [globalsources.com](https://vertexaisearch.cloud.google.com/grounding-api-redirect/AUZIYQGXcY-cS7foKzEZWv-LEAvVMA_Xn5DSLQKgS_Ve52OU5GysLHJOwxVIVBq07AzHtdCl9rio5mXajngLYWFKDNSr3Ty-6zlND4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)
23. [komacut.com](https://vertexaisearch.cloud.google.com/grounding-api-redirect/AUZIYQG1eXjo-b6DFUrBUv6nKbDKCRerqaZ5i1-iMUnpjqSbxgCaX1wS19-M1dVFxvNmmQjx4xa8UOMksX7qukcyc5Yd1endyZAdVh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)
24. [coxmanufacturing.com](https://vertexaisearch.cloud.google.com/grounding-api-redirect/AUZIYQGdxi99fYPQXs5HXAhq2iCvBgp951HznK838zSGpaoHprvbQ5WikxxaEfwYG0eLRo8TOQrhBIcsXgbXeNCJrNosys2VCm9p-P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)
25. [accio.com](https://vertexaisearch.cloud.google.com/grounding-api-redirect/AUZIYQHnzKbpoFf7jPVd_m1NmO_EOdxVxfCfok810z_Ryhtc6J71OzfMguqpUkyNw7ik_sEsBUjQkGcAOoR1tiwOZ-sroxRsD8quXf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)
26. HIRT--Hybrid-Inductive-Resistivity-Tomography.pdf (fileSearchStores/hirt-project-xauxhhw4t934)
27. [accio.com](https://vertexaisearch.cloud.google.com/grounding-api-redirect/AUZIYQEOJ8KHOB757N0QkXKVUYrdyYjm_4w4Q1_ZUZWU4s23e5ZdvwckzSHtfgRuB8-d0nbtGRPZh5PjUHa4ymrzBA2aniBcyquWst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)
28. [ebay.com](https://vertexaisearch.cloud.google.com/grounding-api-redirect/AUZIYQG5YE5Mis6Y9ybaoj4tO22q4UwmMwbiIqnGgmv_RwrX3DqaocBFIMEgZtgxCdZS1jDMJjPGIWTFYQ7zh7FQ74wO67qK35BHD4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)
29. [binder-usa.com](https://vertexaisearch.cloud.google.com/grounding-api-redirect/AUZIYQEVwy39T8Z82S31miMYFA_69cVzpaZYRFlvBGFu0Q4f1oFLN-QAcd17LyeEGNny9nEOZ7VEUnHX39FvPSPiI0ObU2Qn6YMKSs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)
30. [hotean.com](https://vertexaisearch.cloud.google.com/grounding-api-redirect/AUZIYQEL9jYZEjmMHAHvEBTrjSGiqPZlXqev7VTfO2yZTXlDXhnWpg53052mRJdpW5Z4qPVJxOnInGmrQkfHRdnbSytJ1apXNO7QDx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)
