chadlindell/terrascry/hirt/_archive/2024-legacy/images/assembly-photos/README.md

# Assembly Photos

This directory will contain photos documenting the assembly process.

## Planned Content

- Component photos
- Assembly step photos
- Finished probe photos
- Testing photos
