chadlindell/terrascry/hirt/docs/_freeze/build-guide/assembly/figure-html/fig-base-hub-stack-output-1.png

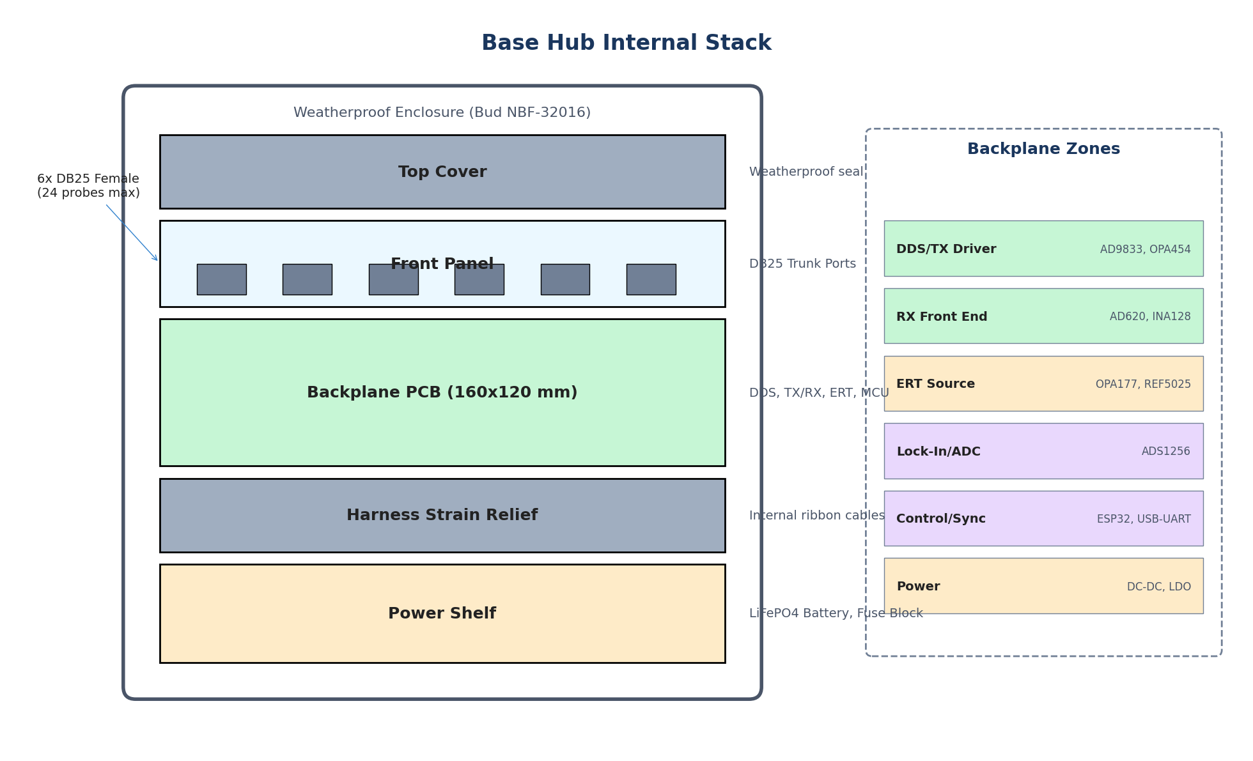
hirt/docs/_freeze/build-guide/assembly/figure-html/fig-base-hub-stack-output-1.png
