chadlindell/terrascry/hirt/docs/_freeze/build-guide/assembly/figure-html/fig-deployment-scene-output-1.png

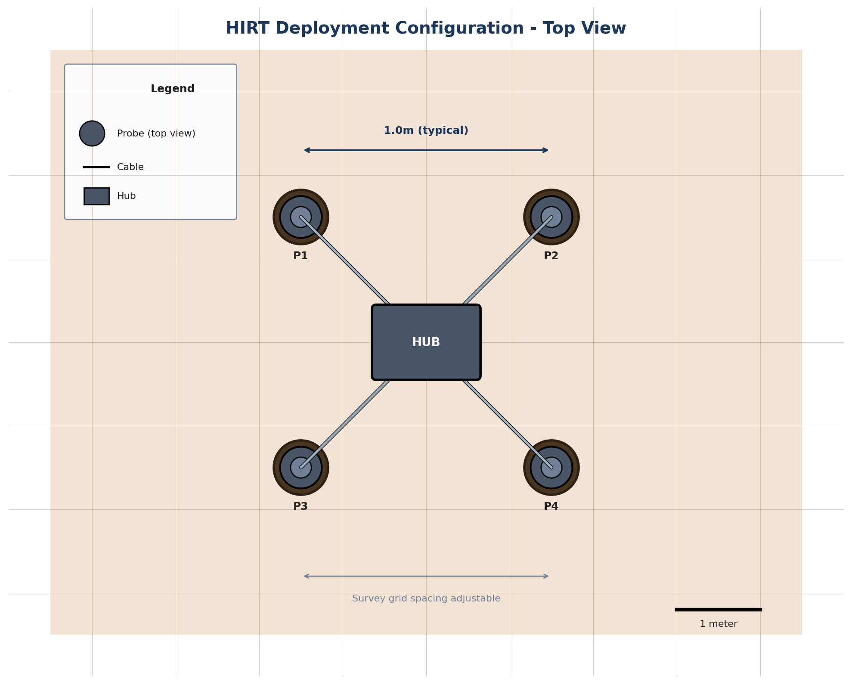
hirt/docs/_freeze/build-guide/assembly/figure-html/fig-deployment-scene-output-1.png
