chadlindell/terrascry/hirt/docs/_freeze/build-guide/assembly/figure-html/fig-field-assembly-sequence-output-1.png

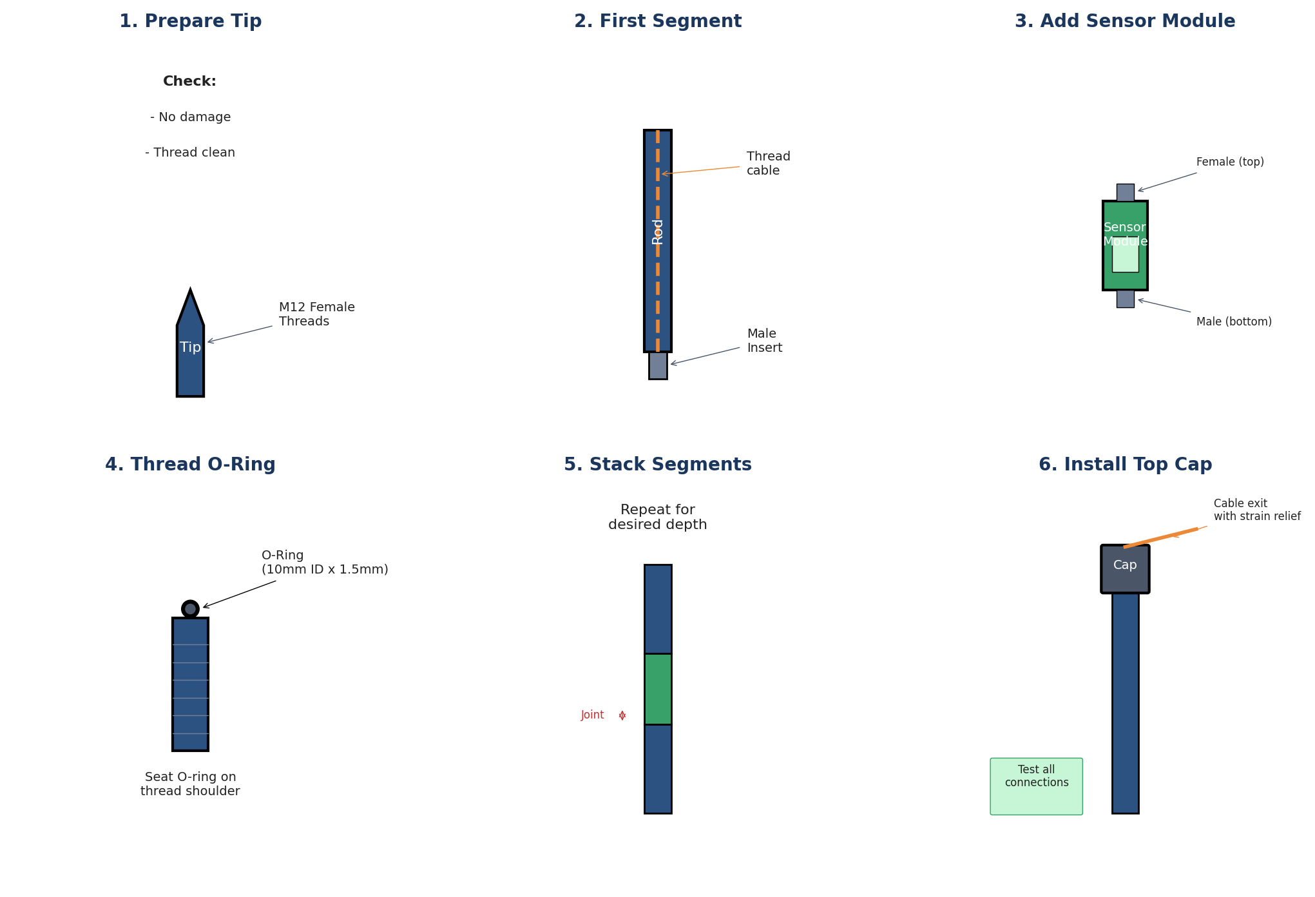
hirt/docs/_freeze/build-guide/assembly/figure-html/fig-field-assembly-sequence-output-1.png
