chadlindell/terrascry/hirt/docs/_freeze/build-guide/assembly/figure-html/fig-wiring-harness-output-1.png

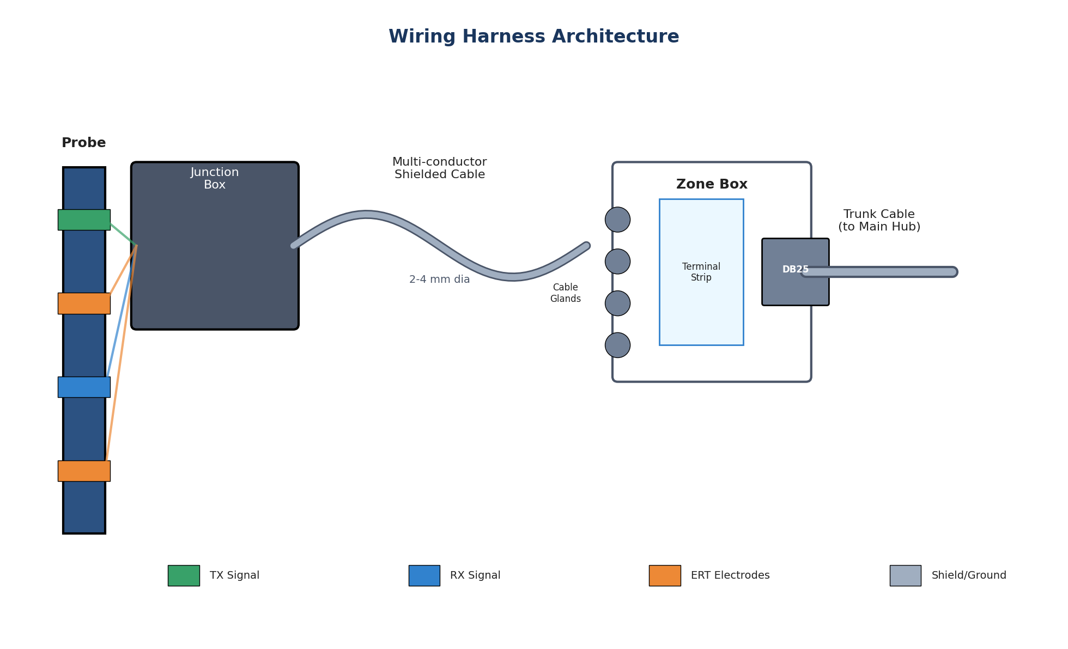
hirt/docs/_freeze/build-guide/assembly/figure-html/fig-wiring-harness-output-1.png
