chadlindell/terrascry/hirt/docs/_freeze/build-guide/calibration/figure-html/fig-known-target-setup-output-1.png

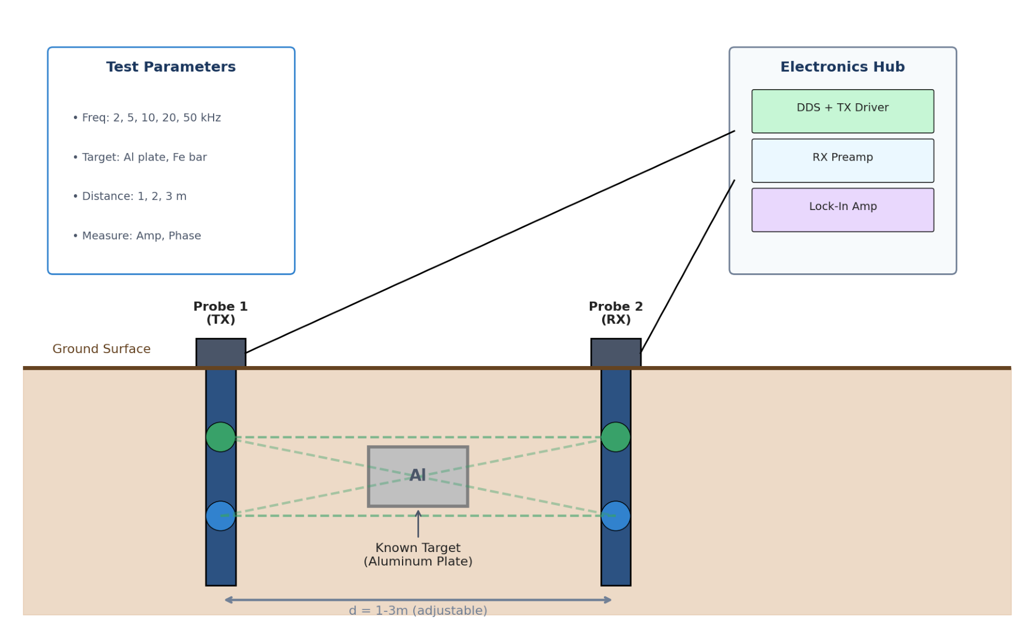
hirt/docs/_freeze/build-guide/calibration/figure-html/fig-known-target-setup-output-1.png
