chadlindell/terrascry/hirt/docs/_freeze/field-guide/deployment/figure-html/fig-ert-patterns-output-1.png

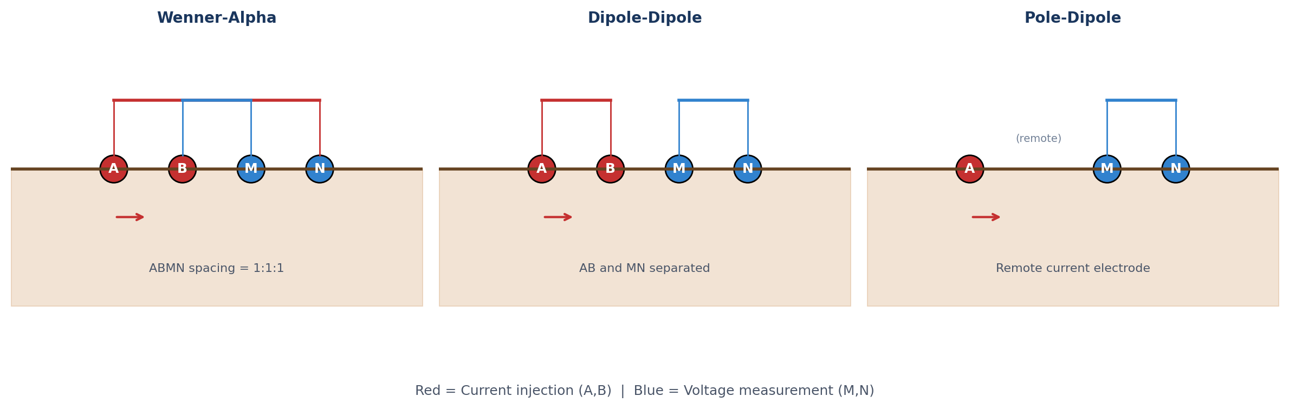
hirt/docs/_freeze/field-guide/deployment/figure-html/fig-ert-patterns-output-1.png
