chadlindell/terrascry/hirt/docs/_freeze/field-guide/deployment/figure-html/fig-grid-layout-output-1.png

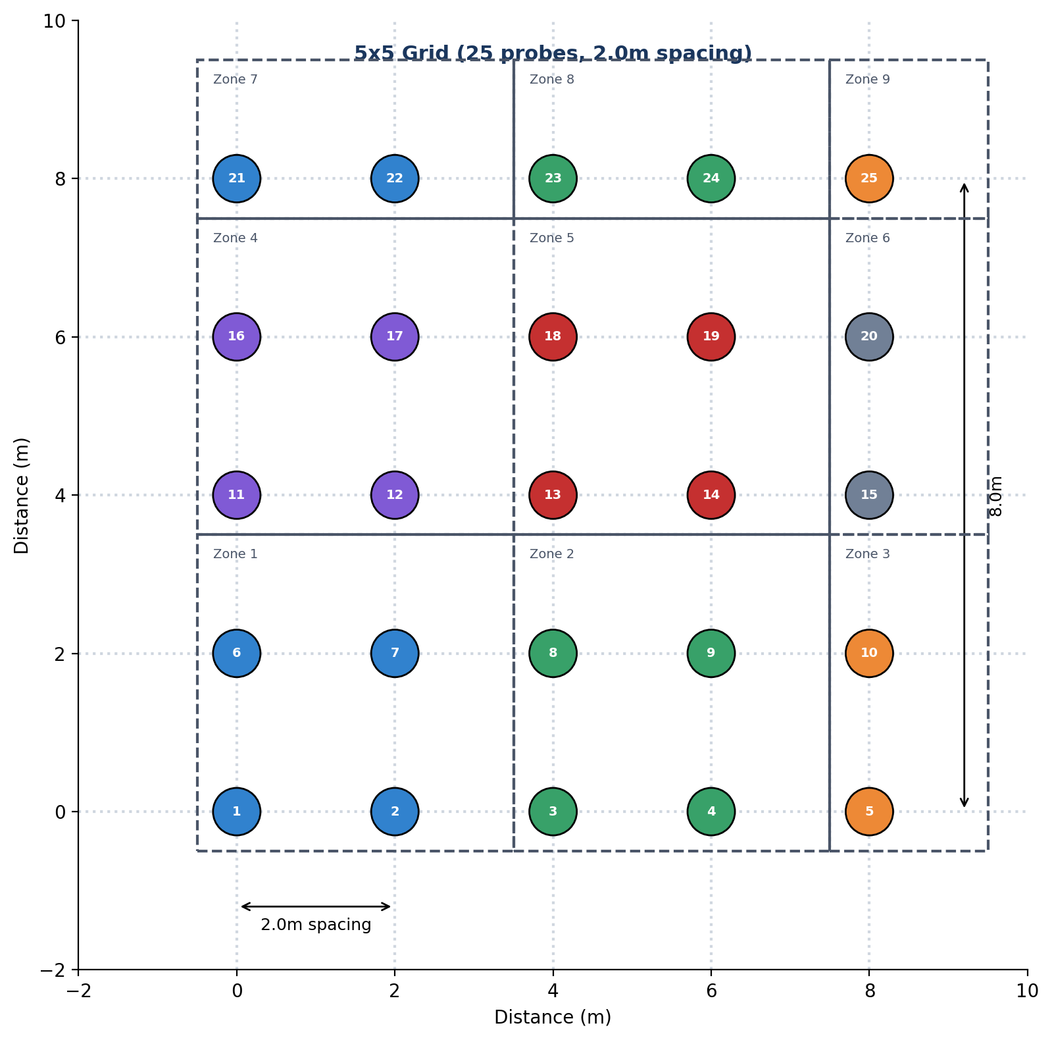
hirt/docs/_freeze/field-guide/deployment/figure-html/fig-grid-layout-output-1.png
