chadlindell/terrascry/hirt/docs/_freeze/field-guide/deployment/figure-html/fig-soil-decision-tree-output-1.png

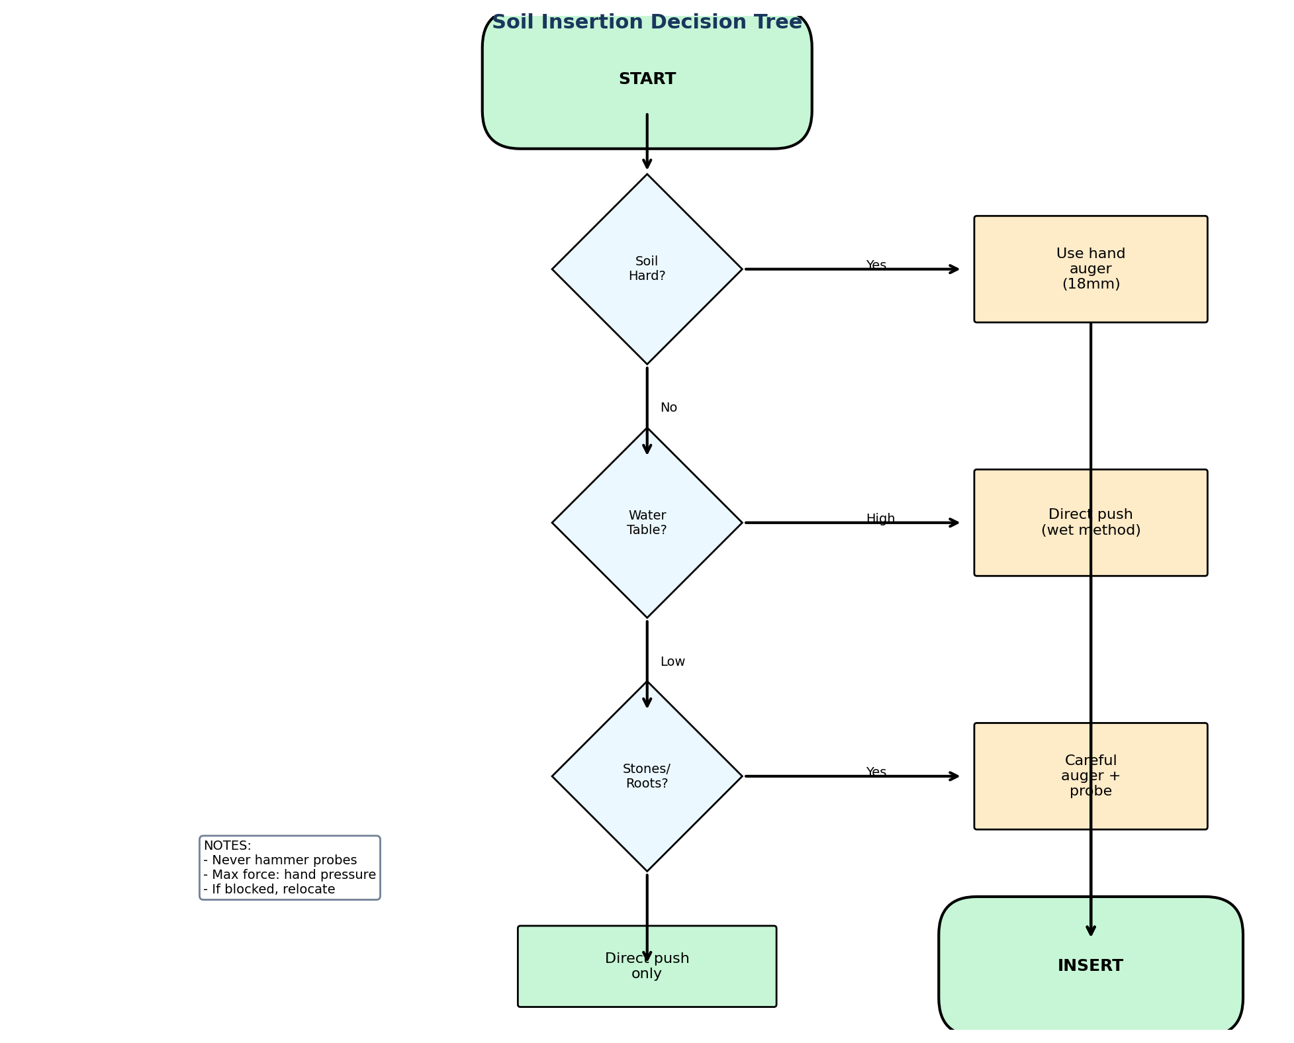
hirt/docs/_freeze/field-guide/deployment/figure-html/fig-soil-decision-tree-output-1.png
