chadlindell/terrascry/hirt/docs/_freeze/field-guide/deployment/figure-html/fig-survey-workflow-output-1.png

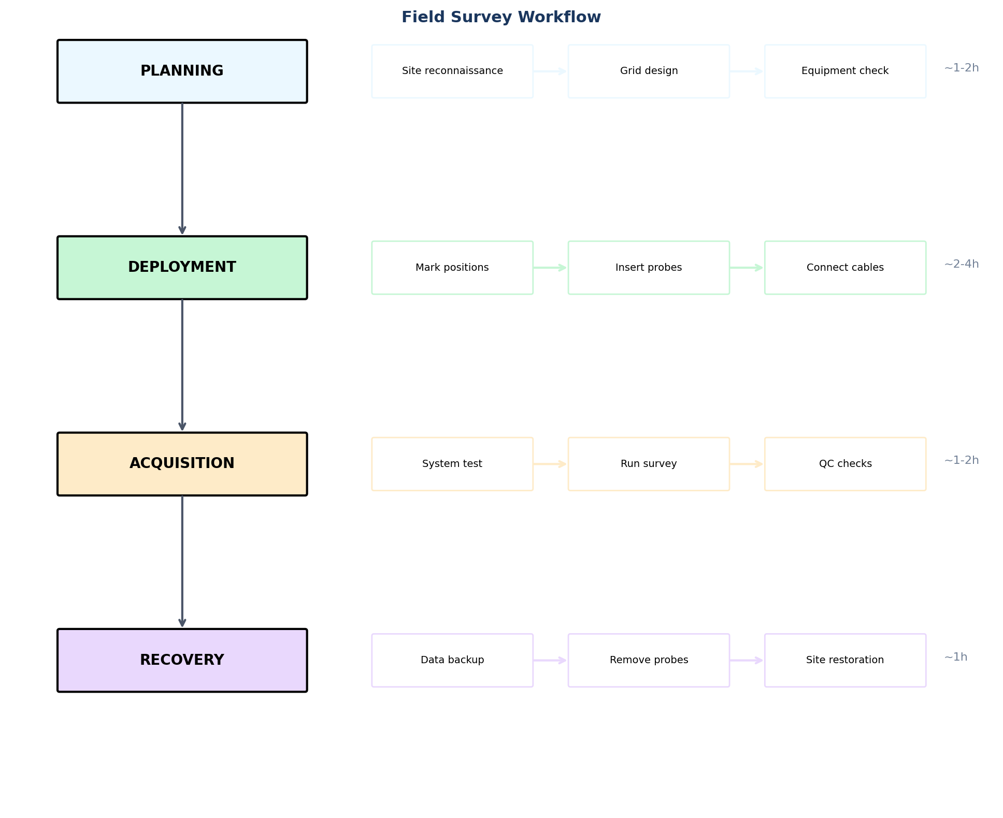
hirt/docs/_freeze/field-guide/deployment/figure-html/fig-survey-workflow-output-1.png
