chadlindell/terrascry/hirt/docs/_freeze/field-guide/progressive-deployment/figure-html/fig-deployment-decision-tree-output-1.png

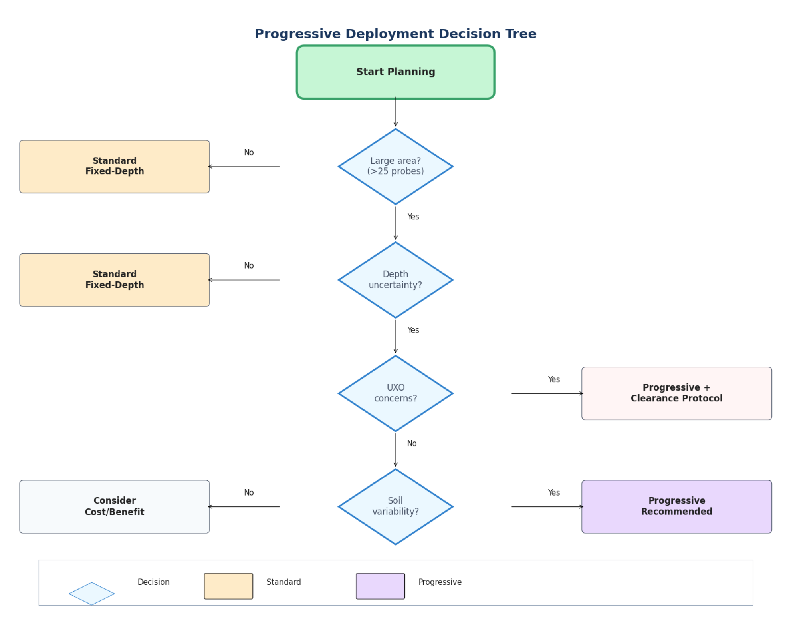
hirt/docs/_freeze/field-guide/progressive-deployment/figure-html/fig-deployment-decision-tree-output-1.png
