chadlindell/terrascry/hirt/docs/_freeze/field-guide/progressive-deployment/figure-html/fig-depth-profile-comparison-output-1.png

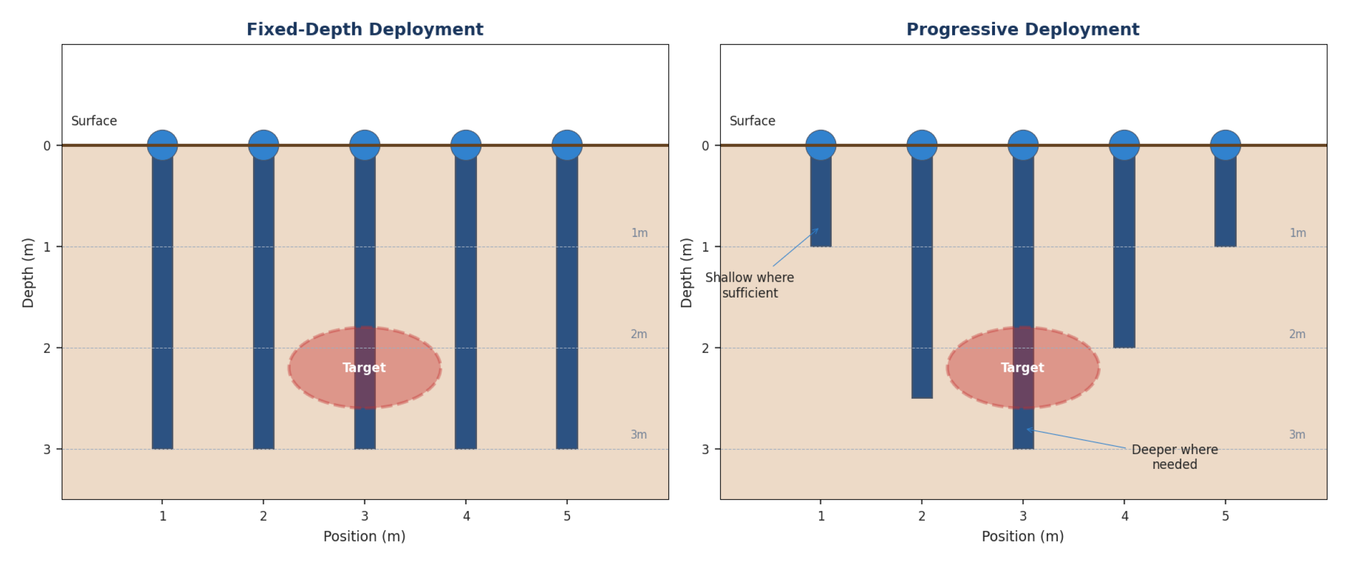
hirt/docs/_freeze/field-guide/progressive-deployment/figure-html/fig-depth-profile-comparison-output-1.png
