chadlindell/terrascry/hirt/docs/_freeze/field-guide/progressive-deployment/figure-html/fig-progressive-cross-section-output-1.png

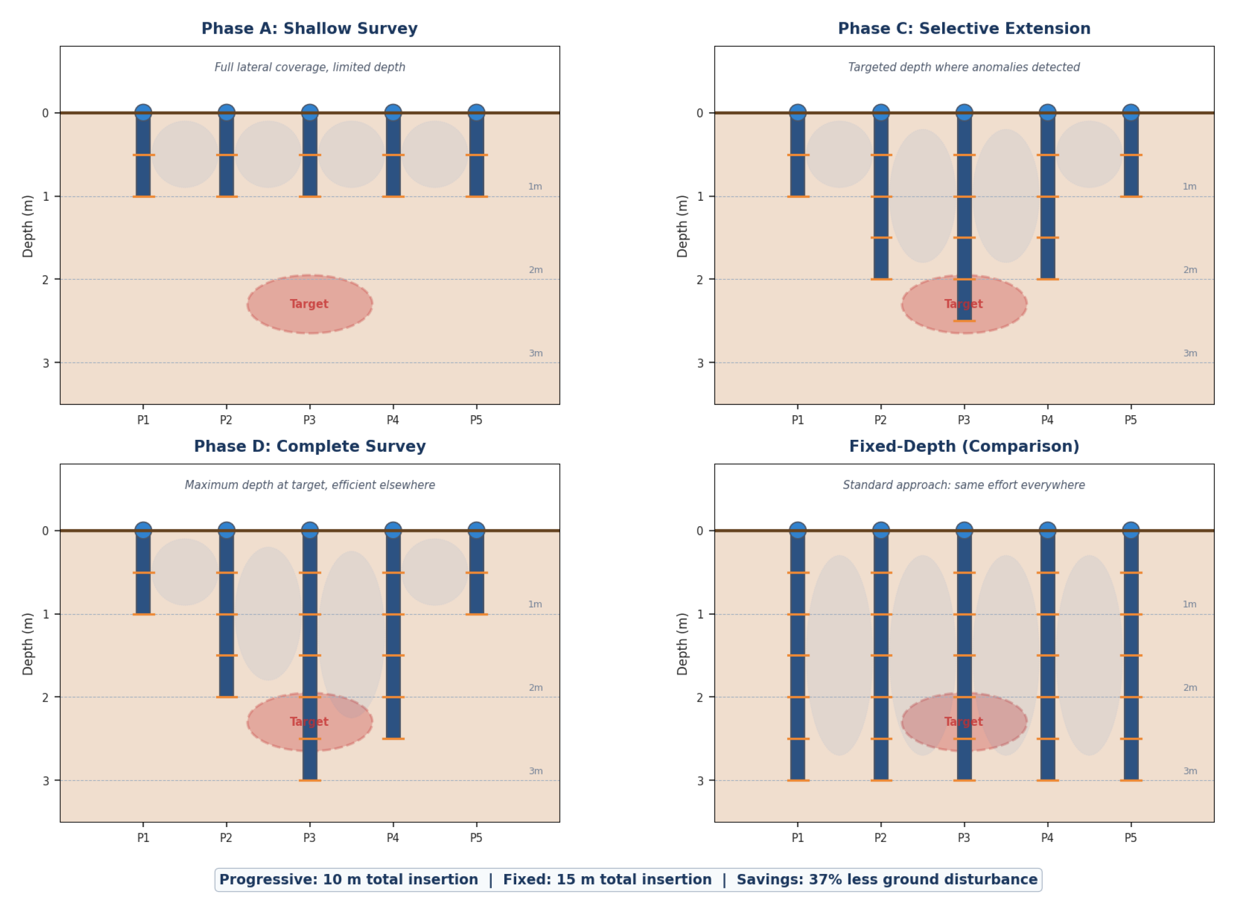
hirt/docs/_freeze/field-guide/progressive-deployment/figure-html/fig-progressive-cross-section-output-1.png
