chadlindell/terrascry/hirt/docs/_freeze/field-guide/progressive-deployment/figure-html/fig-progressive-workflow-output-1.png

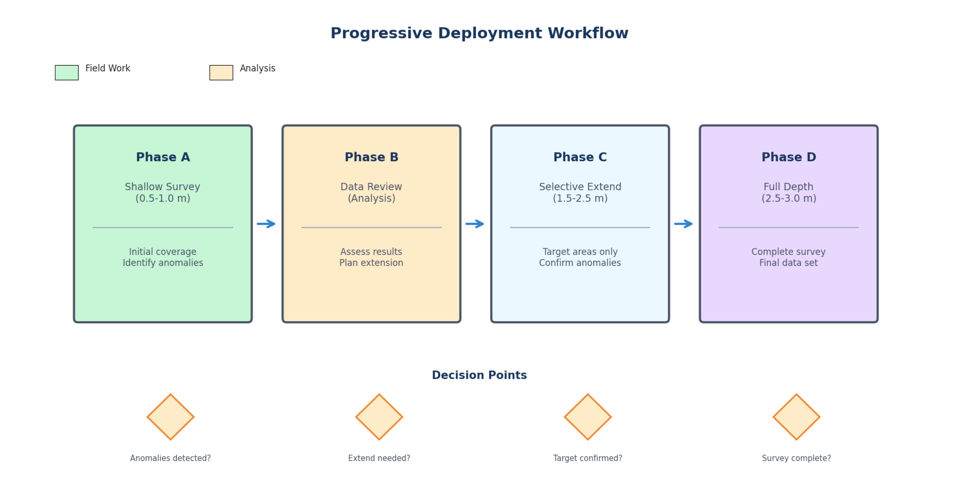
hirt/docs/_freeze/field-guide/progressive-deployment/figure-html/fig-progressive-workflow-output-1.png
