chadlindell/terrascry/hirt/docs/_freeze/field-guide/progressive-deployment/figure-html/fig-uxo-clearance-protocol-output-1.png

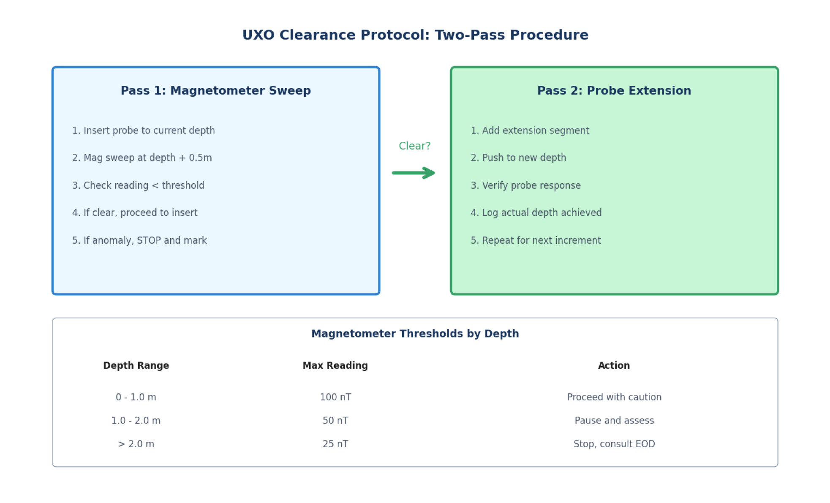
hirt/docs/_freeze/field-guide/progressive-deployment/figure-html/fig-uxo-clearance-protocol-output-1.png
