chadlindell/terrascry/hirt/docs/_freeze/field-guide/scenarios/figure-html/fig-swamp-margin-output-1.png

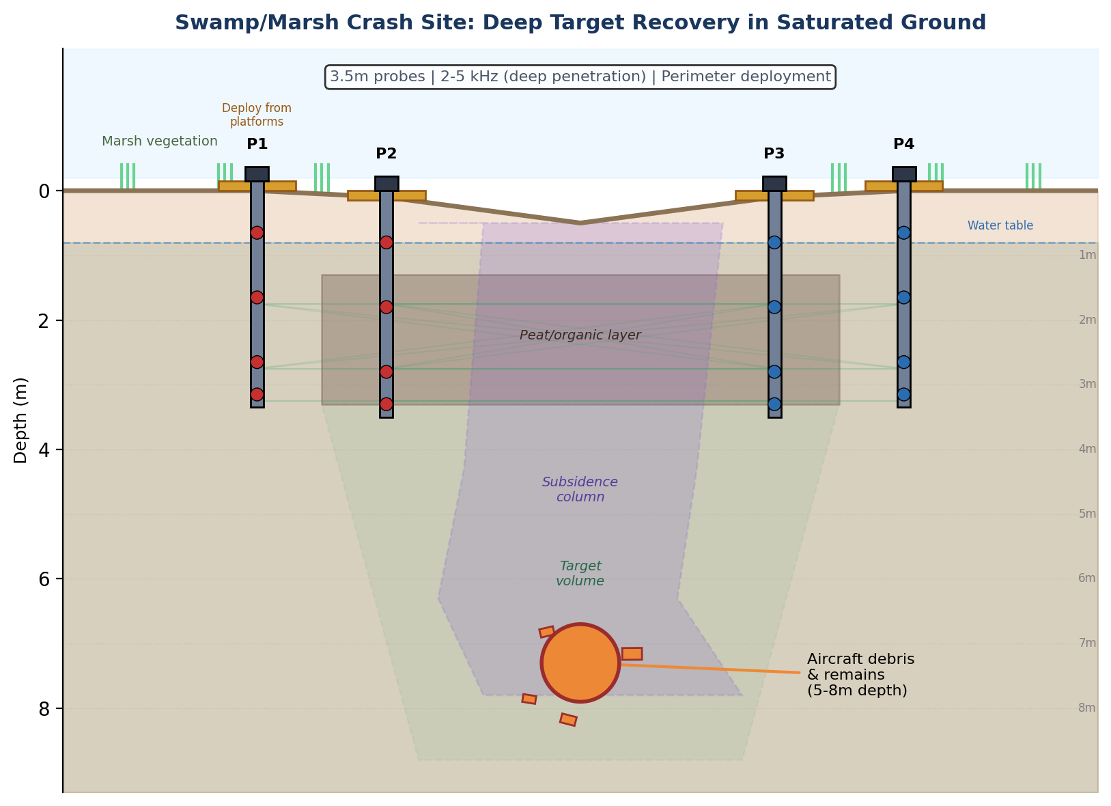
hirt/docs/_freeze/field-guide/scenarios/figure-html/fig-swamp-margin-output-1.png
