chadlindell/terrascry/pathfinder/docs/assets/images/assembly/pathfinder_assembled.png

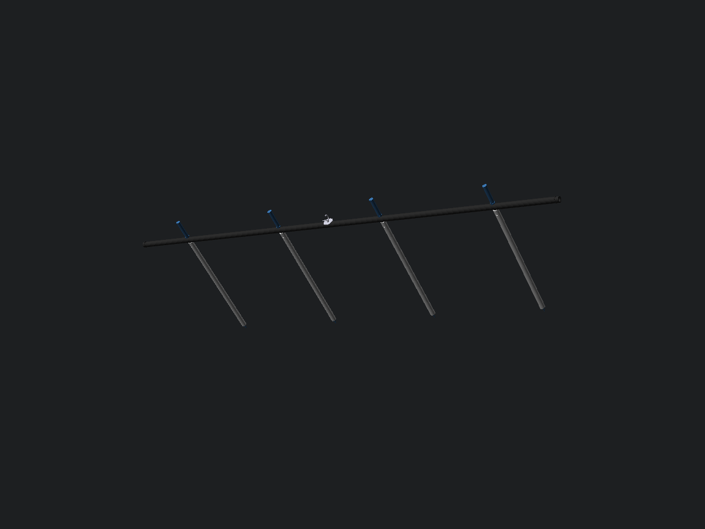
pathfinder/docs/assets/images/assembly/pathfinder_assembled.png
