chadlindell/terrascry/pathfinder/docs/assets/images/assembly/pathfinder_cross_section.png

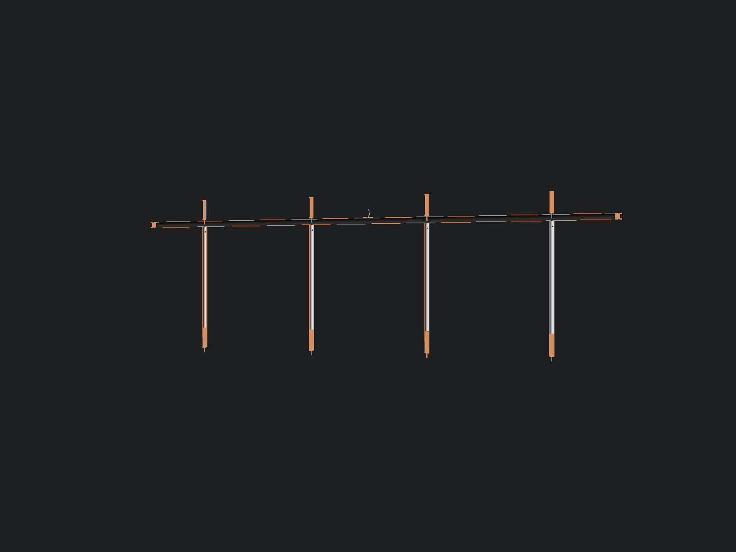
pathfinder/docs/assets/images/assembly/pathfinder_cross_section.png
