chadlindell/terrascry/pathfinder/docs/assets/images/assembly/pathfinder_deployment.png

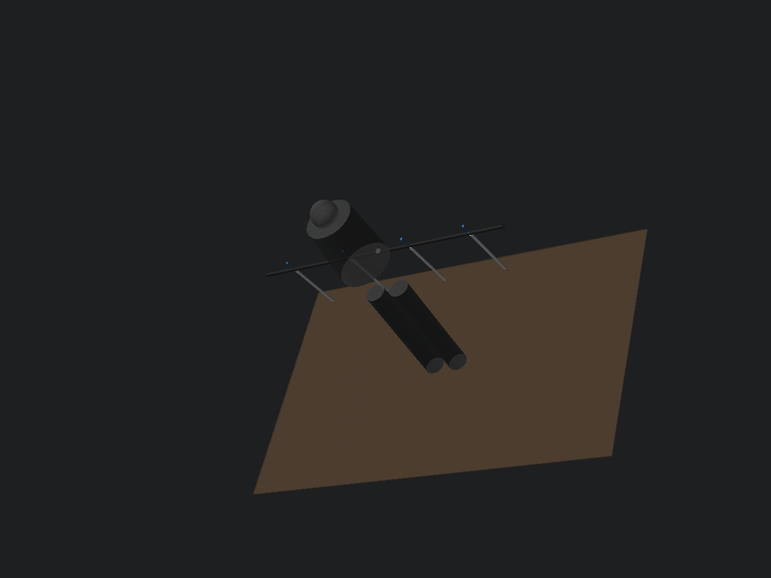
pathfinder/docs/assets/images/assembly/pathfinder_deployment.png
