chadlindell/terrascry/pathfinder/docs/assets/images/assembly/pathfinder_exploded.png

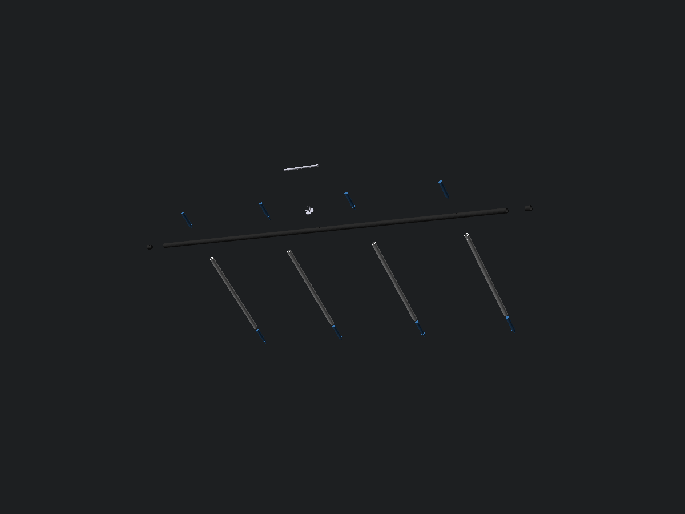
pathfinder/docs/assets/images/assembly/pathfinder_exploded.png
