chadlindell/terrascry/pathfinder/docs/assets/images/assembly/pathfinder_operator.png

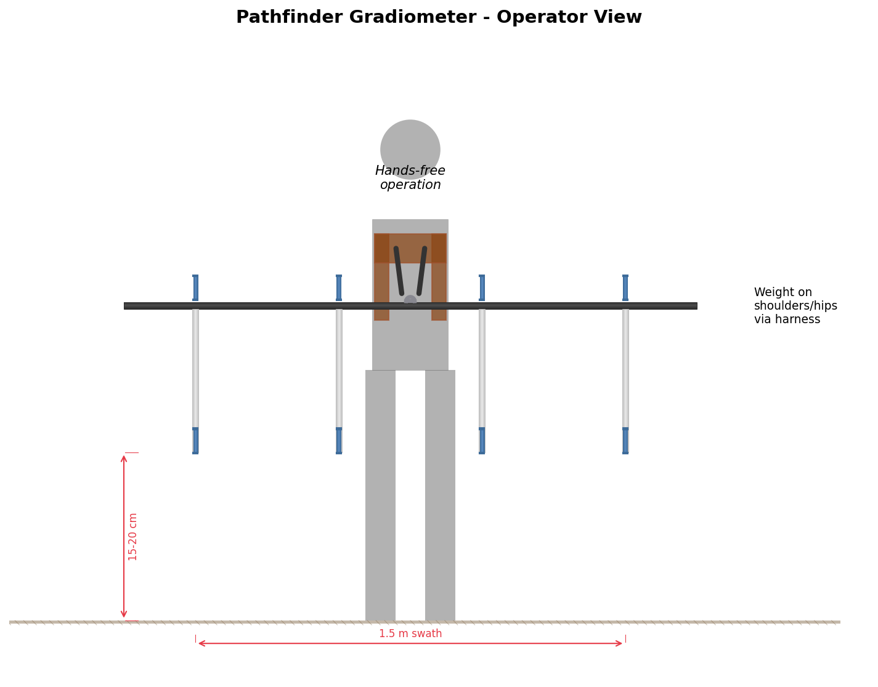
pathfinder/docs/assets/images/assembly/pathfinder_operator.png
