chadlindell/terrascry/pathfinder/docs/assets/images/assembly/pathfinder_side_profile.png

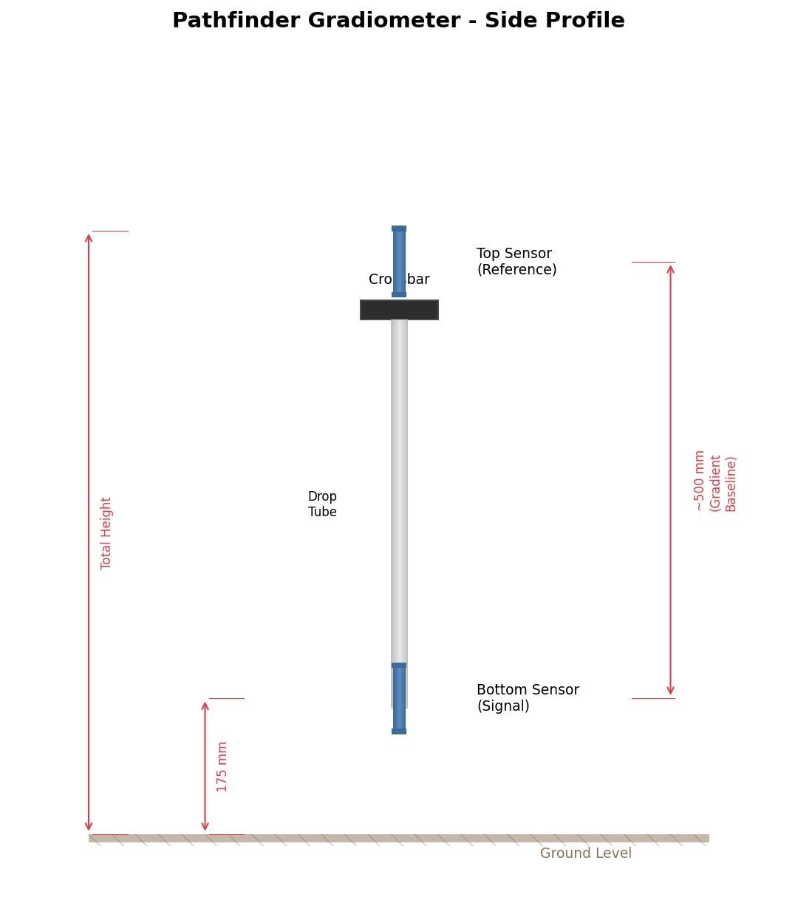
pathfinder/docs/assets/images/assembly/pathfinder_side_profile.png
