chadlindell/terrascry/pathfinder/docs/assets/images/assembly/pathfinder_single_tube.png

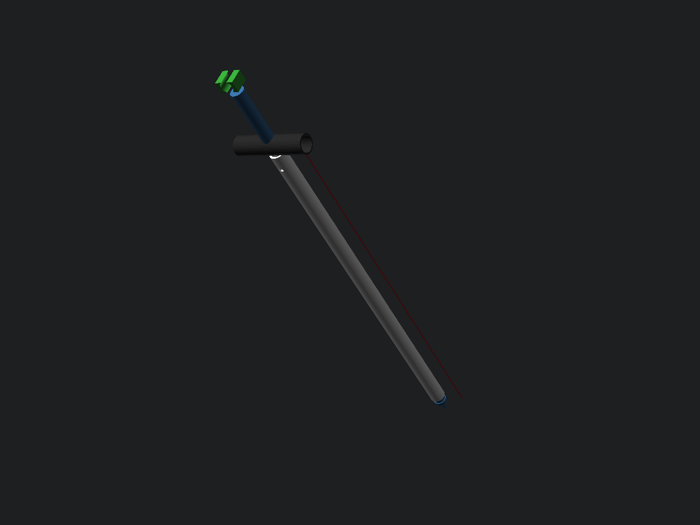
pathfinder/docs/assets/images/assembly/pathfinder_single_tube.png
