chadlindell/terrascry/platform/backend/tests/fixtures/invalid_missing_cols.csv

x | z | temperature
0.0 | 0.0 | 25.1
1.0 | 0.0 | 25.3
2.0 | 0.0 | 25.5
