chadlindell/terrascry/platform/backend/tests/fixtures/invalid_bad_values.csv

x | y | gradient_nt
0.0 | 0.0 | 1.2
abc | 0.0 | 1.5
1.0 | xyz | 2.1
1.5 | 0.0 | bad
