chadlindell/terrascry/platform/backend/tests/fixtures/valid_grid.csv

# TERRASCRY Grid Export
# rows: 3 | cols: 4
# x_min: 0.0 | y_min: 0.0
# dx: 1.0 | dy: 1.0
# unit: nT
x | y | gradient_nt
0.0 | 0.0 | 1.0
1.0 | 0.0 | 2.0
2.0 | 0.0 | 3.0
3.0 | 0.0 | 4.0
0.0 | 1.0 | 5.0
1.0 | 1.0 | 6.0
2.0 | 1.0 | 7.0
3.0 | 1.0 | 8.0
0.0 | 2.0 | 9.0
1.0 | 2.0 | 10.0
2.0 | 2.0 | 11.0
3.0 | 2.0 | 12.0
