chadlindell/terrascry/platform/backend/tests/fixtures/valid_survey.csv

x | y | gradient_nt
0.0 | 0.0 | 1.2
0.5 | 0.0 | 1.5
1.0 | 0.0 | 2.1
1.5 | 0.0 | 3.4
2.0 | 0.0 | 5.8
2.5 | 0.0 | 8.2
3.0 | 0.0 | 12.4
3.5 | 0.0 | 15.1
4.0 | 0.0 | 11.3
4.5 | 0.0 | 7.6
0.0 | 1.0 | 1.1
0.5 | 1.0 | 1.4
1.0 | 1.0 | 2.0
1.5 | 1.0 | 3.2
2.0 | 1.0 | 5.5
2.5 | 1.0 | 7.9
3.0 | 1.0 | 11.8
3.5 | 1.0 | 14.5
4.0 | 1.0 | 10.9
4.5 | 1.0 | 7.2
