chadlindell/terrascry/hirt/_archive/2024-legacy/images/calibration-testing/README.md

# Calibration and Testing Images

This directory will contain images from calibration and testing procedures.

## Planned Content

- Calibration setup photos
- Test target photos
- Measurement results plots
- Quality control documentation
