chadlindell/terrascry/hirt/docs/_freeze/build-guide/calibration/figure-html/fig-air-calibration-setup-output-1.png

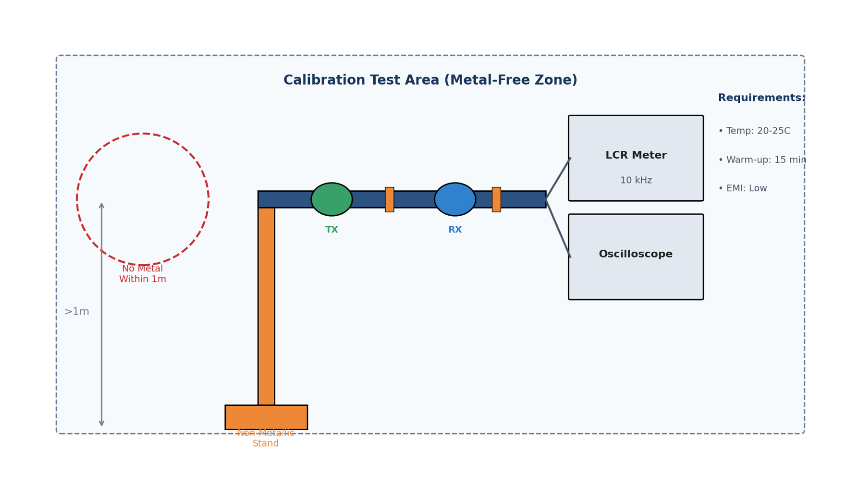
hirt/docs/_freeze/build-guide/calibration/figure-html/fig-air-calibration-setup-output-1.png
