chadlindell/terrascry/hirt/docs/_freeze/build-guide/calibration/figure-html/fig-calibration-hierarchy-output-1.png

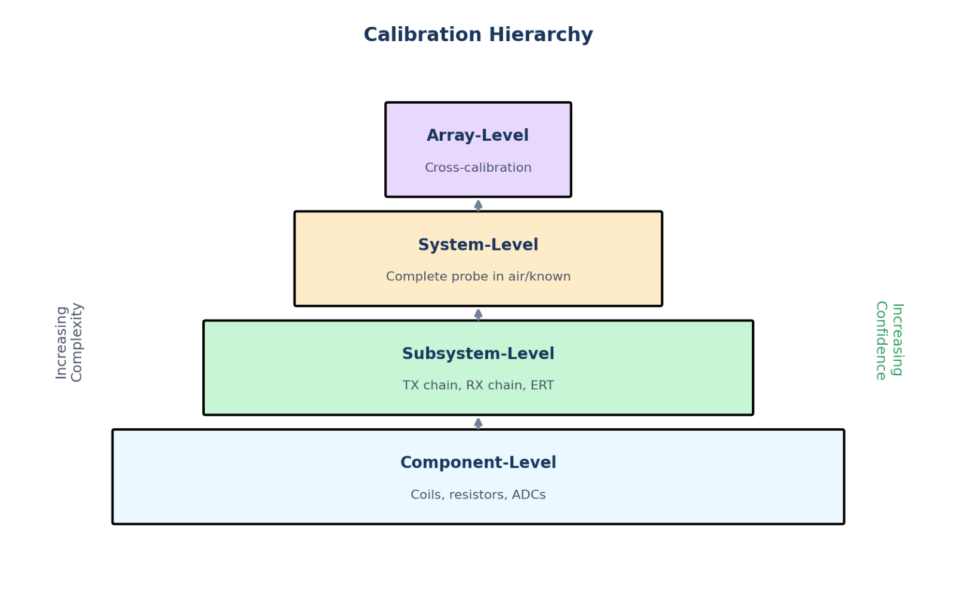
hirt/docs/_freeze/build-guide/calibration/figure-html/fig-calibration-hierarchy-output-1.png
