chadlindell/terrascry/hirt/docs/_freeze/build-guide/mechanical/figure-html/fig-quick-test-setup-output-1.png

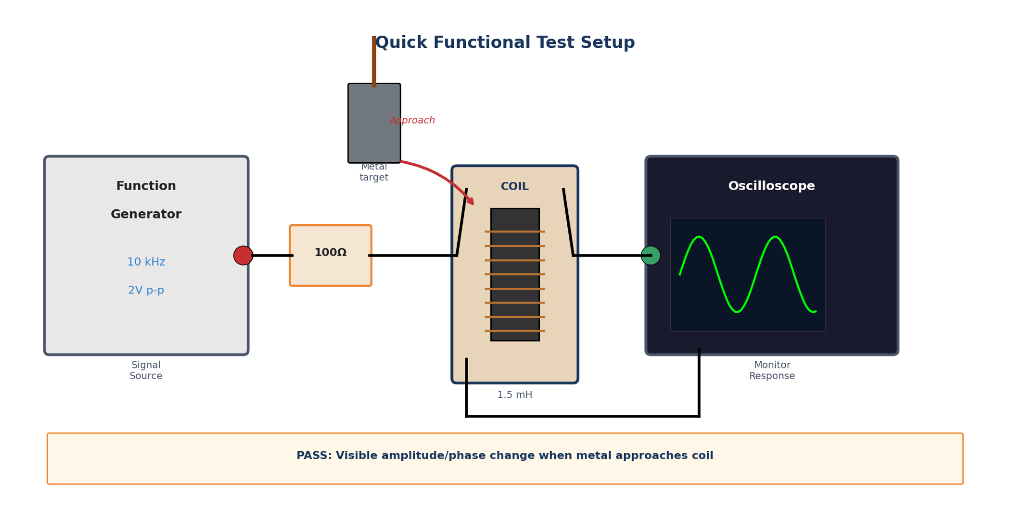
hirt/docs/_freeze/build-guide/mechanical/figure-html/fig-quick-test-setup-output-1.png
