chadlindell/terrascry/hirt/docs/_freeze/build-guide/testing/figure-html/fig-pass-fail-criteria-output-1.png

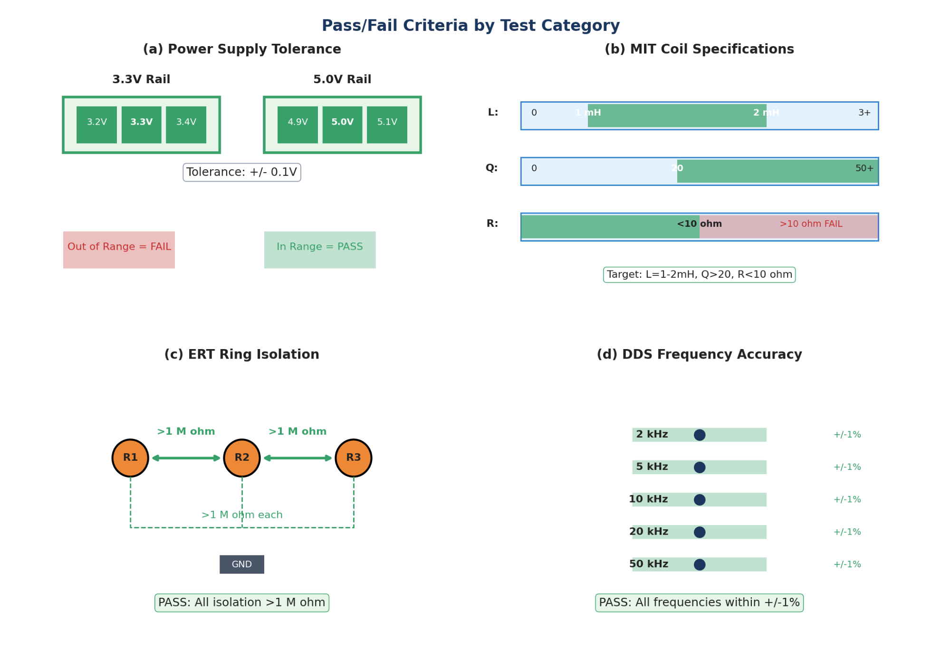
hirt/docs/_freeze/build-guide/testing/figure-html/fig-pass-fail-criteria-output-1.png
