chadlindell/terrascry/hirt/docs/_freeze/build-guide/testing/figure-html/fig-test-results-template-output-1.png

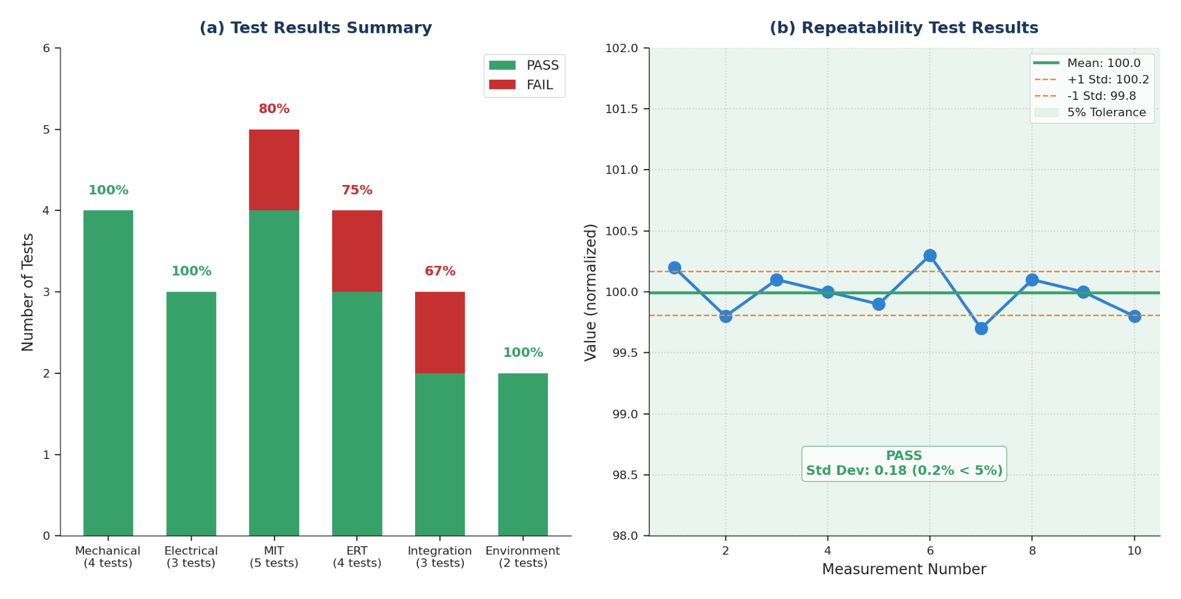
hirt/docs/_freeze/build-guide/testing/figure-html/fig-test-results-template-output-1.png
