chadlindell/terrascry/hirt/docs/_freeze/build-guide/testing/figure-html/fig-test-setup-output-1.png

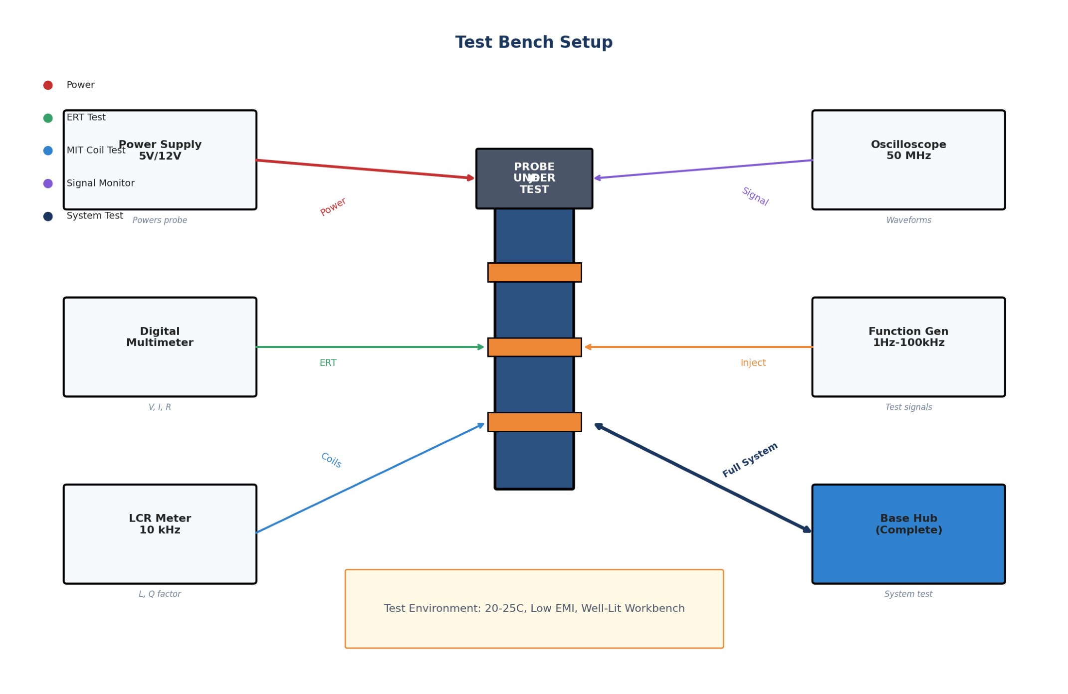
hirt/docs/_freeze/build-guide/testing/figure-html/fig-test-setup-output-1.png
