chadlindell/terrascry/hirt/docs/_freeze/build-guide/testing/figure-html/fig-verification-workflow-output-1.png

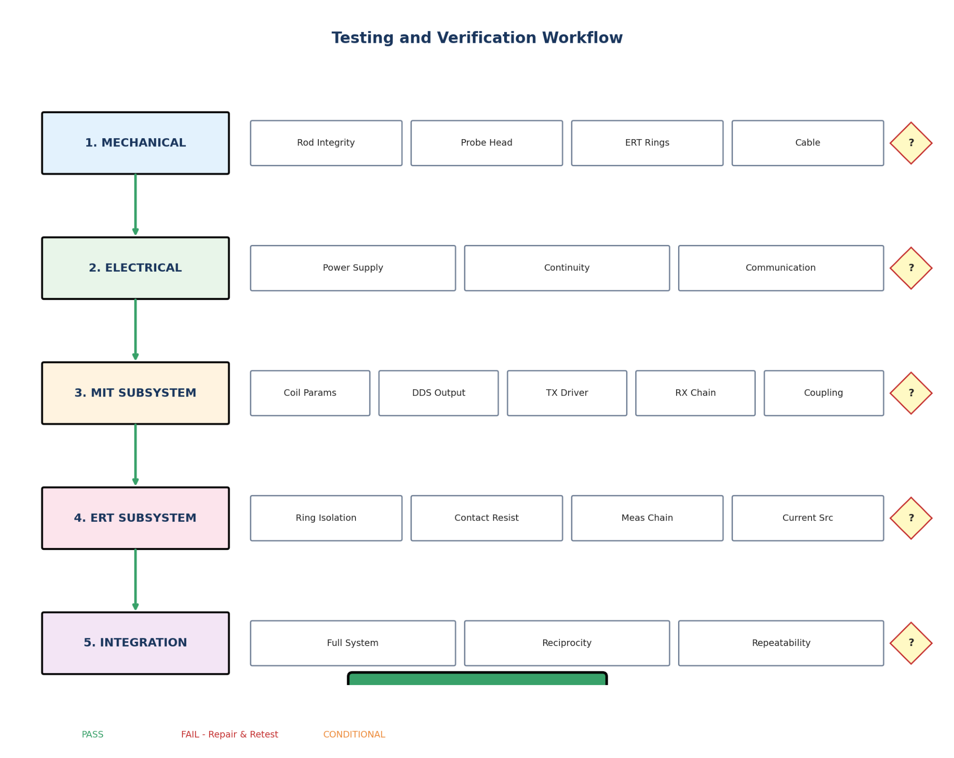
hirt/docs/_freeze/build-guide/testing/figure-html/fig-verification-workflow-output-1.png
