chadlindell/terrascry/hirt/docs/_freeze/field-guide/deployment/figure-html/fig-measurement-sequence-output-1.png

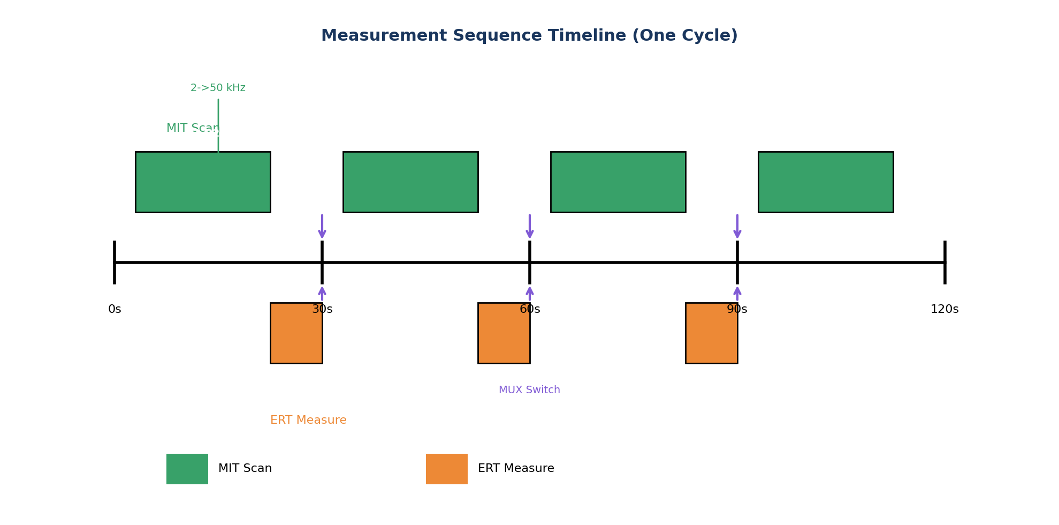
hirt/docs/_freeze/field-guide/deployment/figure-html/fig-measurement-sequence-output-1.png
