chadlindell/terrascry/hirt/docs/diagrams/subsurface.py

"""
HIRT PDF Generator - Subsurface Diagrams Module

Functions for creating ground layers, probes, ray paths, and cross-section diagrams.
Enhanced with realistic soil textures, Fresnel zones, and improved target rendering.
"""

import matplotlib
try:
    get_ipython()
except NameError:
    matplotlib.use('Agg')
import matplotlib.pyplot as plt
import matplotlib.patches as mpatches
from matplotlib.patches import (
    FancyBboxPatch, Circle, Rectangle, Polygon, Ellipse, FancyArrowPatch
)
import matplotlib.colors as mcolors
import numpy as np
import random
from io import BytesIO

# Import utility functions from parent module
from . import (
    draw_soil_texture_advanced,
    draw_sphere_gradient,
    WONG_PALETTE,
    COLORS as PARENT_COLORS
)

# Configure Matplotlib for Scientific Publication Style
plt.rcParams.update({
    'font.family': 'sans-serif',
    'font.sans-serif': ['Arial', 'Helvetica', 'DejaVu Sans'],
    'font.size': 8,
    'axes.linewidth': 0.5,
    'lines.linewidth': 0.8,
    'patch.linewidth': 0.5,
    'text.color': '#222222',
    'axes.labelcolor': '#222222',
    'xtick.color': '#222222',
    'ytick.color': '#222222',
})

# Color palette (Muted Academic) - Extended with Wong palette integration
COLORS = {
    'primary': '#1a365d',      # Navy
    'secondary': '#2c5282',    # Muted Blue
    'accent': '#3182ce',       # Sky Blue
    'success': '#2f855a',      # Forest Green (Darker)
    'warning': '#c53030',      # Brick Red
    'ground_tan': '#d4a373',
    'orange': '#c05621',
    'purple': '#6b46c1',
    'gray_dark': '#2d3748',
    'gray_med': '#718096',
    'gray_light': '#cbd5e0',
    'sky': '#e8f4f8',
    'ground_dark': '#654321',
    'tx_coil': '#2f855a',
    'rx_coil': '#3182ce',
    'ert_ring': '#c05621',
    'probe_body': '#2c5282',
    'connector': '#4a5568',
    # Wong colorblind-safe colors for sensitivity visualization
    'fresnel_high': WONG_PALETTE['bluish_green'],
    'fresnel_med': WONG_PALETTE['sky_blue'],
    'fresnel_low': WONG_PALETTE['yellow'],
    'eddy_current': WONG_PALETTE['vermillion'],
    'anomaly_halo': WONG_PALETTE['reddish_purple'],
}


def draw_soil_texture(ax, xmin, xmax, ytop, ybottom, type='sand', density=0.5):
    """
    Draw realistic soil texture patterns.

    This is a legacy function maintained for backwards compatibility.
    For enhanced rendering, use draw_soil_texture_advanced() from the parent module.
    """
    width = xmax - xmin
    height = abs(ytop - ybottom)
    area = width * height

    if type == 'sand':
        # Random dots
        n_dots = int(50 * density * area)
        if n_dots > 0:
            x = np.random.uniform(xmin, xmax, n_dots)
            y = np.random.uniform(ybottom, ytop, n_dots)
            ax.scatter(x, y, s=0.5, c='#8c6239', alpha=0.4, marker='.', zorder=1)

    elif type == 'clay':
        # Horizontal dashes
        n_dashes = int(20 * density * area)
        if n_dashes > 0:
            x = np.random.uniform(xmin, xmax, n_dashes)
            y = np.random.uniform(ybottom, ytop, n_dashes)
            # Create short horizontal lines
            for i in range(n_dashes):
                ax.plot([x[i], x[i] + 0.2], [y[i], y[i]], color='#5d4037', lw=0.5, alpha=0.3, zorder=1)

    elif type == 'loam':
        # Mix of dots and dashes
        draw_soil_texture(ax, xmin, xmax, ytop, ybottom, 'sand', density * 0.5)
        draw_soil_texture(ax, xmin, xmax, ytop, ybottom, 'clay', density * 0.5)


def draw_gravel_inclusions(ax, xmin, xmax, ytop, ybottom, density=1.0, seed=None):
    """
    Draw scattered gravel/rock inclusions as small polygons.

    Args:
        ax: matplotlib Axes object
        xmin, xmax: Horizontal extent
        ytop, ybottom: Vertical extent
        density: Relative density multiplier
        seed: Random seed for reproducibility
    """
    if seed is not None:
        np.random.seed(seed)

    width = xmax - xmin
    height = abs(ytop - ybottom)
    n_gravel = int(width * height * 2 * density)

    for _ in range(n_gravel):
        # Random position
        gx = np.random.uniform(xmin, xmax)
        gy = np.random.uniform(min(ytop, ybottom), max(ytop, ybottom))

        # Random size and shape (irregular polygon)
        size = np.random.uniform(0.03, 0.12)
        n_vertices = np.random.randint(4, 8)
        angles = np.sort(np.random.uniform(0, 2*np.pi, n_vertices))
        radii = size * np.random.uniform(0.6, 1.0, n_vertices)

        vertices = [(gx + r * np.cos(a), gy + r * np.sin(a))
                    for r, a in zip(radii, angles)]

        # Random gray color
        gray = np.random.uniform(0.35, 0.65)
        gravel = Polygon(vertices, facecolor=(gray, gray, gray),
                        edgecolor=(gray*0.7, gray*0.7, gray*0.7),
                        linewidth=0.3, alpha=0.7, zorder=2)
        ax.add_patch(gravel)


def draw_probe(ax, x, top_y, length, components=None, show_label=True, label=None):
    """
    Draw a single probe with internal components.

    Args:
        ax: matplotlib Axes object
        x: X position of probe center
        top_y: Y position of probe top (usually 0 for ground surface)
        length: Total probe length (positive value, extends downward)
        components: List of dicts with keys:
            - 'depth': depth from top (positive)
            - 'type': 'tx', 'rx', 'ert', 'joint', 'tip'
            - 'size': optional size override
        show_label: Whether to show probe label
        label: Custom label text

    Returns:
        Dict with component positions for reference
    """
    probe_width = 0.16
    half_width = probe_width / 2

    # Main probe body
    ax.add_patch(Rectangle((x - half_width, top_y - length), probe_width, length,
                           color=COLORS['probe_body'], ec='black', lw=1, zorder=10))

    # Junction box at top
    ax.add_patch(Rectangle((x - 0.2, top_y - 0.1), 0.4, 0.3,
                           color=COLORS['connector'], ec='black', lw=1, zorder=11))

    positions = {}

    if components:
        for comp in components:
            depth = comp['depth']
            comp_type = comp['type']
            size = comp.get('size', 0.12)
            y_pos = top_y - depth

            if comp_type == 'tx':
                ax.add_patch(Circle((x, y_pos), size, color=COLORS['tx_coil'],
                                   ec='black', lw=1, zorder=12))
                positions['tx'] = positions.get('tx', []) + [(x, y_pos)]
            elif comp_type == 'rx':
                ax.add_patch(Circle((x, y_pos), size, color=COLORS['rx_coil'],
                                   ec='black', lw=1, zorder=12))
                positions['rx'] = positions.get('rx', []) + [(x, y_pos)]
            elif comp_type == 'ert':
                ax.add_patch(Rectangle((x - 0.15, y_pos - 0.05), 0.3, 0.1,
                                       color=COLORS['ert_ring'], ec='black', lw=0.5, zorder=12))
                positions['ert'] = positions.get('ert', []) + [(x, y_pos)]
            elif comp_type == 'joint':
                ax.add_patch(Rectangle((x - half_width, y_pos - 0.04), probe_width, 0.08,
                                       color=COLORS['gray_light'], ec='black', lw=0.5, zorder=12))
            elif comp_type == 'tip':
                # Pointed tip
                tip_y = top_y - length
                points = [(x - half_width, tip_y + 0.15),
                         (x + half_width, tip_y + 0.15),
                         (x, tip_y)]
                ax.add_patch(Polygon(points, color=COLORS['primary'],
                                    ec='black', lw=1, zorder=12))

    if show_label and label:
        ax.text(x, top_y + 0.35, label, ha='center', fontsize=9, fontweight='bold')

    return positions


def draw_probe_array(ax, positions, top_y=0, length=3.0, components=None, labels=None):
    """
    Draw an array of probes.

    Args:
        ax: matplotlib Axes object
        positions: List of x positions for probes
        top_y: Y position of ground surface
        length: Probe length
        components: Component spec (same for all probes) or list of specs
        labels: List of labels or None

    Returns:
        List of component position dicts
    """
    all_positions = []

    for i, x in enumerate(positions):
        label = labels[i] if labels else f'P{i+1}'
        comp = components[i] if isinstance(components, list) else components
        pos = draw_probe(ax, x, top_y, length, comp, show_label=True, label=label)
        all_positions.append(pos)

    return all_positions


def draw_fresnel_zone(ax, x1, y1, x2, y2, wavelength=0.5, zone_number=1, color=None, alpha=0.15):
    """
    Draw first Fresnel zone ellipse around a ray path.

    The Fresnel zone is the elliptical region where most signal energy propagates.
    Width = sqrt(n * wavelength * distance) where n is zone number.

    Args:
        ax: matplotlib Axes object
        x1, y1: Start point coordinates
        x2, y2: End point coordinates
        wavelength: Signal wavelength in meters (default 0.5m for typical EMI)
        zone_number: Fresnel zone number (1 = first zone)
        color: Fill color (default: based on sensitivity)
        alpha: Transparency

    Returns:
        Ellipse patch object
    """
    # Calculate ray path properties
    dx = x2 - x1
    dy = y2 - y1
    distance = np.sqrt(dx**2 + dy**2)
    angle = np.degrees(np.arctan2(dy, dx))

    # First Fresnel zone radius at midpoint
    # r = sqrt(n * lambda * d1 * d2 / (d1 + d2)) where d1 = d2 = distance/2
    fresnel_radius = np.sqrt(zone_number * wavelength * distance / 4)

    # Midpoint
    mx = (x1 + x2) / 2
    my = (y1 + y2) / 2

    # Default color based on zone number (sensitivity indicator)
    if color is None:
        if zone_number == 1:
            color = COLORS['fresnel_high']
        elif zone_number == 2:
            color = COLORS['fresnel_med']
        else:
            color = COLORS['fresnel_low']

    # Draw ellipse (width = distance, height = 2 * fresnel_radius)
    ellipse = Ellipse((mx, my), distance, 2 * fresnel_radius,
                      angle=angle, facecolor=color, edgecolor=color,
                      alpha=alpha, linewidth=0.5, linestyle='--', zorder=3)
    ax.add_patch(ellipse)
    return ellipse
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
