chadlindell/terrascry/pathfinder/firmware/test/test_adc/test_adc.cpp

/**
 * Pathfinder ADC Saturation Handling Tests
 *
 * Tests the checkSaturation() logic: readings above ADC_SATURATION_THRESHOLD
 * (default 32000) trigger a saturation counter. Both positive and negative
 * extremes are tested.
 *
 * Runs on host via PlatformIO native environment (no hardware needed).
 */

#include <unity.h>
#include <stdint.h>

// Reproduce the threshold from config.h
static const int16_t ADC_SATURATION_THRESHOLD = 32000;

// Reproduce saturation counter (mirrors global adcSaturationCount in main.cpp)
static uint16_t adcSaturationCount;

// Extracted from main.cpp checkSaturation()
static void checkSaturation(int16_t value) {
    if (value > ADC_SATURATION_THRESHOLD || value < -ADC_SATURATION_THRESHOLD) {
        adcSaturationCount++;
    }
}

void setUp(void) {
    adcSaturationCount = 0;
}

void tearDown(void) {
    // nothing
}

// --- Tests: positive saturation ---

void test_adc_at_threshold_triggers_saturation(void) {
    // Value of 32001 is above threshold -> should trigger
    checkSaturation(32001);
    TEST_ASSERT_EQUAL_UINT16(1, adcSaturationCount);
}

void test_adc_exactly_at_threshold_does_not_trigger(void) {
    // Value exactly at threshold boundary (32000) should NOT trigger
    // because the check is strictly greater than
    checkSaturation(32000);
    TEST_ASSERT_EQUAL_UINT16(0, adcSaturationCount);
}

void test_adc_well_below_threshold_does_not_trigger(void) {
    checkSaturation(16000);
    TEST_ASSERT_EQUAL_UINT16(0, adcSaturationCount);
}

void test_adc_zero_does_not_trigger(void) {
    checkSaturation(0);
    TEST_ASSERT_EQUAL_UINT16(0, adcSaturationCount);
}

void test_adc_max_positive_triggers(void) {
    checkSaturation(32767);
    TEST_ASSERT_EQUAL_UINT16(1, adcSaturationCount);
}

// --- Tests: negative saturation ---

void test_adc_negative_beyond_threshold_triggers(void) {
    checkSaturation(-32001);
    TEST_ASSERT_EQUAL_UINT16(1, adcSaturationCount);
}
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
